jharvey/Cinch_enclosure_template/pictures/modeice_case_iso.jpg

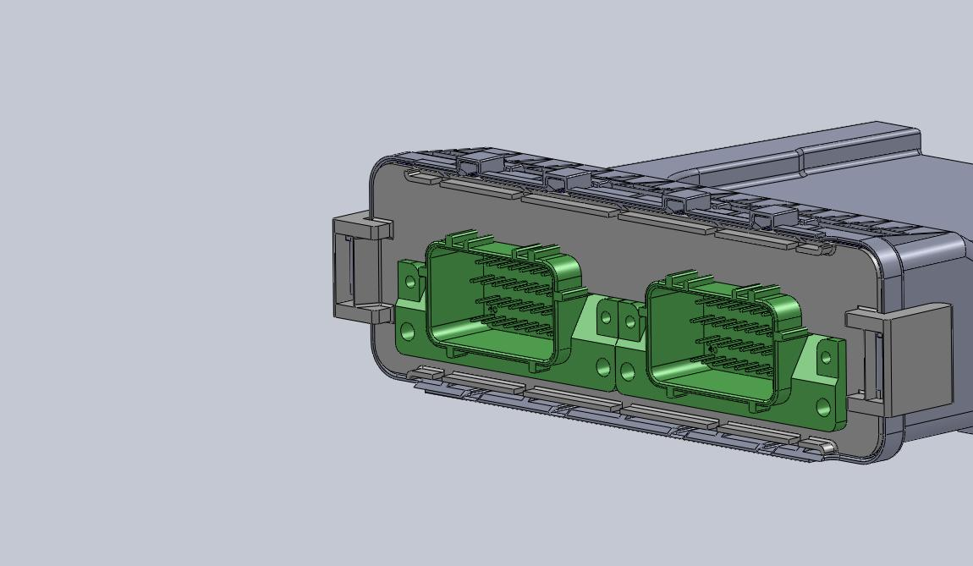
pictures/modeice_case_iso.jpg
