jharvey/Cinch_enclosure_template/pictures/modeice_case_pcb_edge_opening_rubber.jpg

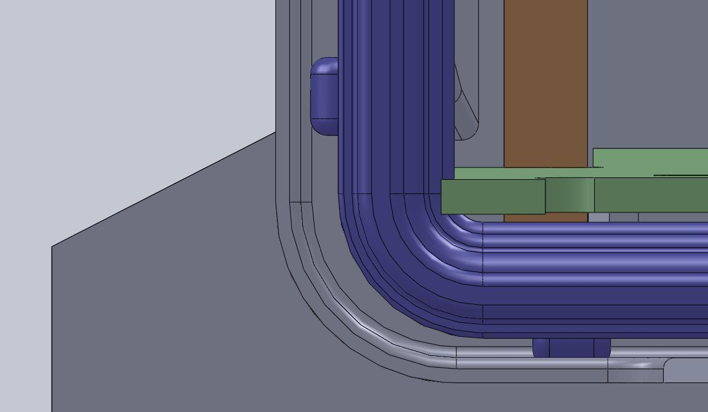
pictures/modeice_case_pcb_edge_opening_rubber.jpg
