jharvey/Cinch_enclosure_template/KICAD_Project/PCB-modules/MPX4100A/puma_topview.png

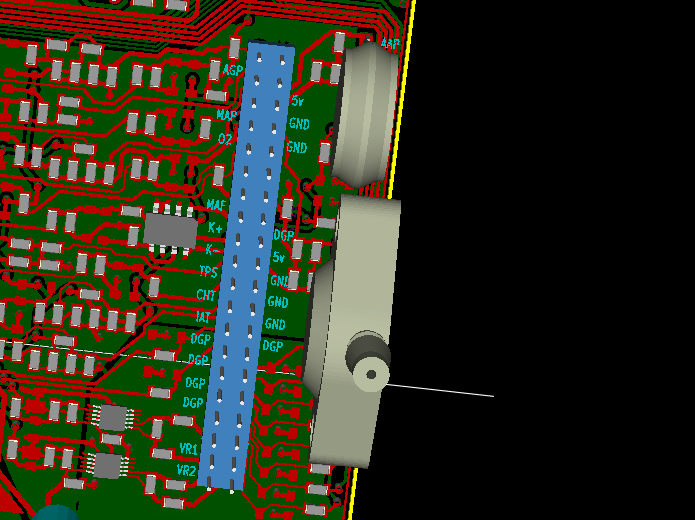
KICAD_Project/PCB-modules/MPX4100A/puma_topview.png
