jharvey/Cinch_enclosure_template/KICAD_Project/PCB-modules/MPX4100A/UNIBODY_CELL.PNG

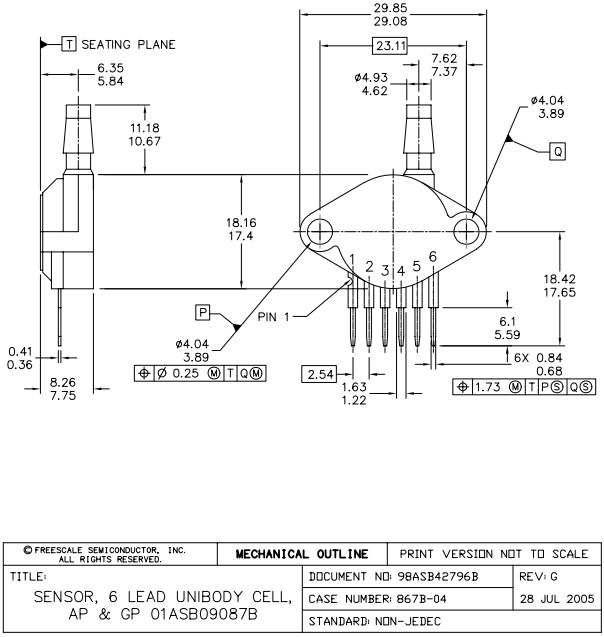
KICAD_Project/PCB-modules/MPX4100A/UNIBODY_CELL.PNG
