jharvey/Cinch_enclosure_template/KICAD_Project/PCB-modules/MPX4100A/UNIBODY_STOVE-PIPE.PNG

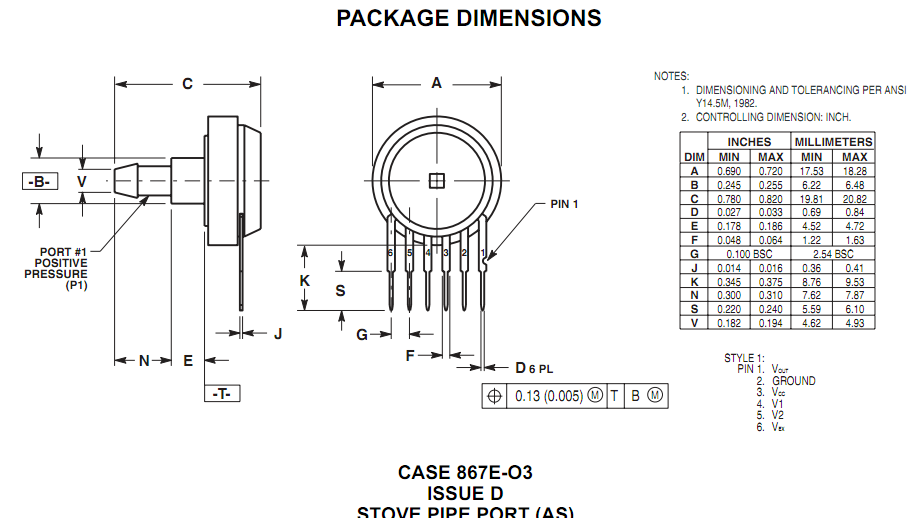
KICAD_Project/PCB-modules/MPX4100A/UNIBODY_STOVE-PIPE.PNG
