jharvey/Cinch_enclosure_template/KICAD_Project/PCB-modules/pololu/0J1418.600.jpg

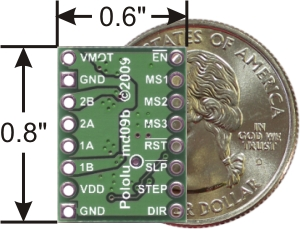
KICAD_Project/PCB-modules/pololu/0J1418.600.jpg
