jharvey/Cinch_enclosure_template/pictures/angled_layout_view.png

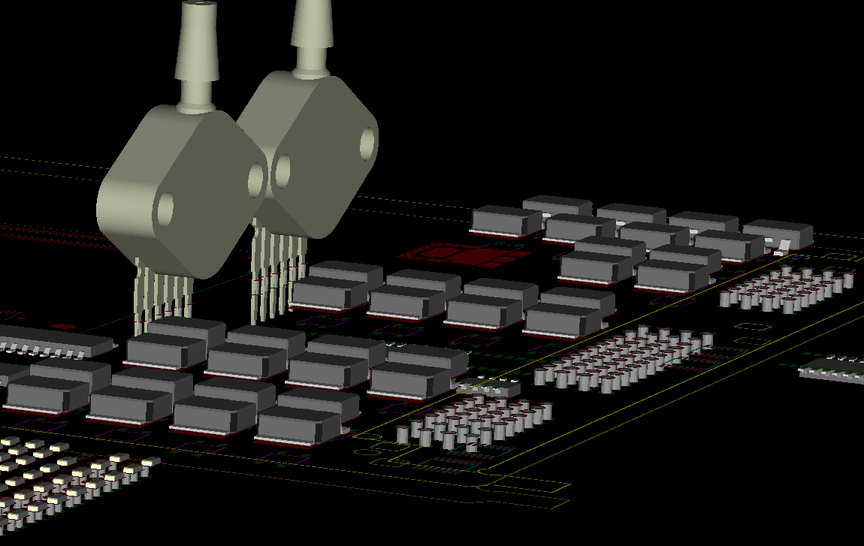
pictures/angled_layout_view.png
