jharvey/Cinch_enclosure_template/pictures/cinch_spring_clips2.png

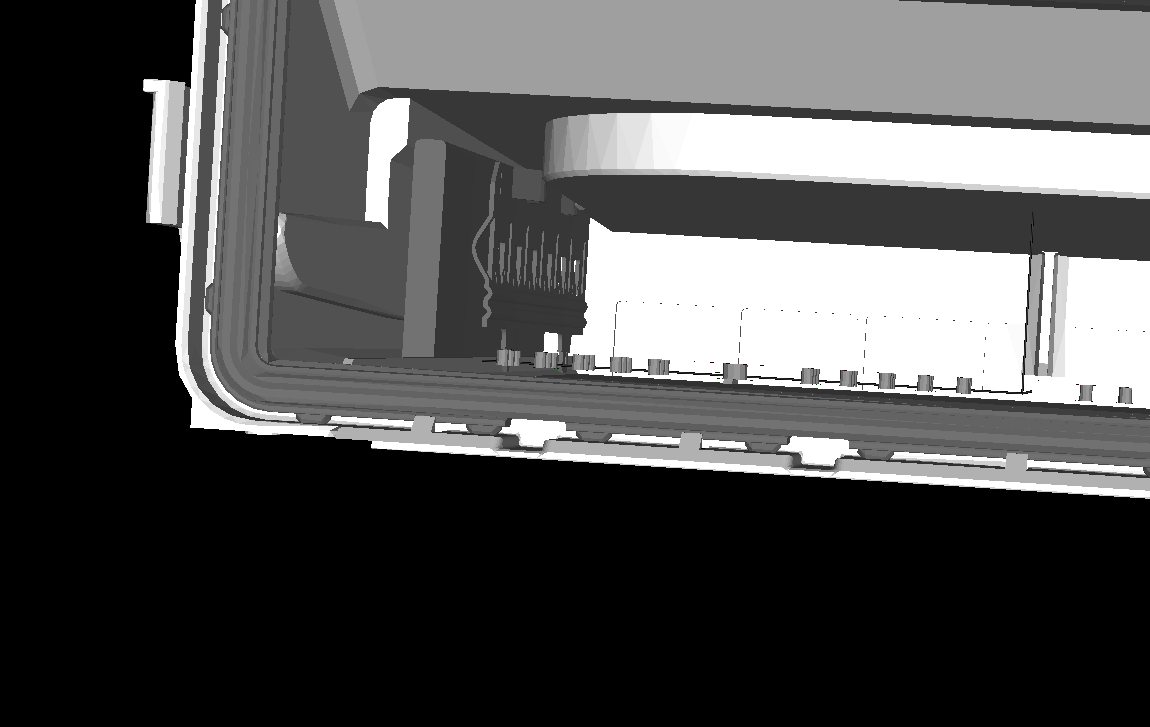
pictures/cinch_spring_clips2.png
