jharvey/Cinch_enclosure_template/pictures/cinch_start.png

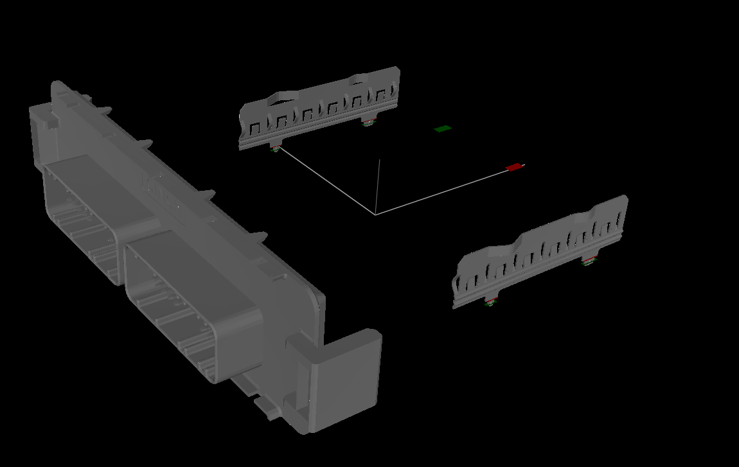
pictures/cinch_start.png
