jharvey/Cinch_enclosure_template/pictures/cinch_start_w-case.png

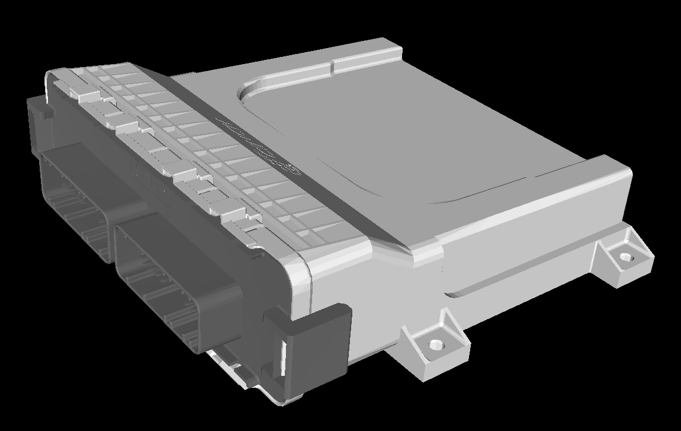
pictures/cinch_start_w-case.png
