jharvey/Cinch_enclosure_template/pictures/GND_PLANE_PCB_DRAFT.PNG

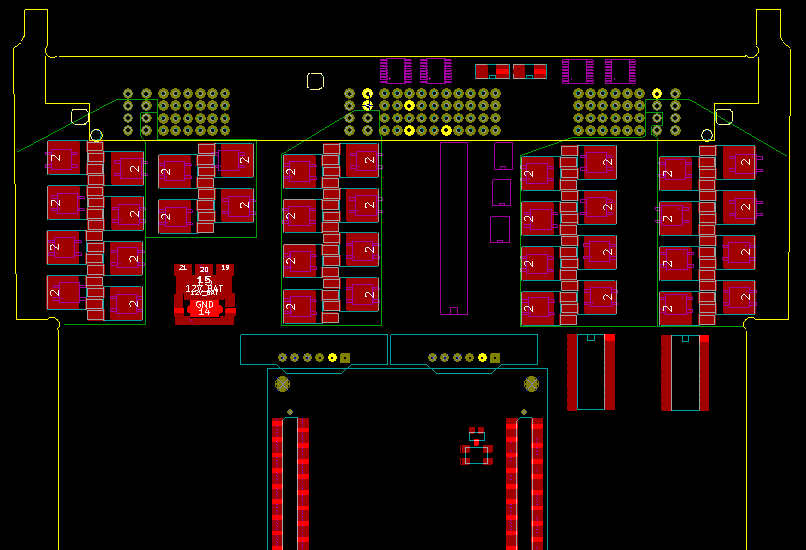
pictures/GND_PLANE_PCB_DRAFT.PNG
