jharvey/Cinch_enclosure_template/pictures/INJ-IGN_opto-drive.PNG

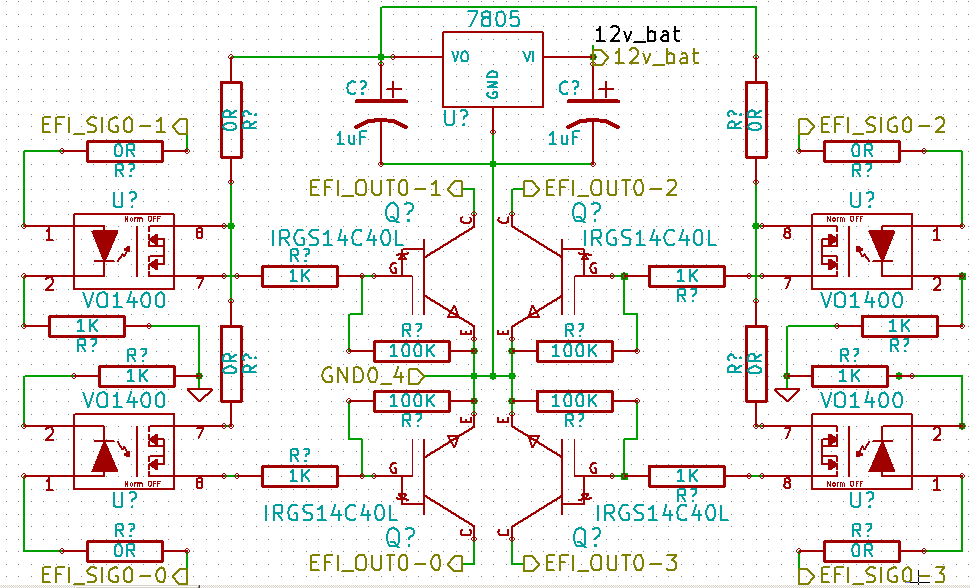
pictures/INJ-IGN_opto-drive.PNG
