jharvey/Cinch_enclosure_template/pictures/layout_top_view.PNG

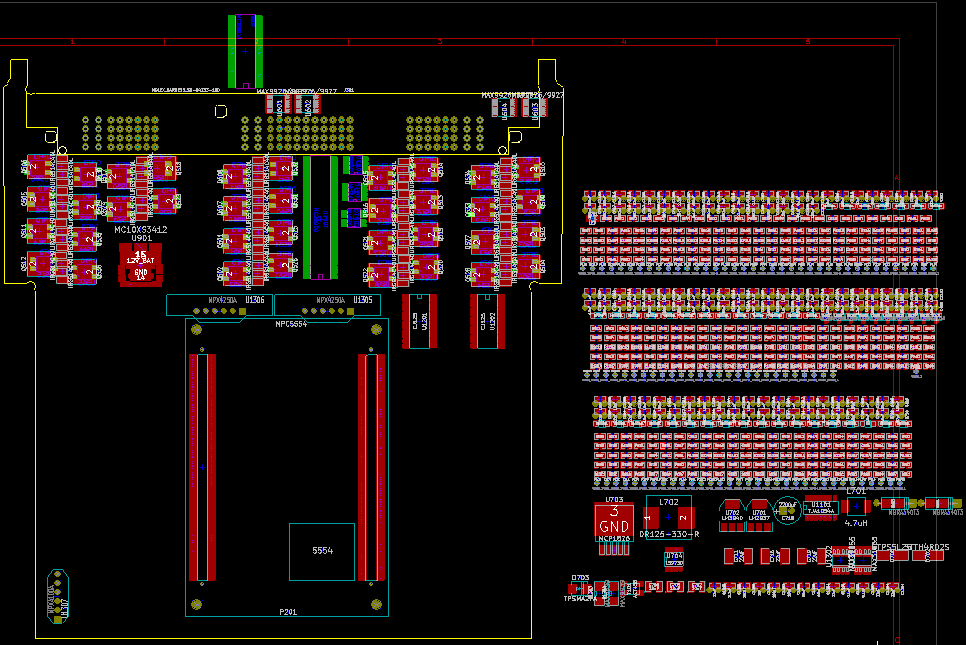
pictures/layout_top_view.PNG
