jharvey/Cinch_enclosure_template/pictures/layout_top_view_2.PNG

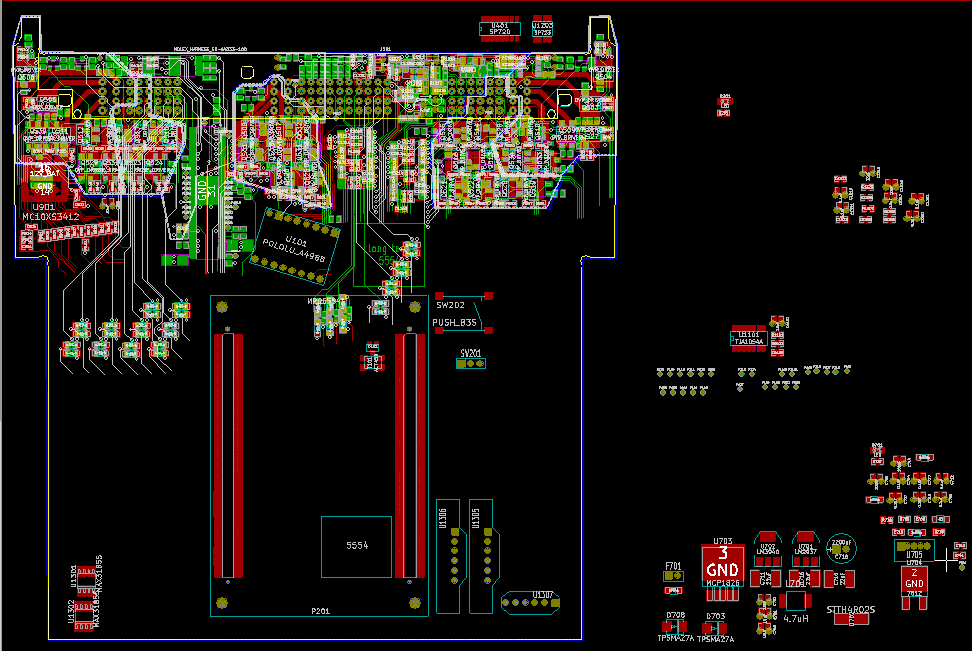
pictures/layout_top_view_2.PNG
