jharvey/Cinch_enclosure_template/pictures/modeice_case_face_plate_cut.jpg

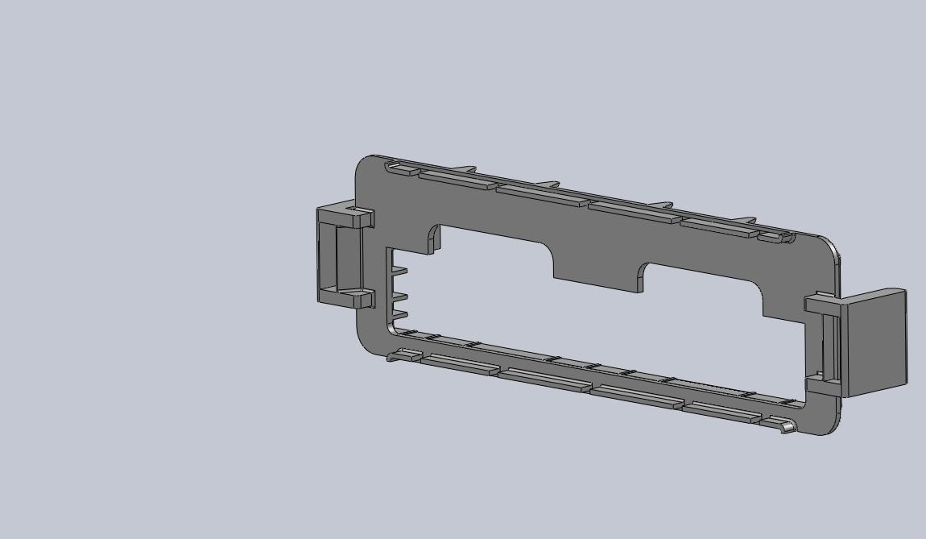
pictures/modeice_case_face_plate_cut.jpg
