jharvey/Cinch_enclosure_template/pictures/modeice_case_iso1.jpg

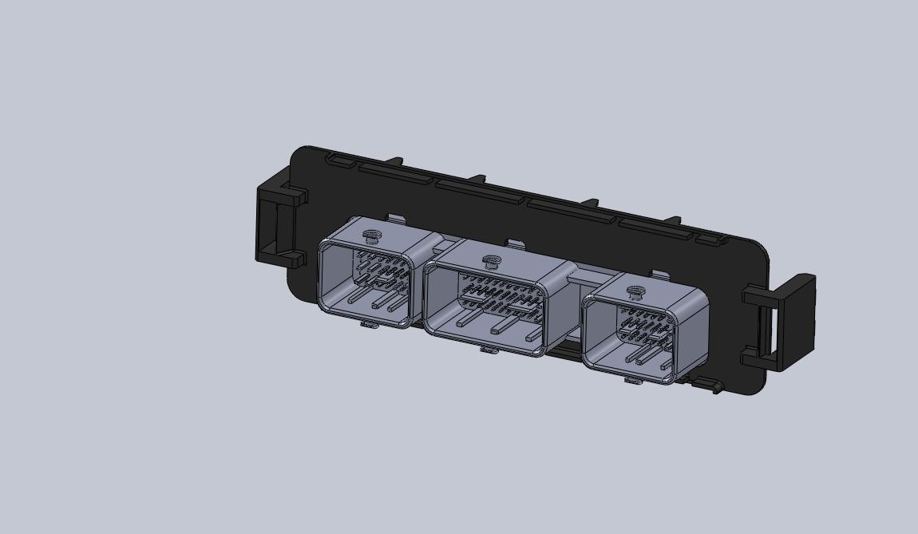
pictures/modeice_case_iso1.jpg
