jharvey/Cinch_enclosure_template/pictures/modeice_case_iso2.jpg

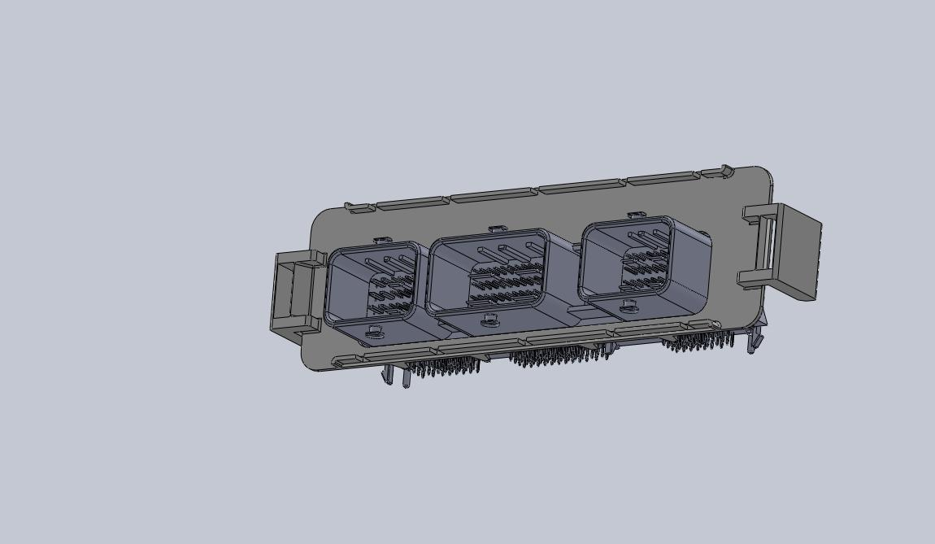
pictures/modeice_case_iso2.jpg
