jharvey/Cinch_enclosure_template/pictures/modeice_case_iso_cut.jpg

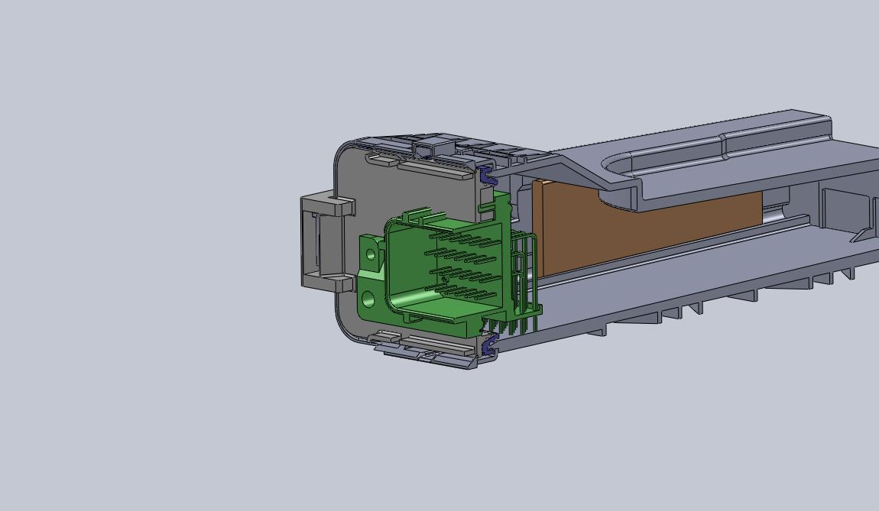
pictures/modeice_case_iso_cut.jpg
