jharvey/Cinch_enclosure_template/pictures/modeice_case_pcb_edge_opening.jpg

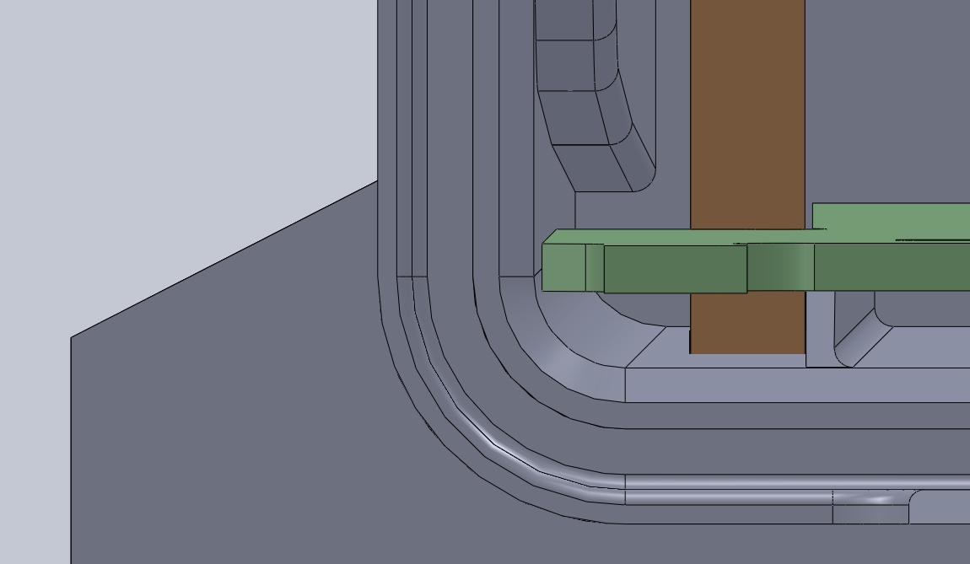
pictures/modeice_case_pcb_edge_opening.jpg
