jharvey/Cinch_enclosure_template/pictures/modeice_case_wpcb.jpg

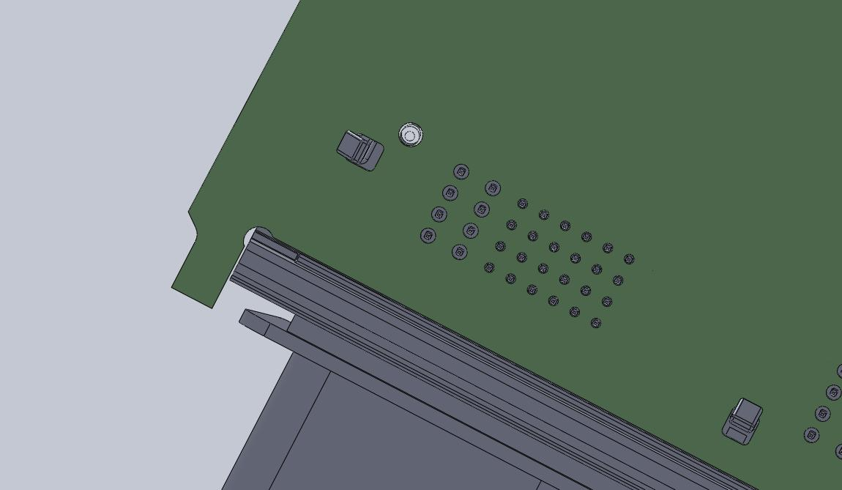
pictures/modeice_case_wpcb.jpg
