jharvey/Cinch_enclosure_template/pictures/molex_connectors_iso.PNG

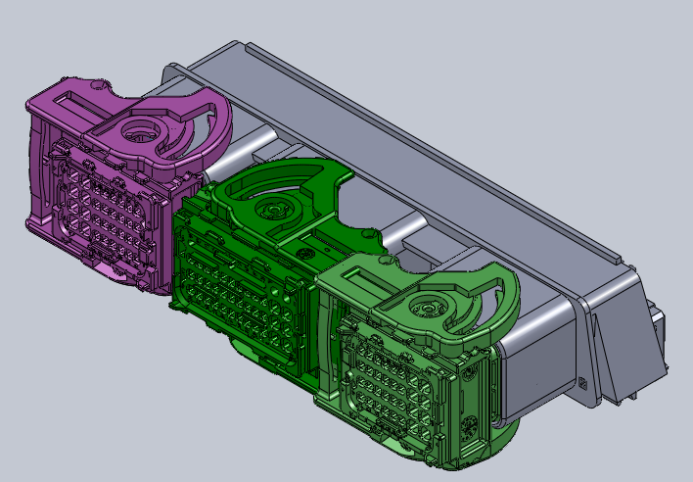
pictures/molex_connectors_iso.PNG
