jharvey/Cinch_enclosure_template/pictures/pcb_layout_1.PNG

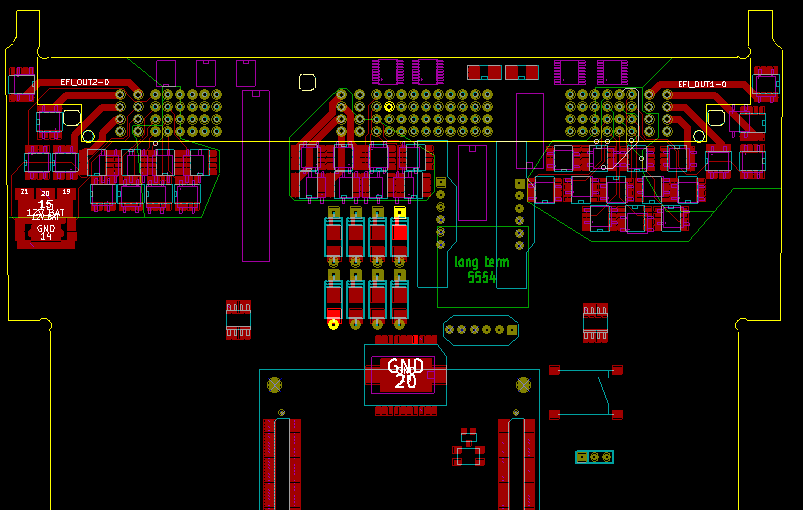
pictures/pcb_layout_1.PNG
