jharvey/Cinch_enclosure_template/pictures/PCB_outline_112-harness_200-SOM.PNG

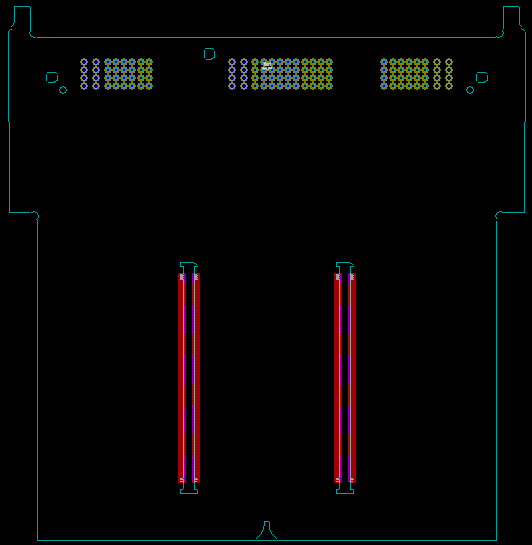
pictures/PCB_outline_112-harness_200-SOM.PNG
