jharvey/Cinch_enclosure_template/pictures/som_top_view.jpg

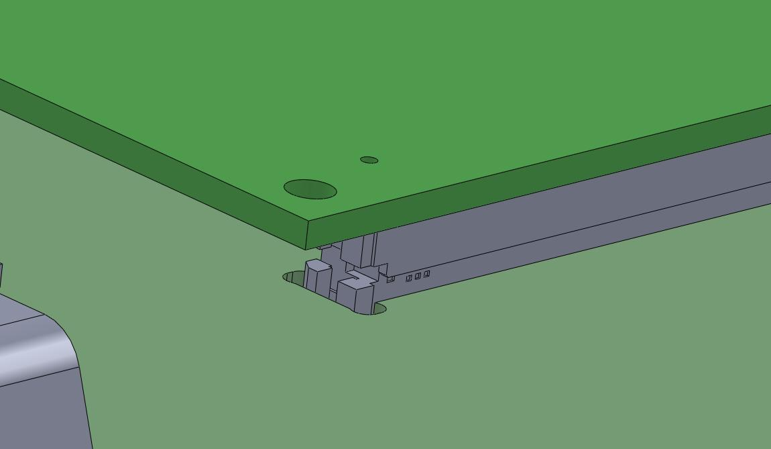
pictures/som_top_view.jpg
