jharvey/Cinch_enclosure_template/pictures/som_top_view_2.jpg

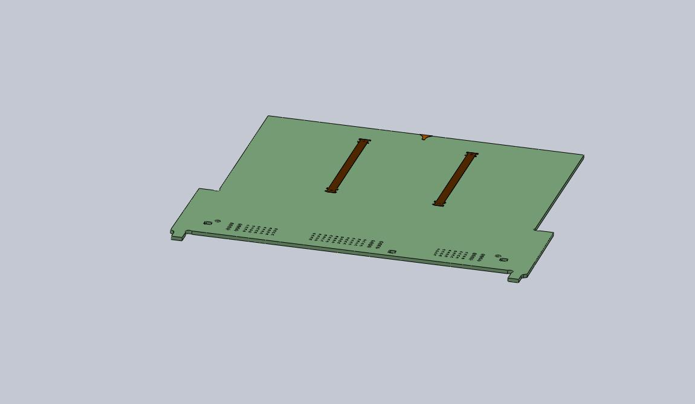
pictures/som_top_view_2.jpg
