jharvey/Cinch_enclosure_template/pictures/som_top_view_3.jpg

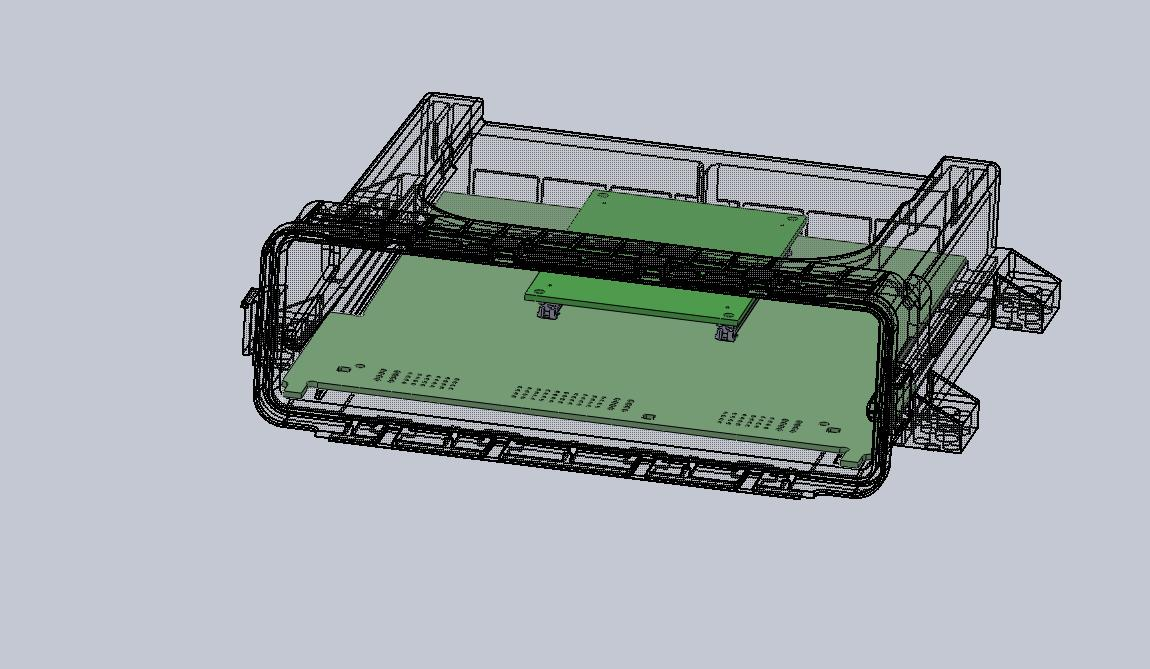
pictures/som_top_view_3.jpg
