jharvey/Cinch_enclosure_template/simulation/picture_docs/12V_short.png

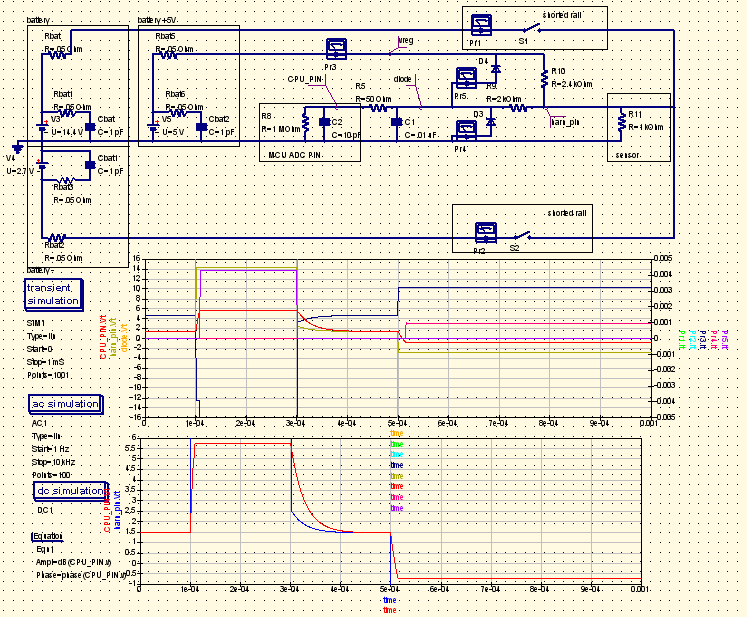
simulation/picture_docs/12V_short.png
