jharvey/Cinch_enclosure_template/simulation/picture_docs/40V-OVP_HighZ_injector_simulation_4-watts.PNG

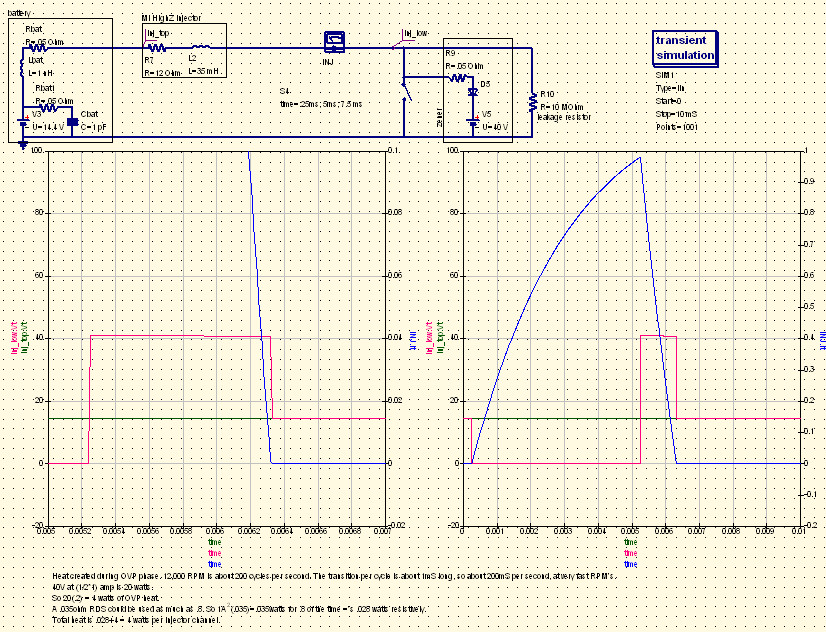
simulation/picture_docs/40V-OVP_HighZ_injector_simulation_4-watts.PNG
