jharvey/Cinch_enclosure_template/simulation/picture_docs/70V-OVP_HighZ_injector_simulation_4.2-watts.PNG

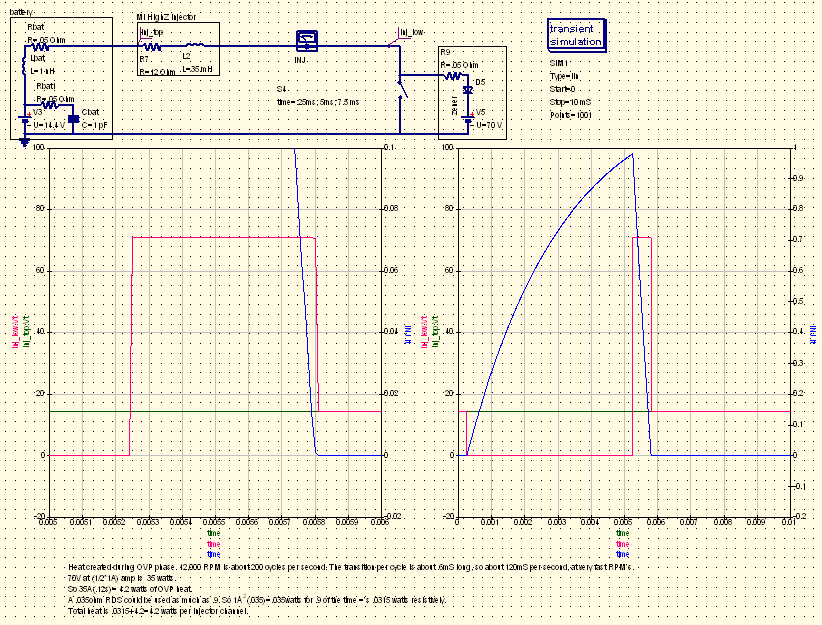
simulation/picture_docs/70V-OVP_HighZ_injector_simulation_4.2-watts.PNG
