jharvey/Cinch_enclosure_template/simulation/picture_docs/AN_protect_AC-sim.png

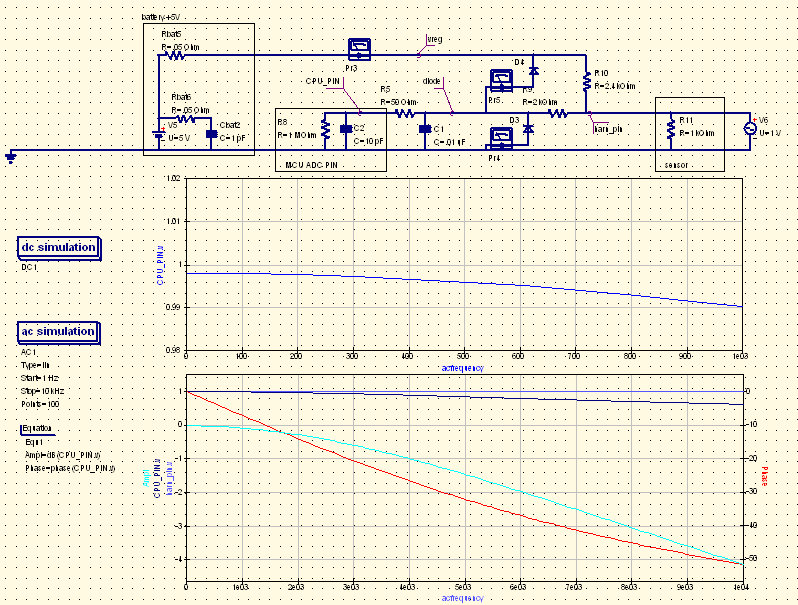
simulation/picture_docs/AN_protect_AC-sim.png
