jharvey/Cinch_enclosure_template/simulation/picture_docs/DI_2.PNG

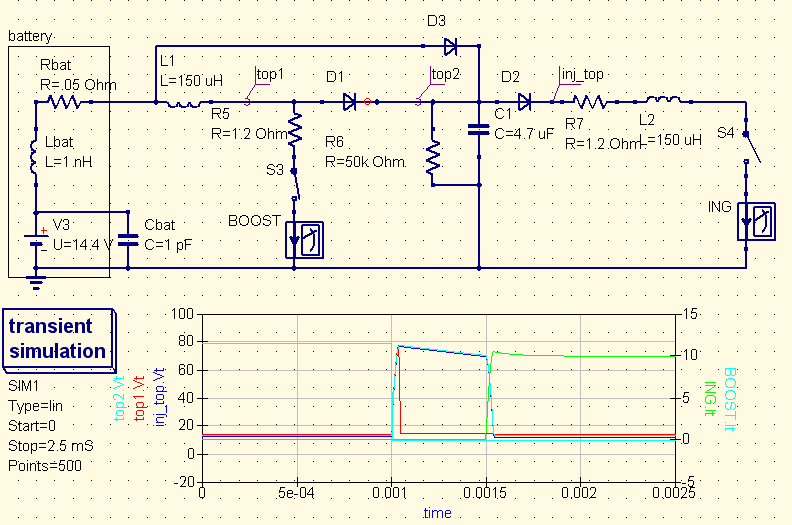
simulation/picture_docs/DI_2.PNG
