jharvey/Cinch_enclosure_template/simulation/picture_docs/DI_3.PNG

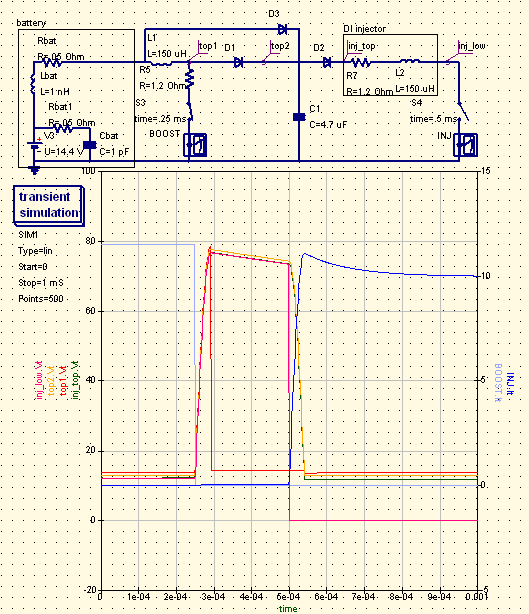
simulation/picture_docs/DI_3.PNG
