jharvey/Cinch_enclosure_template/simulation/picture_docs/pin_protect_1.PNG

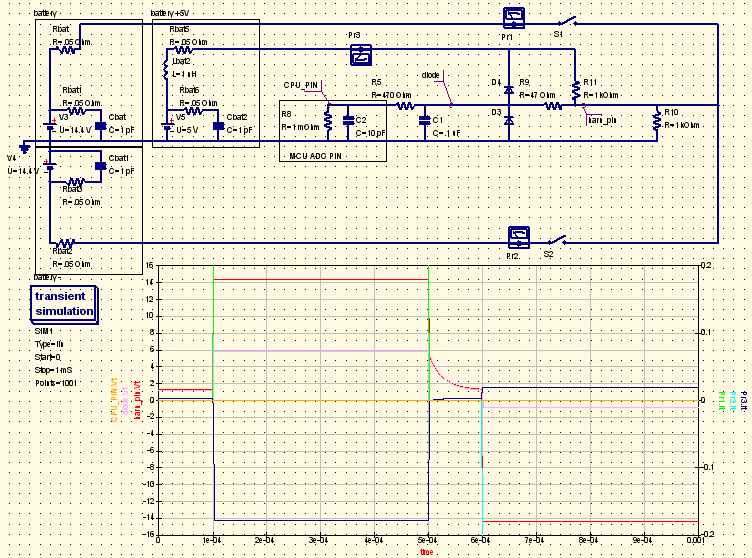
simulation/picture_docs/pin_protect_1.PNG
