jharvey/Cinch_enclosure_template/simulation/picture_docs/pin_protect_2.PNG

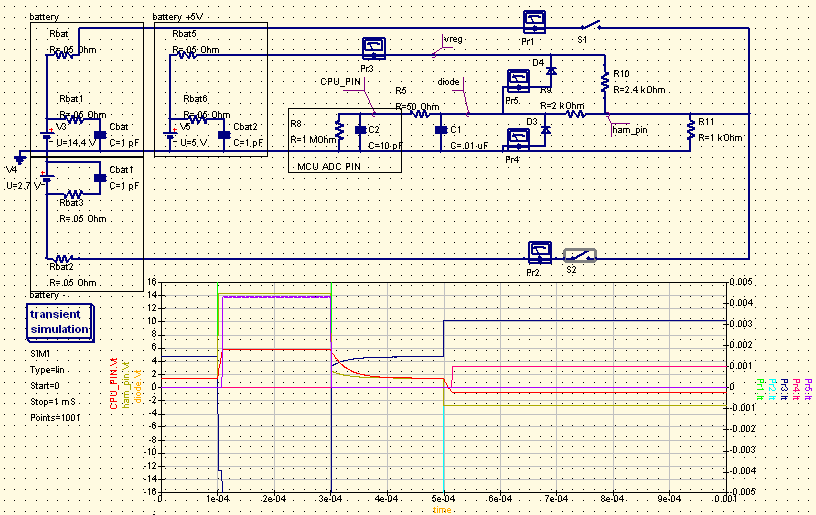
simulation/picture_docs/pin_protect_2.PNG
