jharvey/Cinch_enclosure_template/simulation/picture_docs/Snubbed_HighZ_injector_simulation.PNG

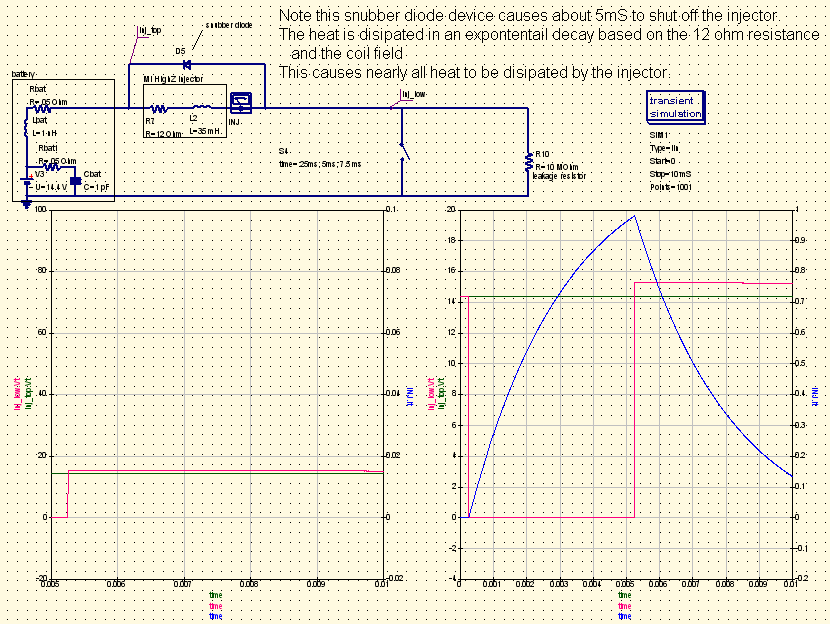
simulation/picture_docs/Snubbed_HighZ_injector_simulation.PNG
