jharvey/Cinch_enclosure_template/pictures/8-pin_64333-100_footprint_builder.PNG

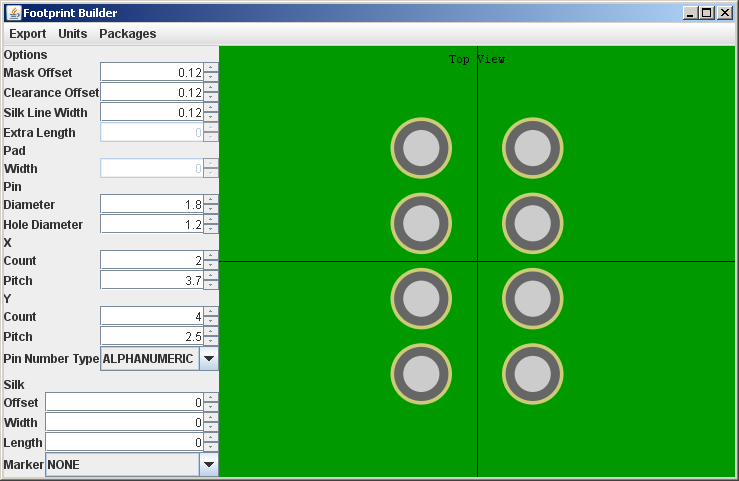
pictures/8-pin_64333-100_footprint_builder.PNG
