jharvey/Cinch_enclosure_template/pictures/40-pin_64333-100_footprint_builder.PNG

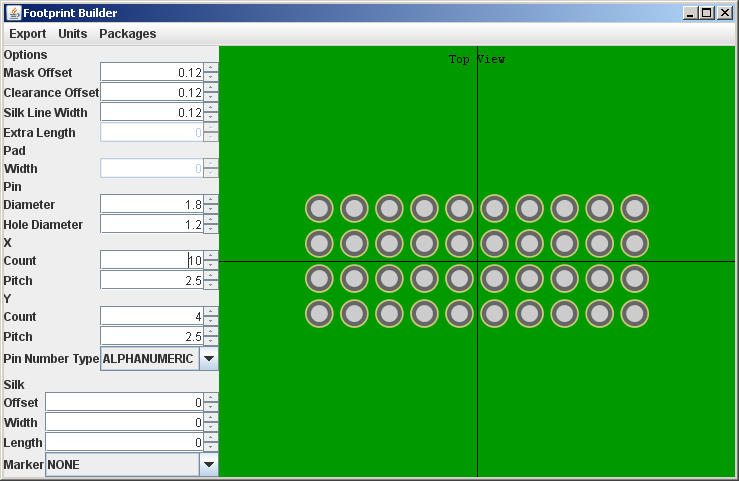
pictures/40-pin_64333-100_footprint_builder.PNG
