jharvey/Cinch_enclosure_template/pictures/200_pins_53467_footprint_builder.PNG

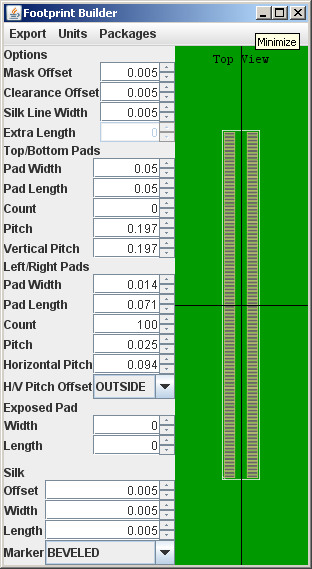
pictures/200_pins_53467_footprint_builder.PNG
