jharvey/Cinch_enclosure_template/pictures/molex_connectors_problem.PNG

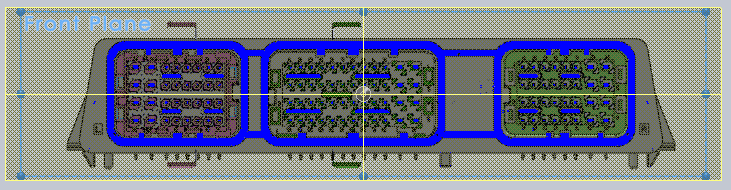
pictures/molex_connectors_problem.PNG
