jharvey/Cinch_enclosure_template/KICAD_Project/cinch_start.sch

## KiCad design KICAD_Project/cinch_start.sch (2011-10-27)

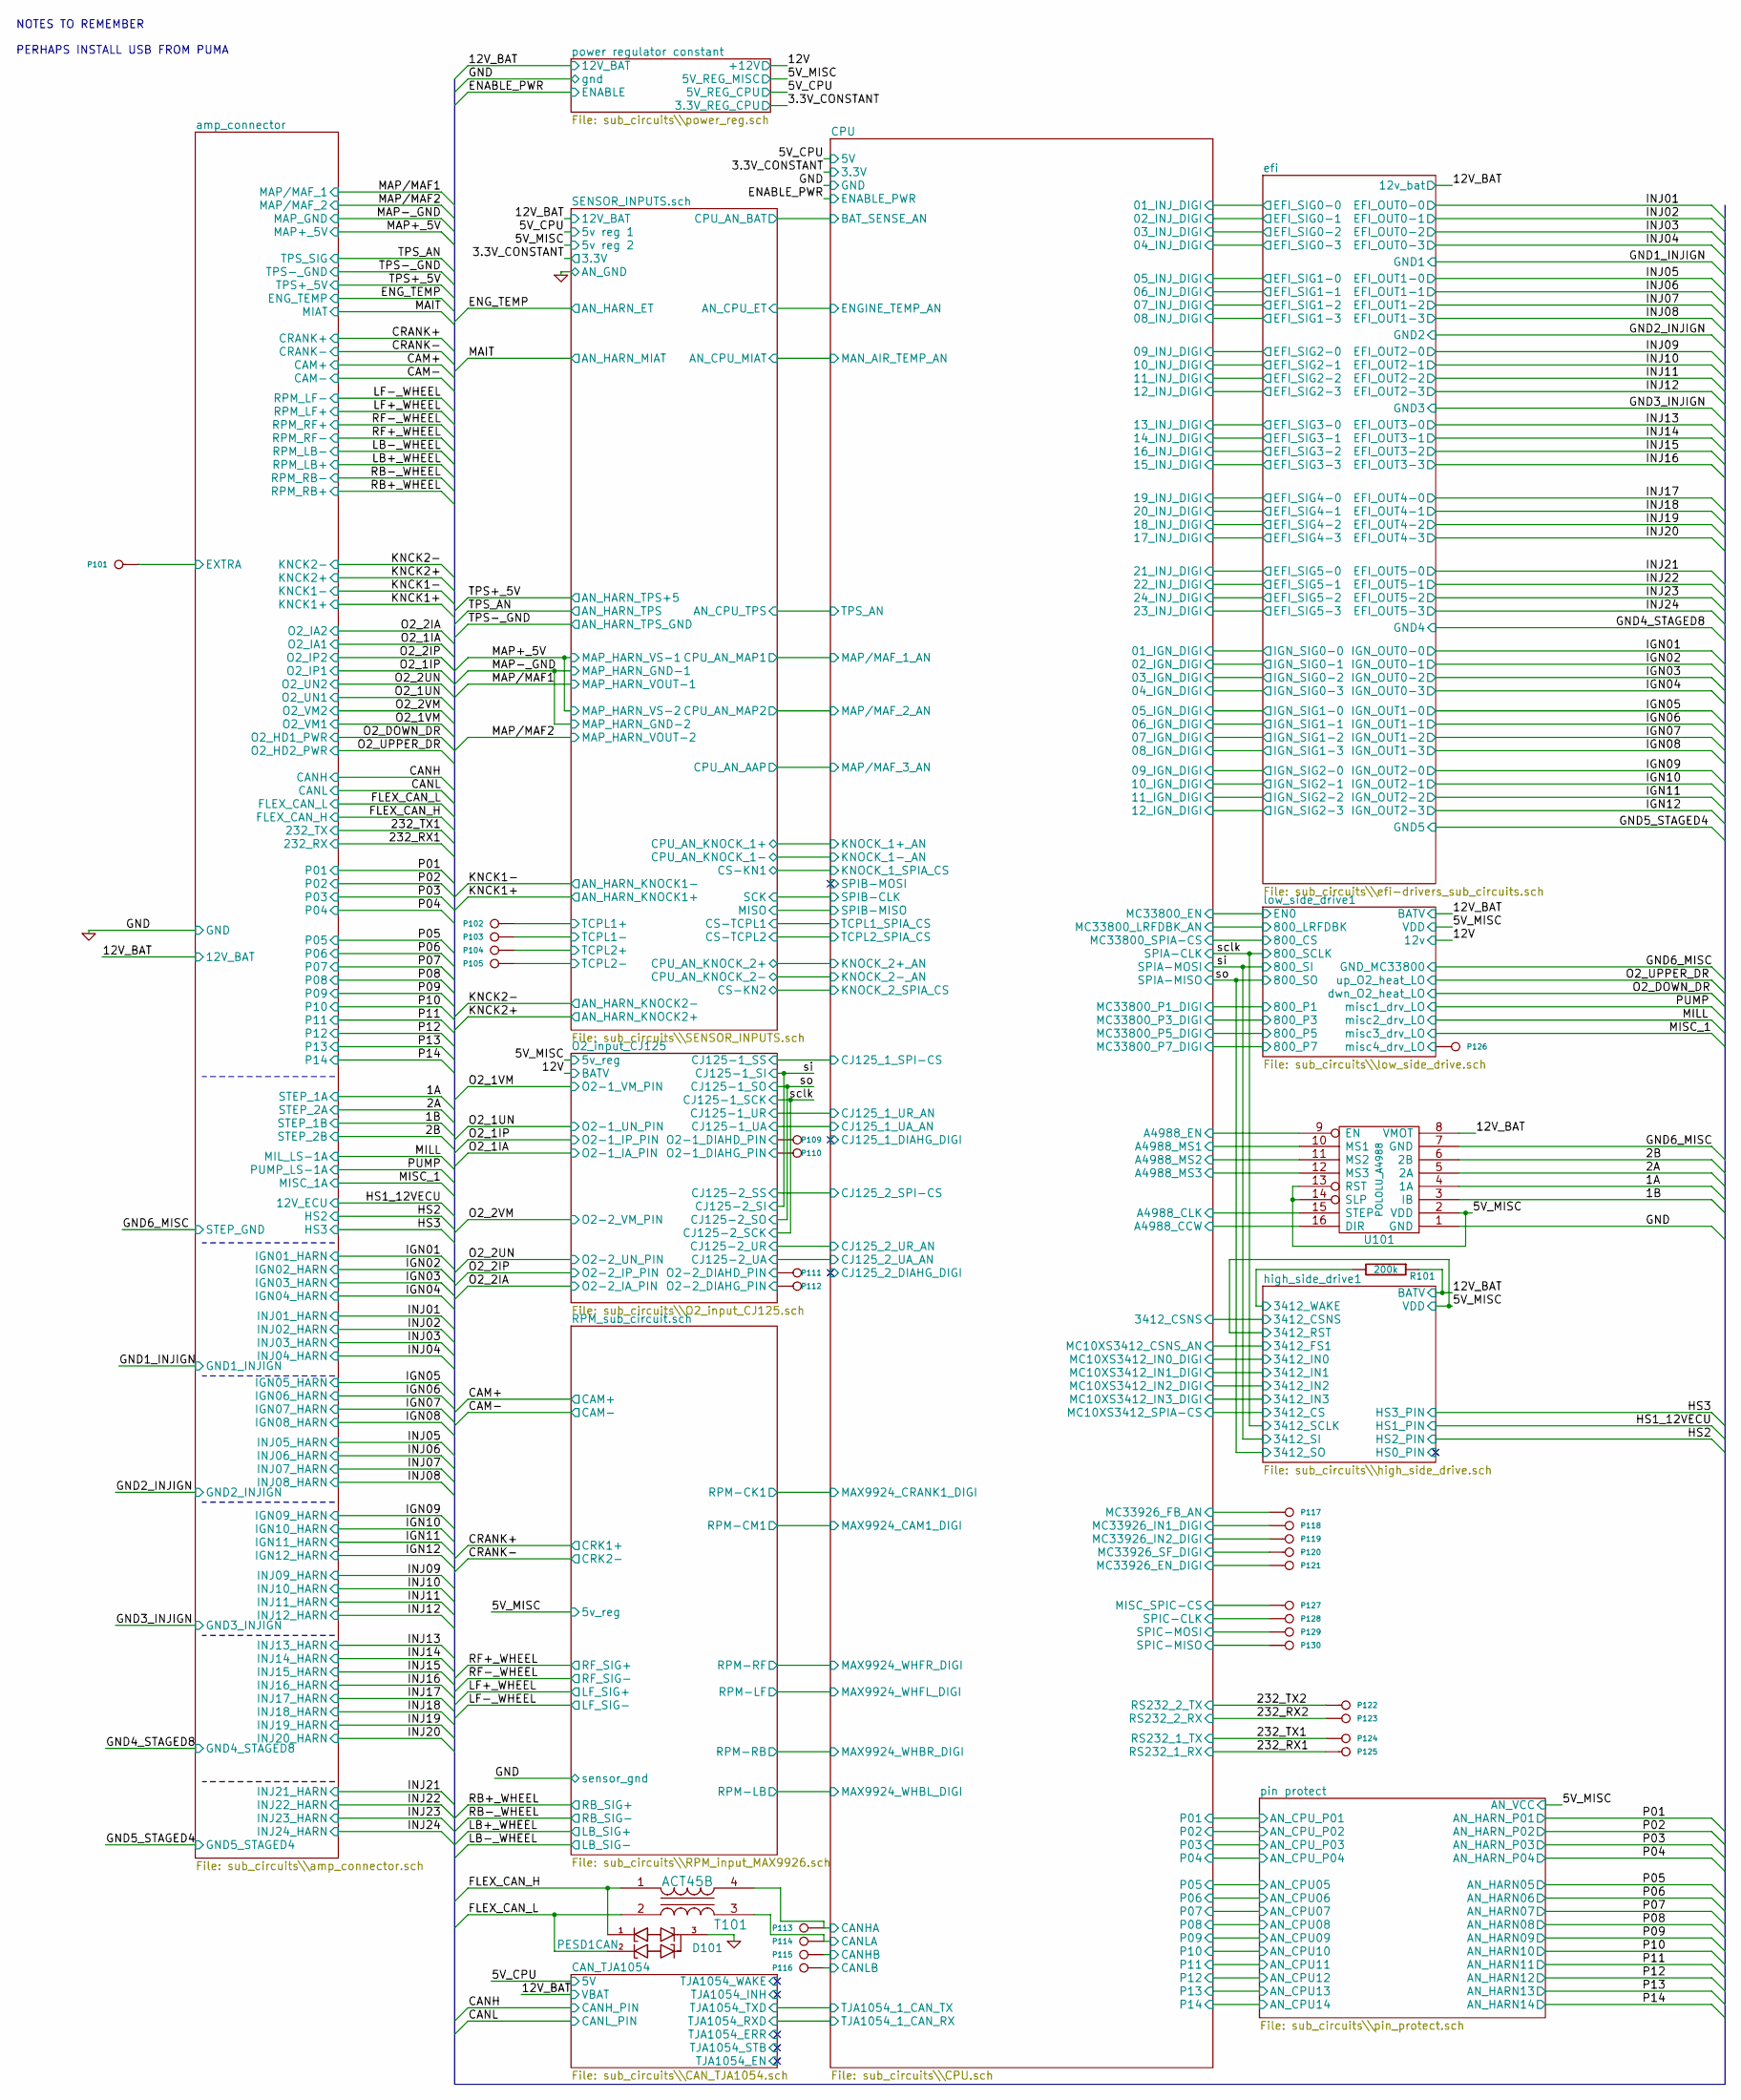
[picture p79: schematic cinch_start.sch]

Parts:
D101: PESD1CAN; SOT23-3
P101, P102, P103, P104, P105, P109, P110, P111, P112, P113, P114, P115, P116, P117, P118, P119, P120, P121, P122, P123, P124, P125, P126, P127, P128, P129, P130: CONN_1; PINTST
R101: 200k; SM0805
T101: ACT45B
U101: POLOLU_A4988; SWDIP8_.6W

Connections:
1A: U101.4 (1A)
1B: U101.3 (IB)
2A: U101.5 (2A)
2B: U101.6 (2B)
5V_MISC: U101.2 (VDD), U101.13 (RST), U101.14 (SLP)
12V_BAT: R101.1, U101.8 (VMOT)
232_RX1: P125.1
232_RX2: P123.1
232_TX1: P124.1
232_TX2: P122.1
3412_WAKE: R101.2
A4988_CCW: U101.16 (DIR)
A4988_CLK: U101.15 (STEP)
A4988_EN: U101.9 (EN)
A4988_MS1: U101.10 (MS1)
A4988_MS2: U101.11 (MS2)
A4988_MS3: U101.12 (MS3)
CANHA: P113.1, T101.4
CANHB: P115.1
CANLA: P114.1, T101.3
CANLB: P116.1
EXTRA: P101.1
FLEX_CAN_H: D101.1, T101.1
FLEX_CAN_L: D101.2, T101.2
GND: D101.3, U101.1 (GND)
GND6_MISC: U101.7 (GND)
MC33926_EN_DIGI: P121.1
MC33926_FB_AN: P117.1
MC33926_IN1_DIGI: P118.1
MC33926_IN2_DIGI: P119.1
MC33926_SF_DIGI: P120.1
MISC_SPIC-CS: P127.1
O2-1_DIAHD_PIN: P109.1
O2-1_DIAHG_PIN: P110.1
O2-2_DIAHD_PIN: P111.1
O2-2_DIAHG_PIN: P112.1
SPIC-CLK: P128.1
SPIC-MISO: P130.1
SPIC-MOSI: P129.1
TCPL1+: P102.1
TCPL1-: P103.1
TCPL2+: P104.1
TCPL2-: P105.1
misc4_drv_LO: P126.1

Notes on the sheet:
NOTES TO REMEMBER PERHAPS INSTALL USB FROM PUMA
