jharvey/Cinch_enclosure_template/KICAD_Project/sub_circuits/CAN_TJA1054.sch

## KiCad design KICAD_Project/sub_circuits/CAN_TJA1054.sch (2011-10-27)

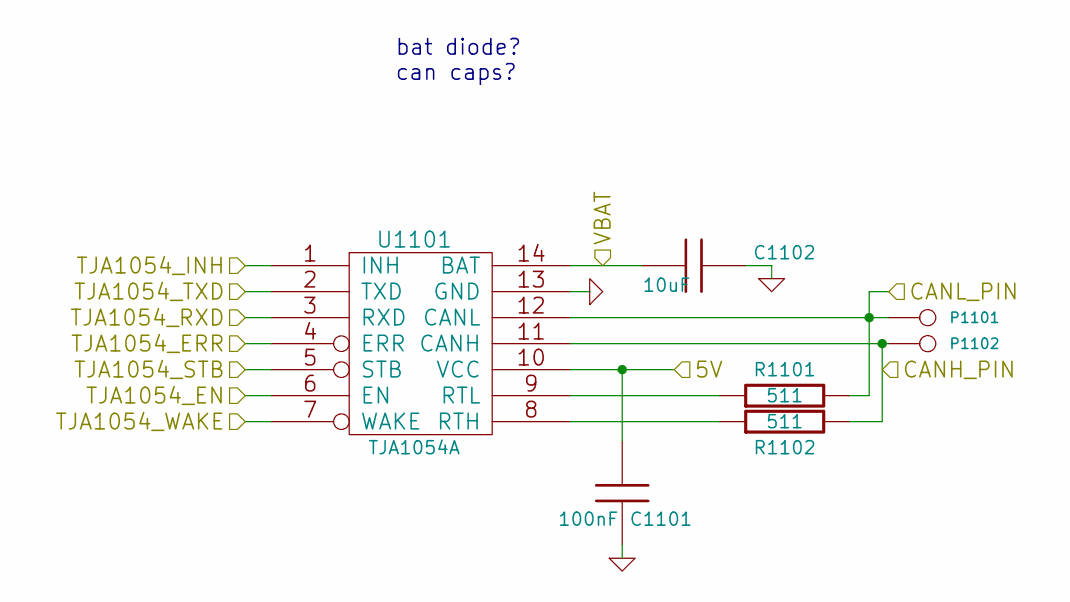
[picture p80: schematic CAN_TJA1054.sch]

Parts:
C1101: 100nF; SM0805
C1102: 10uF; SM0805; tolerance 10%
P1101, P1102: CONN_1; PINTST
R1101, R1102: 511; SM0805
U1101: TJA1054A; SO14E

Connections:
5V: C1101.2, U1101.10 (VCC)
CANH_PIN: P1102.1, R1102.2, U1101.11 (CANH)
CANL_PIN: P1101.1, R1101.2, U1101.12 (CANL)
GND: C1101.1, C1102.1, U1101.13 (GND)
unnamed: R1101.1, U1101.9 (RTL)
unnamed: R1102.1, U1101.8 (RTH)
TJA1054_EN: U1101.6 (EN)
TJA1054_ERR: U1101.4 (ERR)
TJA1054_INH: U1101.1 (INH)
TJA1054_RXD: U1101.3 (RXD)
TJA1054_STB: U1101.5 (STB)
TJA1054_TXD: U1101.2 (TXD)
TJA1054_WAKE: U1101.7 (WAKE)
VBAT: C1102.2, U1101.14 (BAT)

Notes on the sheet:
bat diode? can caps?
