jharvey/Cinch_enclosure_template/KICAD_Project/sub_circuits/CPU.sch

## KiCad design KICAD_Project/sub_circuits/CPU.sch (2011-10-27)

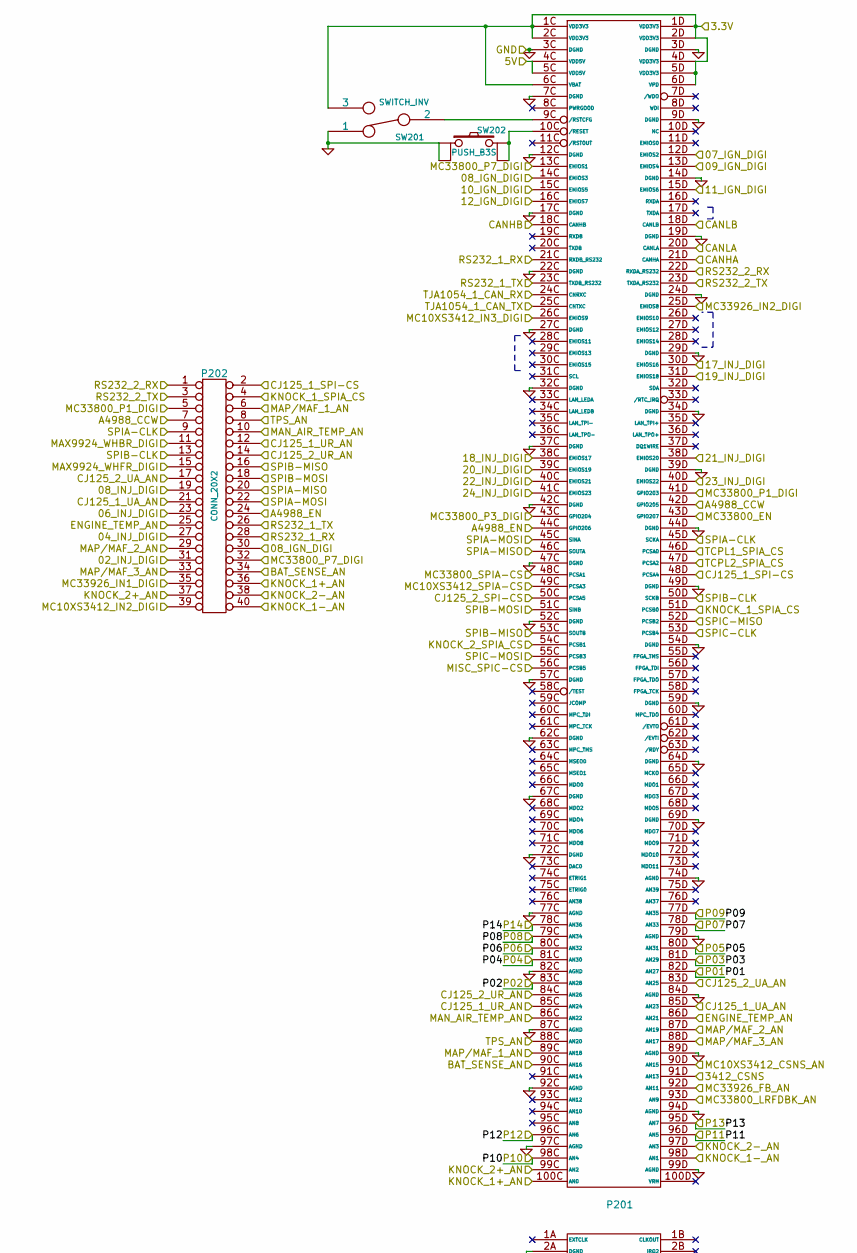
[picture p81: schematic CPU.sch, part in row 1, column 1]

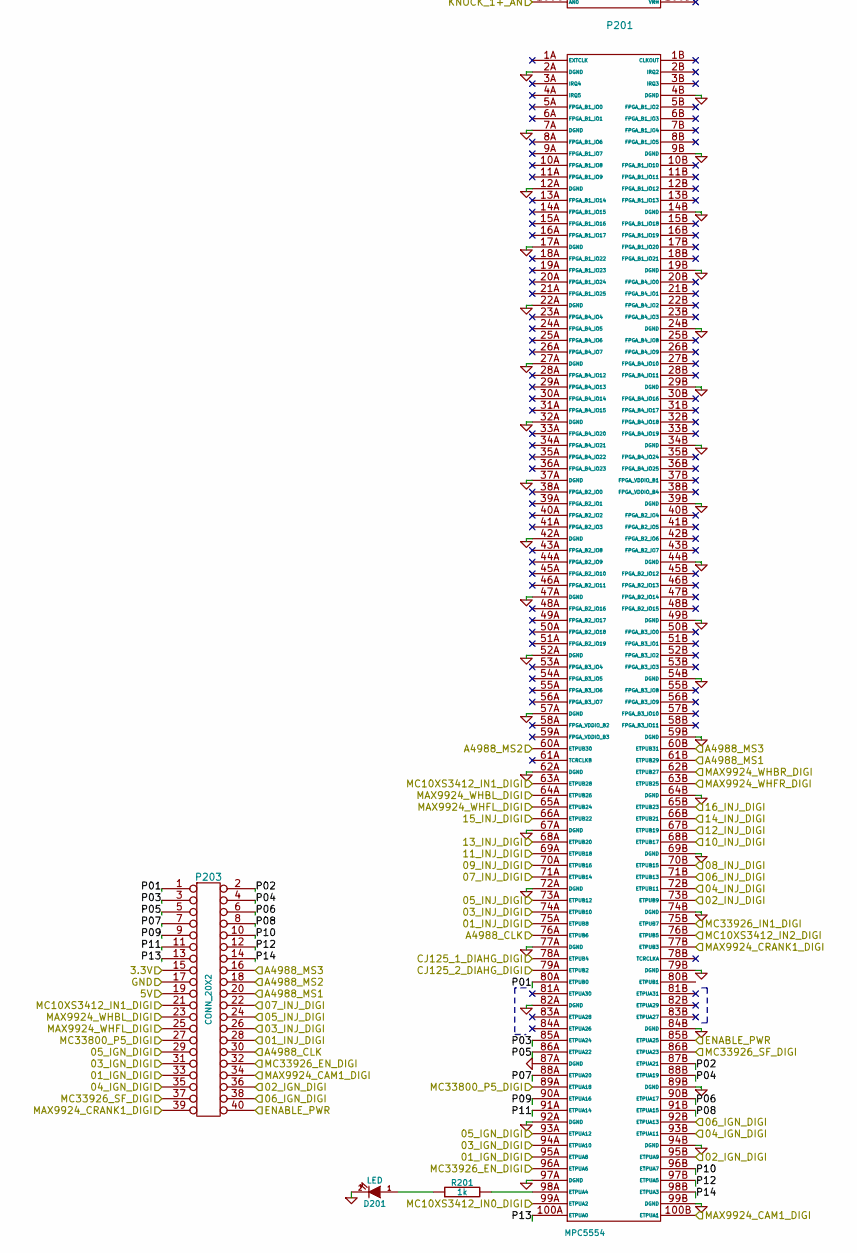
[picture p82: schematic CPU.sch, part in row 2, column 1]

Parts:
D201: LED; LED-0805
P201: MPC5554; phyCORE-MPC5554
P202, P203: CONN_20X2; PIN_ARRAY_20X2
R201: 1k; SM0805
SW201: SWITCH_INV; SIL-3
SW202: PUSH_B3S; B3S

Connections:
01_IGN_DIGI: P201.95A (ETPUA8), P203.33
01_INJ_DIGI: P201.75A (ETPUB8), P203.28
02_IGN_DIGI: P201.95B (ETPUA9), P203.36
02_INJ_DIGI: P201.73B (ETPUB9), P202.31
3.3V: P201.1C (VDD3V3), P201.1D (VDD3V3), P201.2C (VDD3V3), P201.2D (VDD3V3), P201.4D (VDD3V3), P201.5D (VDD3V3), P201.6C (VBAT), P201.6D (VPD), P203.15, SW201.3
03_IGN_DIGI: P201.94A (ETPUA10), P203.31
03_INJ_DIGI: P201.74A (ETPUB10), P203.26
04_IGN_DIGI: P201.93B (ETPUA11), P203.35
04_INJ_DIGI: P201.72B (ETPUB11), P202.27
5V: P201.4C (VDD5V), P201.5C (VDD5V), P203.19
05_IGN_DIGI: P201.93A (ETPUA12), P203.29
05_INJ_DIGI: P201.73A (ETPUB12), P203.24
06_IGN_DIGI: P201.92B (ETPUA13), P203.38
06_INJ_DIGI: P201.71B (ETPUB13), P202.23
07_IGN_DIGI: P201.12D (EMIOS2)
07_INJ_DIGI: P201.71A (ETPUB14), P203.22
08_IGN_DIGI: P201.14C (EMIOS3), P202.30
08_INJ_DIGI: P201.70B (ETPUB15), P202.19
09_IGN_DIGI: P201.13D (EMIOS4)
09_INJ_DIGI: P201.70A (ETPUB16)
10_IGN_DIGI: P201.15C (EMIOS5)
10_INJ_DIGI: P201.68B (ETPUB17)
11_IGN_DIGI: P201.15D (EMIOS6)
11_INJ_DIGI: P201.69A (ETPUB18)
12_IGN_DIGI: P201.16C (EMIOS7)
12_INJ_DIGI: P201.67B (ETPUB19)
13_INJ_DIGI: P201.68A (ETPUB20)
14_INJ_DIGI: P201.66B (ETPUB21)
15_INJ_DIGI: P201.66A (ETPUB22)
16_INJ_DIGI: P201.65B (ETPUB23)
17_INJ_DIGI: P201.30D (EMIOS16)
18_INJ_DIGI: P201.38C (EMIOS17)
19_INJ_DIGI: P201.31D (EMIOS18)
20_INJ_DIGI: P201.39C (EMIOS19)
21_INJ_DIGI: P201.38D (EMIOS20)
22_INJ_DIGI: P201.40C (EMIOS21)
23_INJ_DIGI: P201.40D (EMIOS22)
24_INJ_DIGI: P201.41C (EMIOS23)
3412_CSNS: P201.91D (AN13)
A4988_CCW: P201.42D (GPIO205), P202.7
A4988_CLK: P201.76A (ETPUB6), P203.30
A4988_EN: P201.44C (GPIO206), P202.24
A4988_MS1: P201.61B (ETPUB29), P203.20
A4988_MS2: P201.60A (ETPUB30), P203.18
A4988_MS3: P201.60B (ETPUB31), P203.16
BAT_SENSE_AN: P201.90C (AN16), P202.34
CANHA: P201.21D (CANHA)
CANHB: P201.18C (CANHB)
CANLA: P201.20D (CANLA)
CANLB: P201.18D (CANLB)
CJ125_1_DIAHG_DIGI: P201.78A (ETPUB4)
CJ125_1_SPI-CS: P201.48D (PCSA4), P202.2
CJ125_1_UA_AN: P201.85D (AN23), P202.21
CJ125_1_UR_AN: P201.85C (AN24), P202.12
CJ125_2_DIAHG_DIGI: P201.79A (ETPUB2)
CJ125_2_SPI-CS: P201.50C (PCSA5)
CJ125_2_UA_AN: P201.83D (AN25), P202.17
CJ125_2_UR_AN: P201.84C (AN26), P202.14
ENABLE_PWR: P201.85B (ETPUA25), P203.40
ENGINE_TEMP_AN: P201.86D (AN21), P202.25
GND: D201.2 (K), P201.2A (DGND), P201.3C (DGND), P201.3D (DGND), P201.4B (DGND), P201.7A (DGND), P201.7C (DGND), P201.9B (DGND), P201.9D (DGND), P201.12A (DGND), P201.12C (DGND), P201.14B (DGND), P201.14D (DGND), P201.17A (DGND), P201.17C (DGND), P201.19B (DGND), P201.19D (DGND), P201.22A (DGND), P201.22C (DGND), P201.24B (DGND), P201.24D (DGND), P201.27A (DGND), P201.27C (DGND), P201.29B (DGND), P201.29D (DGND), P201.32A (DGND), P201.32C (DGND), P201.34B (DGND), P201.34D (DGND), P201.37A (DGND), P201.37C (DGND), P201.39B (DGND), P201.39D (DGND), P201.42A (DGND), P201.42C (DGND), P201.44B (DGND), P201.44D (DGND), P201.47A (DGND), P201.47C (DGND), P201.49B (DGND), P201.49D (DGND), P201.52A (DGND), P201.52C (DGND), P201.54B (DGND), P201.54D (DGND), P201.57A (DGND), P201.57C (DGND), P201.59B (DGND), P201.59D (DGND), P201.62A (DGND), P201.62C (DGND), P201.64B (DGND), P201.64D (DGND), P201.67A (DGND), P201.67C (DGND), P201.69B (DGND), P201.69D (DGND), P201.72A (DGND), P201.72C (DGND), P201.74B (DGND), P201.74D (AGND), P201.77A (DGND), P201.77C (AGND), P201.79B (DGND), P201.79D (AGND), P201.82A (DGND), P201.82C (AGND), P201.84B (DGND), P201.84D (AGND), P201.87A (DGND), P201.87C (AGND), P201.89B (DGND), P201.89D (AGND), P201.92A (DGND), P201.92C (AGND), P201.94B (DGND), P201.94D (AGND), P201.97A (DGND), P201.97C (AGND), P201.99B (DGND), P201.99D (AGND), P203.17, SW201.1, SW202.1, SW202.2
KNOCK_1+_AN: P201.100C (AN0), P202.36
KNOCK_1-_AN: P201.98D (AN1), P202.40
KNOCK_1_SPIA_CS: P201.51D (PCSB0), P202.4
KNOCK_2+_AN: P201.99C (AN2), P202.37
KNOCK_2-_AN: P201.97D (AN3), P202.38
KNOCK_2_SPIA_CS: P201.54C (PCSB1)
MAN_AIR_TEMP_AN: P201.86C (AN22), P202.10
MAP/MAF_1_AN: P201.89C (AN18), P202.6
MAP/MAF_2_AN: P201.87D (AN19), P202.29
MAP/MAF_3_AN: P201.88D (AN17), P202.33
MAX9924_CAM1_DIGI: P201.100B (ETPUA1), P203.34
MAX9924_CRANK1_DIGI: P201.77B (ETPUB3), P203.39
MAX9924_WHBL_DIGI: P201.64A (ETPUB26), P203.23
MAX9924_WHBR_DIGI: P201.62B (ETPUB27), P202.11
MAX9924_WHFL_DIGI: P201.65A (ETPUB24), P203.25
MAX9924_WHFR_DIGI: P201.63B (ETPUB25), P202.15
MC10XS3412_CSNS_AN: P201.90D (AN15)
MC10XS3412_IN0_DIGI: P201.99A (ETPUA2)
MC10XS3412_IN1_DIGI: P201.63A (ETPUB28), P203.21
MC10XS3412_IN2_DIGI: P201.76B (ETPUB5), P202.39
MC10XS3412_IN3_DIGI: P201.26C (EMIOS9)
MC10XS3412_SPIA-CS: P201.49C (PCSA3)
MC33800_EN: P201.43D (GPIO207)
MC33800_LRFDBK_AN: P201.93D (AN9)
MC33800_P1_DIGI: P201.41D (GPIO203), P202.5
MC33800_P3_DIGI: P201.43C (GPIO204)
MC33800_P5_DIGI: P201.89A (ETPUA18), P203.27
MC33800_P7_DIGI: P201.13C (EMIOS1), P202.32
MC33800_SPIA-CS: P201.48C (PCSA1)
MC33926_EN_DIGI: P201.96A (ETPUA6)
MC33926_FB_AN: P201.92D (AN11)
MC33926_IN1_DIGI: P201.75B (ETPUB7), P202.35
MC33926_IN2_DIGI: P201.25D (EMIOS8)
MC33926_SF_DIGI: P201.86B (ETPUA23), P203.37
MISC_SPIC-CS: P201.56C (PCSB5)
unnamed: D201.1 (A), R201.1
unnamed: P201.9C (/RSTCFG), SW201.2
unnamed: P201.10C (/RESET), SW202.3, SW202.4
unnamed: P201.98A (ETPUA4), R201.2
P01: P201.80A (ETPUB0), P201.82D (AN27), P203.1
P02: P201.83C (AN28), P201.87B (ETPUA21), P203.2
P03: P201.81D (AN29), P201.85A (ETPUA24), P203.3
P04: P201.81C (AN30), P201.88B (ETPUA19), P203.4
P05: P201.80D (AN31), P201.86A (ETPUA22), P203.5
P06: P201.80C (AN32), P201.90B (ETPUA17), P203.6
P07: P201.78D (AN33), P201.88A (ETPUA20), P203.7
P08: P201.79C (AN34), P201.91B (ETPUA15), P203.8
P09: P201.77D (AN35), P201.90A (ETPUA16), P203.9
P10: P201.96B (ETPUA7), P201.98C (AN4), P203.10
P11: P201.91A (ETPUA14), P201.96D (AN5), P203.11
P12: P201.96C (AN6), P201.97B (ETPUA5), P203.12
P13: P201.95D (AN7), P201.100A (ETPUA0), P203.13
P14: P201.78C (AN36), P201.98B (ETPUA3), P203.14
RS232_1_RX: P201.21C (RXDB_RS232), P202.28
RS232_1_TX: P201.23C (TXDB_RS232), P202.26
RS232_2_RX: P201.22D (RXDA_RS232), P202.1
RS232_2_TX: P201.23D (TXDA_RS232), P202.3
SPIA-CLK: P201.45D (SCKA), P202.9
SPIA-MISO: P201.46C (SOUTA), P202.20
SPIA-MOSI: P201.45C (SINA), P202.22
SPIB-CLK: P201.50D (SCKB), P202.13
SPIB-MISO: P201.53C (SOUTB), P202.16
SPIB-MOSI: P201.51C (SINB), P202.18
SPIC-CLK: P201.53D (PCSB4)
SPIC-MISO: P201.52D (PCSB2)
SPIC-MOSI: P201.55C (PCSB3)
TCPL1_SPIA_CS: P201.46D (PCSA0)
TCPL2_SPIA_CS: P201.47D (PCSA2)
TJA1054_1_CAN_RX: P201.24C (CNRXC)
TJA1054_1_CAN_TX: P201.25C (CNTXC)
TPS_AN: P201.88C (AN20), P202.8
