jharvey/Cinch_enclosure_template/KICAD_Project/sub_circuits/O2_input_CJ125.sch

## KiCad design KICAD_Project/sub_circuits/O2_input_CJ125.sch (2011-10-27)

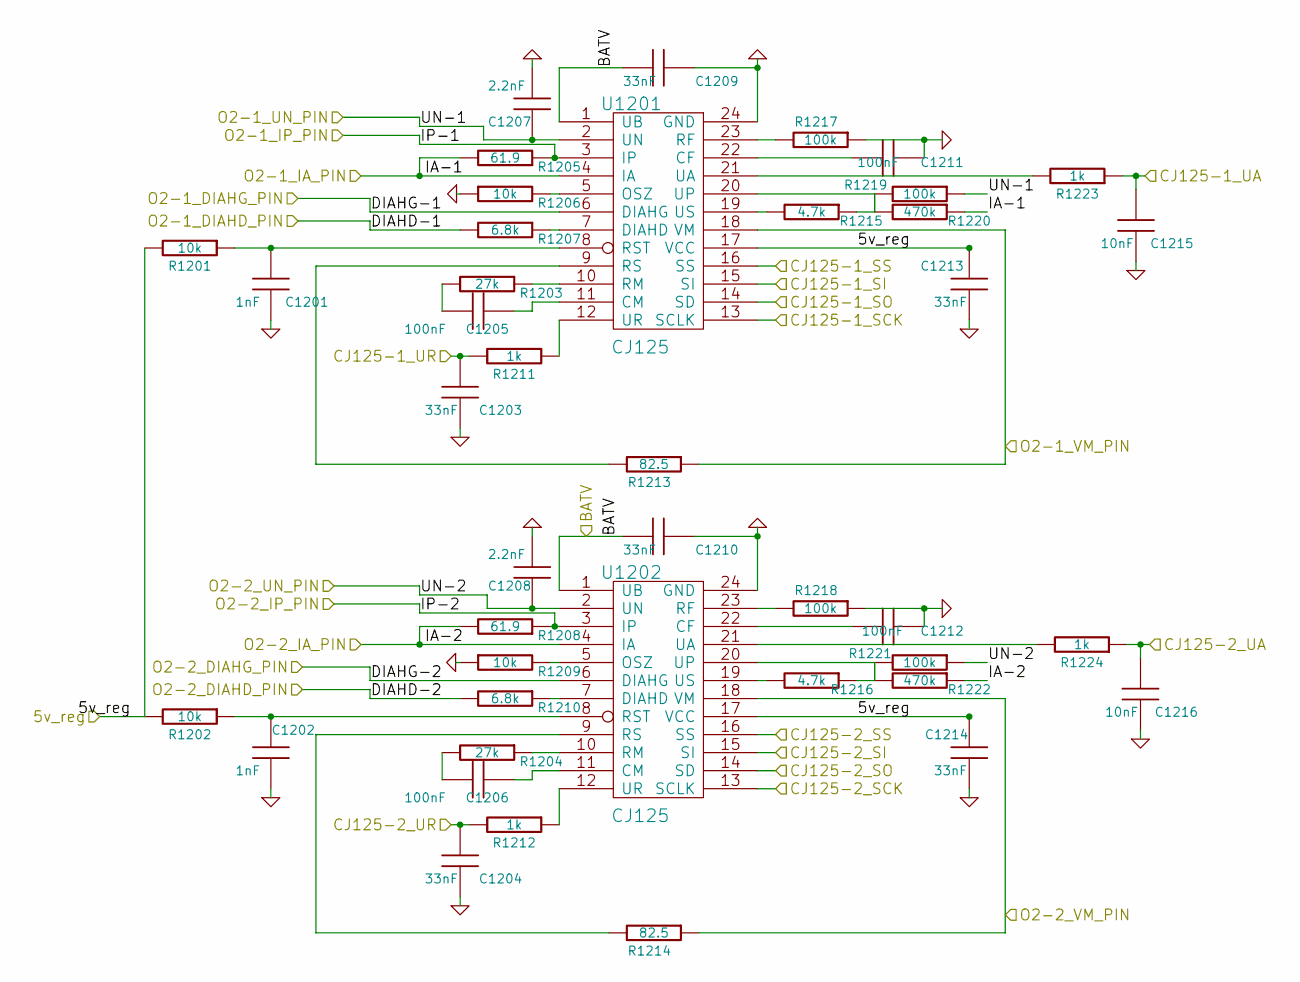
[picture p83: schematic O2_input_CJ125.sch]

Parts:
C1201, C1202: 1nF; SM0805
C1203, C1204, C1209, C1210, C1213, C1214: 33nF; SM0805; tolerance 10%
C1205, C1206, C1211, C1212: 100nF; SM0805
C1207, C1208: 2.2nF; SM0805
C1215, C1216: 10nF; SM0805
R1201, R1202, R1206, R1209: 10k; SM0805; tolerance 1%
R1203, R1204: 27k; SM0805
R1205, R1208: 61.9; SM0805
R1207, R1210: 6.8k; SM0805
R1211, R1212, R1223, R1224: 1k; SM0805
R1213, R1214: 82.5; SM0805
R1215, R1216: 4.7k; SM0805
R1217, R1218, R1219, R1221: 100k; SM0805; tolerance 1%
R1220, R1222: 470k; SM0805
U1201, U1202: CJ125; SOIC24

Connections:
5v_reg: C1213.2, C1214.2, R1201.2, R1202.2, U1201.17 (VCC), U1202.17 (VCC)
BATV: C1209.2, C1210.2, U1201.1 (UB), U1202.1 (UB)
CJ125-1_SCK: U1201.13 (SCLK)
CJ125-1_SI: U1201.15 (SI)
CJ125-1_SO: U1201.14 (SD)
CJ125-1_SS: U1201.16 (SS)
CJ125-1_UA: C1215.2, R1223.1
CJ125-1_UR: C1203.1, R1211.2
CJ125-2_SCK: U1202.13 (SCLK)
CJ125-2_SI: U1202.15 (SI)
CJ125-2_SO: U1202.14 (SD)
CJ125-2_SS: U1202.16 (SS)
CJ125-2_UA: C1216.2, R1224.1
CJ125-2_UR: C1204.1, R1212.2
DIAHD-1: R1207.2
DIAHD-2: R1210.2
DIAHG-1: U1201.6 (DIAHG)
DIAHG-2: U1202.6 (DIAHG)
GND: C1201.2, C1202.2, C1203.2, C1204.2, C1207.2, C1208.2, C1209.1, C1210.1, C1211.1, C1212.1, C1213.1, C1214.1, C1215.1, C1216.1, R1206.1, R1209.1, R1217.1, R1218.1, U1201.24 (GND), U1202.24 (GND)
IA-1: R1205.2, R1220.1, U1201.4 (IA)
IA-2: R1208.2, R1222.1, U1202.4 (IA)
IP-1: R1205.1, U1201.3 (IP)
IP-2: R1208.1, U1202.3 (IP)
unnamed: C1201.1, R1201.1, U1201.8 (RST)
unnamed: C1202.1, R1202.1, U1202.8 (RST)
unnamed: C1205.1, R1203.2
unnamed: C1205.2, U1201.11 (CM)
unnamed: C1206.1, R1204.2
unnamed: C1206.2, U1202.11 (CM)
unnamed: C1211.2, U1201.22 (CF)
unnamed: C1212.2, U1202.22 (CF)
unnamed: R1203.1, U1201.10 (RM)
unnamed: R1204.1, U1202.10 (RM)
unnamed: R1206.2, U1201.5 (OSZ)
unnamed: R1207.1, U1201.7 (DIAHD)
unnamed: R1209.2, U1202.5 (OSZ)
unnamed: R1210.1, U1202.7 (DIAHD)
unnamed: R1211.1, U1201.12 (UR)
unnamed: R1212.1, U1202.12 (UR)
unnamed: R1213.2, U1201.9 (RS)
unnamed: R1214.2, U1202.9 (RS)
unnamed: R1215.1, R1219.2, R1220.2, U1201.20 (UP)
unnamed: R1215.2, U1201.19 (US)
unnamed: R1216.1, R1221.2, R1222.2, U1202.20 (UP)
unnamed: R1216.2, U1202.19 (US)
unnamed: R1217.2, U1201.23 (RF)
unnamed: R1218.2, U1202.23 (RF)
unnamed: R1223.2, U1201.21 (UA)
unnamed: R1224.2, U1202.21 (UA)
O2-1_UN_PIN: C1207.1, R1219.1, U1201.2 (UN)
O2-1_VM_PIN: R1213.1, U1201.18 (VM)
O2-2_UN_PIN: C1208.1, R1221.1, U1202.2 (UN)
O2-2_VM_PIN: R1214.1, U1202.18 (VM)
