jharvey/Cinch_enclosure_template/KICAD_Project/sub_circuits/RPM_input_MAX9926.sch

## KiCad design KICAD_Project/sub_circuits/RPM_input_MAX9926.sch (2011-10-27)

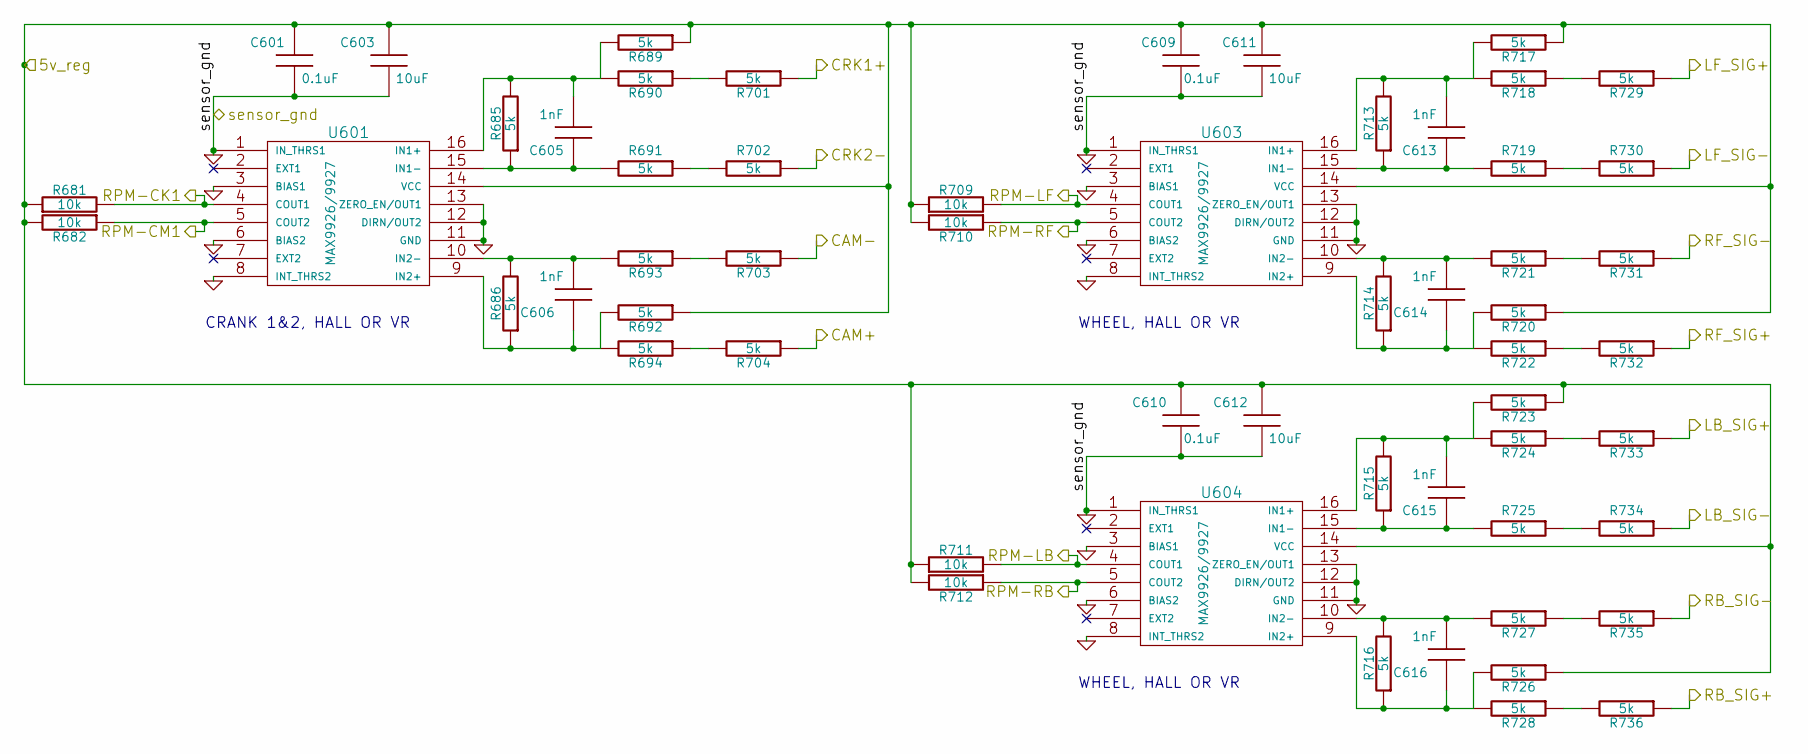
[picture p84: schematic RPM_input_MAX9926.sch]

Parts:
C601, C609, C610: 0.1uF; SM0805-C1; tolerance 10%
C603, C611, C612: 10uF; SM0805-C1; tolerance 10%
C605, C606, C613, C614, C615, C616: 1nF; SM0805
R681, R682, R709, R710, R711, R712: 10k; SM0805; tolerance 1%
R685, R686, R689, R690, R691, R692, R693, R694, R701, R702, R703, R704, R713, R714, R715, R716, R717, R718, R719, R720, R721, R722, R723, R724, R725, R726, R727, R728, R729, R730, R731, R732, R733, R734, R735, R736: 5k; SM0805
U601, U603, U604: MAX9926/9927; MAXIM-10-QSOP16

Connections:
5v_reg: C601.2, C603.2, C609.2, C610.2, C611.2, C612.2, R681.1, R682.2, R689.1, R692.1, R709.1, R710.2, R711.1, R712.2, R717.1, R720.1, R723.1, R726.1, U601.14 (VCC), U603.14 (VCC), U604.14 (VCC)
CAM+: R704.1
CAM-: R703.1
CRK1+: R701.1
CRK2-: R702.1
GND: C601.1, C603.1, C609.1, C610.1, C611.1, C612.1, U601.1 (IN_THRS1), U601.3 (BIAS1), U601.6 (BIAS2), U601.8 (INT_THRS2), U601.11 (GND), U601.12 (DIRN/OUT2), U601.13 (ZERO_EN/OUT1), U603.1 (IN_THRS1), U603.3 (BIAS1), U603.6 (BIAS2), U603.8 (INT_THRS2), U603.11 (GND), U603.12 (DIRN/OUT2), U603.13 (ZERO_EN/OUT1), U604.1 (IN_THRS1), U604.3 (BIAS1), U604.6 (BIAS2), U604.8 (INT_THRS2), U604.11 (GND), U604.12 (DIRN/OUT2), U604.13 (ZERO_EN/OUT1)
LB_SIG+: R733.1
LB_SIG-: R734.1
LF_SIG+: R729.1
LF_SIG-: R730.1
unnamed: C605.1, R685.1, R691.2, U601.15 (IN1-)
unnamed: C605.2, R685.2, R689.2, R690.2, U601.16 (IN1+)
unnamed: C606.1, R686.1, R692.2, R694.2, U601.9 (IN2+)
unnamed: C606.2, R686.2, R693.2, U601.10 (IN2-)
unnamed: C613.1, R713.1, R719.2, U603.15 (IN1-)
unnamed: C613.2, R713.2, R717.2, R718.2, U603.16 (IN1+)
unnamed: C614.1, R714.1, R720.2, R722.2, U603.9 (IN2+)
unnamed: C614.2, R714.2, R721.2, U603.10 (IN2-)
unnamed: C615.1, R715.1, R725.2, U604.15 (IN1-)
unnamed: C615.2, R715.2, R723.2, R724.2, U604.16 (IN1+)
unnamed: C616.1, R716.1, R726.2, R728.2, U604.9 (IN2+)
unnamed: C616.2, R716.2, R727.2, U604.10 (IN2-)
unnamed: R690.1, R701.2
unnamed: R691.1, R702.2
unnamed: R693.1, R703.2
unnamed: R694.1, R704.2
unnamed: R718.1, R729.2
unnamed: R719.1, R730.2
unnamed: R721.1, R731.2
unnamed: R722.1, R732.2
unnamed: R724.1, R733.2
unnamed: R725.1, R734.2
unnamed: R727.1, R735.2
unnamed: R728.1, R736.2
RB_SIG+: R736.1
RB_SIG-: R735.1
RF_SIG+: R732.1
RF_SIG-: R731.1
RPM-CK1: R681.2, U601.4 (COUT1)
RPM-CM1: R682.1, U601.5 (COUT2)
RPM-LB: R711.2, U604.4 (COUT1)
RPM-LF: R709.2, U603.4 (COUT1)
RPM-RB: R712.1, U604.5 (COUT2)
RPM-RF: R710.1, U603.5 (COUT2)

Notes on the sheet:
WHEEL, HALL OR VR
CRANK 1&2, HALL OR VR
