jharvey/Cinch_enclosure_template/KICAD_Project/sub_circuits/SENSOR_INPUTS.sch

## KiCad design KICAD_Project/sub_circuits/SENSOR_INPUTS.sch (2011-10-27)

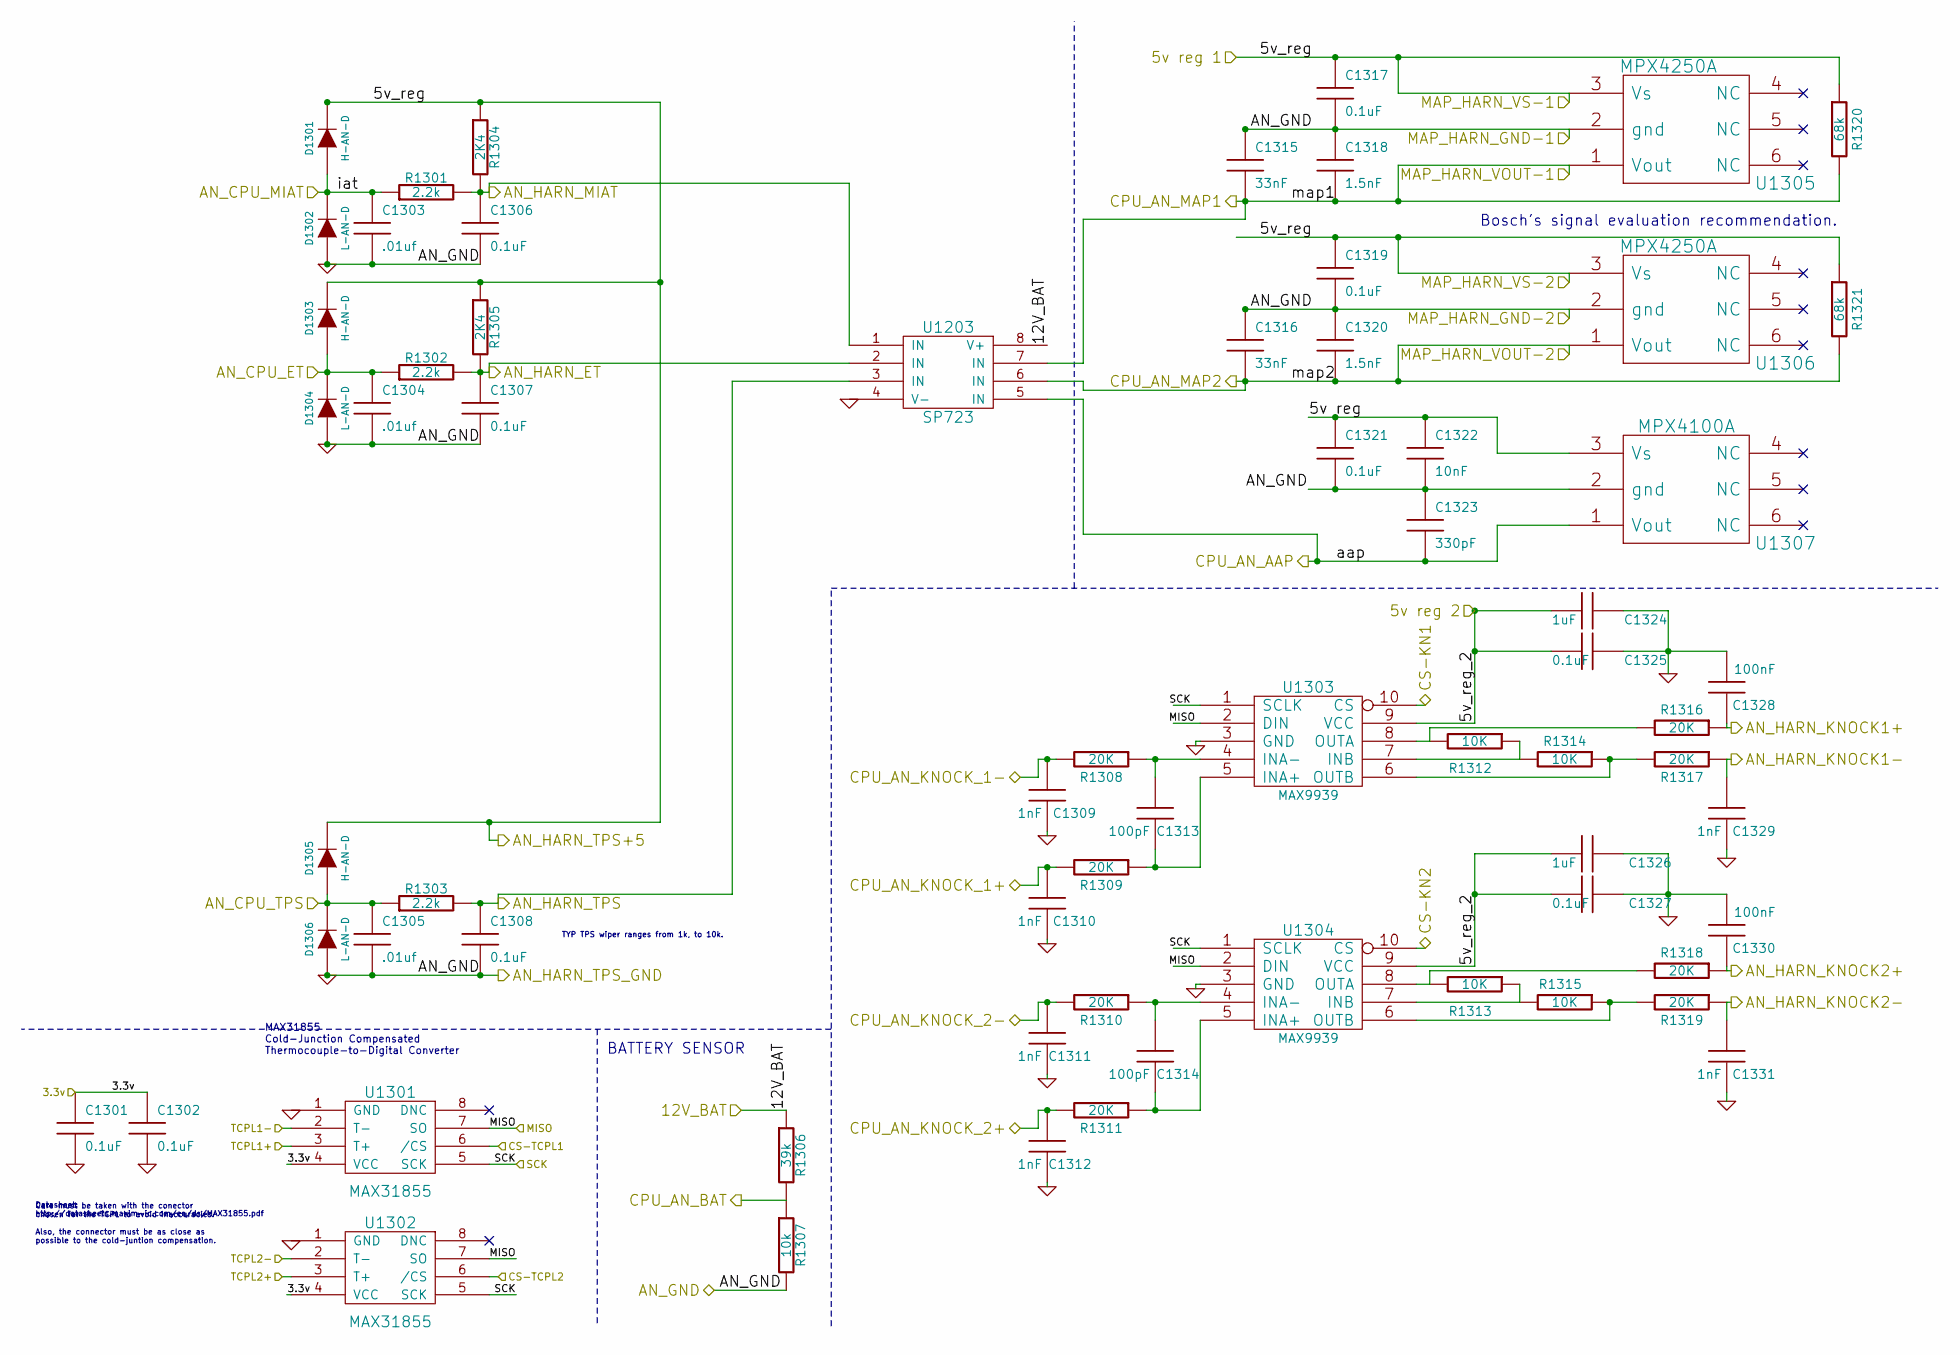
[picture p85: schematic SENSOR_INPUTS.sch]

Parts:
C1301, C1302, C1306, C1307, C1308, C1317, C1319, C1321, C1325, C1327: 0.1uF; SM0805; tolerance 10%
C1303, C1304, C1305: .01uf; SM0805
C1309, C1310, C1311, C1312, C1329, C1331: 1nF; SM0805
C1313, C1314: 100pF; SM0805
C1315, C1316: 33nF; SM0805; tolerance 10%
C1318, C1320: 1.5nF; SM0805; Voltage 50v; tolerance 10%; mfg# CC0805KRX7R9BB152
C1322: 10nF; SM0805
C1323: 330pF; SM0805; voltage 50; mfg# 08055C333KAZ2A
C1324, C1326: 1uF; SM0805
C1328, C1330: 100nF; SM0805
D1301, D1303, D1305: H-AN-D; SOD-123
D1302, D1304, D1306: L-AN-D; SOD-123
R1301, R1302, R1303: 2.2k; SM0805
R1304, R1305: 2K4; SM0805; tolerance .1%
R1306: 39k; SM0805; mfg# RMCF0805JT39K0CT
R1307: 10k; SM0805; tolerance 1%
R1308, R1309, R1310, R1311, R1316, R1317, R1318, R1319: 20K; SM0805
R1312, R1313, R1314, R1315: 10K; SM0805; tolerance 1%
R1320, R1321: 68k; SM0805; tolerance 5%; mfg# ERJ-6GEYJ684V
U1203: SP723; SO8E
U1301, U1302: MAX31855; -SOIC8; MFG# MAX31855NASA+
U1303, U1304: MAX9939; uMAX-uSOP_10
U1305, U1306: MPX4250A; MPX-4_MAP; mfg# MPX4250AP
U1307: MPX4100A; MPX4---A; mfg# MPX4100A

Connections:
3.3v: C1301.1, C1302.1, U1301.4 (VCC), U1302.4 (VCC)
5v reg: C1321.1, C1322.1, U1307.3 (Vs)
5v reg 1: C1317.1, C1319.1, D1301.2 (K), D1303.2 (K), D1305.2 (K), R1304.1, R1305.1, R1320.1, R1321.1, U1305.3 (Vs), U1306.3 (Vs)
5v reg 2: C1324.2, C1325.2, C1326.2, C1327.2, U1303.9 (VCC), U1304.9 (VCC)
12V_BAT: R1306.1, U1203.8 (V+)
AN_CPU_ET: C1304.1, D1303.1 (A), D1304.2 (K), R1302.1
AN_CPU_MIAT: C1303.1, D1301.1 (A), D1302.2 (K), R1301.1
AN_CPU_TPS: C1305.1, D1305.1 (A), D1306.2 (K), R1303.1
AN_HARN_ET: C1307.1, R1302.2, R1305.2, U1203.2 (IN)
AN_HARN_KNOCK1+: C1328.1, R1316.1
AN_HARN_KNOCK1-: C1329.2, R1317.1
AN_HARN_KNOCK2+: C1330.1, R1318.1
AN_HARN_KNOCK2-: C1331.2, R1319.1
AN_HARN_MIAT: C1306.1, R1301.2, R1304.2, U1203.1 (IN)
AN_HARN_TPS: C1308.1, R1303.2, U1203.3 (IN)
CPU_AN_BAT: R1306.2, R1307.1
CPU_AN_KNOCK_1+: C1310.2, R1309.2
CPU_AN_KNOCK_1-: C1309.2, R1308.2
CPU_AN_KNOCK_2+: C1312.2, R1311.2
CPU_AN_KNOCK_2-: C1311.2, R1310.2
CPU_AN_MAP1: C1315.2, C1318.2, R1320.2, U1203.7 (IN), U1305.1 (Vout)
CPU_AN_MAP2: C1316.2, C1320.2, R1321.2, U1203.6 (IN), U1306.1 (Vout)
CS-KN1: U1303.10 (CS)
CS-KN2: U1304.10 (CS)
CS-TCPL1: U1301.6 (/CS)
CS-TCPL2: U1302.6 (/CS)
GND: C1301.2, C1302.2, C1303.2, C1304.2, C1305.2, C1306.2, C1307.2, C1308.2, C1309.1, C1310.1, C1311.1, C1312.1, C1315.1, C1316.1, C1317.2, C1318.1, C1319.2, C1320.1, C1321.2, C1322.2, C1323.1, C1324.1, C1325.1, C1326.1, C1327.1, C1328.2, C1329.1, C1330.2, C1331.1, D1302.1 (A), D1304.1 (A), D1306.1 (A), R1307.2, U1203.4 (V-), U1301.1 (GND), U1302.1 (GND), U1303.3 (GND), U1304.3 (GND), U1305.2 (gnd), U1306.2 (gnd), U1307.2 (gnd)
MISO: U1301.7 (SO), U1302.7 (SO), U1303.2 (DIN), U1304.2 (DIN)
unnamed: C1313.1, R1309.1, U1303.5 (INA+)
unnamed: C1313.2, R1308.1, U1303.4 (INA-)
unnamed: C1314.1, R1311.1, U1304.5 (INA+)
unnamed: C1314.2, R1310.1, U1304.4 (INA-)
unnamed: R1312.1, R1314.2, U1303.7 (INB)
unnamed: R1312.2, R1316.2, U1303.8 (OUTA)
unnamed: R1313.1, R1315.2, U1304.7 (INB)
unnamed: R1313.2, R1318.2, U1304.8 (OUTA)
unnamed: R1314.1, R1317.2, U1303.6 (OUTB)
unnamed: R1315.1, R1319.2, U1304.6 (OUTB)
SCK: U1301.5 (SCK), U1302.5 (SCK), U1303.1 (SCLK), U1304.1 (SCLK)
TCPL1+: U1301.3 (T+)
TCPL1-: U1301.2 (T-)
TCPL2+: U1302.3 (T+)
TCPL2-: U1302.2 (T-)
aap: C1323.2, U1203.5 (IN), U1307.1 (Vout)

Notes on the sheet:
TYP TPS wiper ranges from 1k, to 10k.
BATTERY SENSOR
Care must be taken with the conector chosen for the TCPL to avoid inaccuracies. Also, the connector must be as close as possible to the cold-juntion compensation.
MAX31855 Cold-Junction Compensated Thermocouple-to-Digital Converter
Datasheet: http://datasheets.maxim-ic.com/en/ds/MAX31855.pdf
Bosch's signal evaluation recommendation.
