jharvey/Cinch_enclosure_template/KICAD_Project/sub_circuits/an_protect2.sch

## KiCad design KICAD_Project/sub_circuits/an_protect2.sch (2011-09-27)

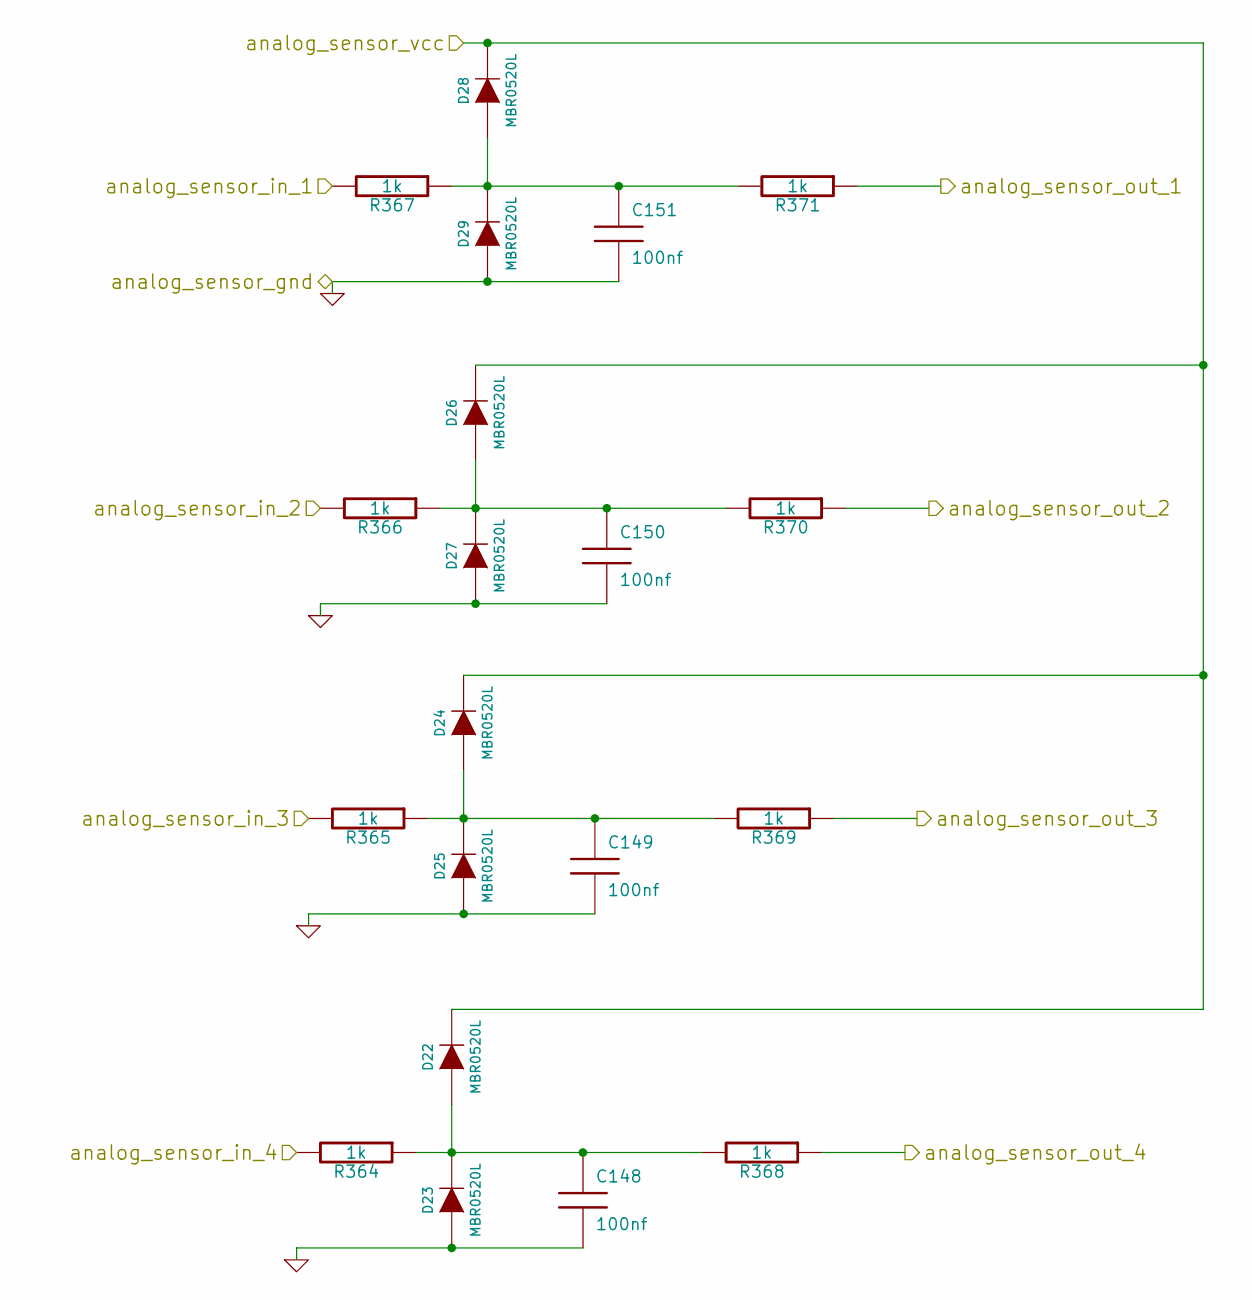
[picture p86: schematic an_protect2.sch]

Parts:
C148, C149, C150, C151: 100nf; SM0805-C1; tolerance 10%
D22, D23, D24, D25, D26, D27, D28, D29: MBR0520L; SOD123
R364, R365, R366, R367, R368, R369, R370, R371: 1k; SM0805

Connections:
GND: C148.2, C149.2, C150.2, C151.2, D23.1 (A), D25.1 (A), D27.1 (A), D29.1 (A)
unnamed: C148.1, D22.1 (A), D23.2 (K), R364.1, R368.2
unnamed: C149.1, D24.1 (A), D25.2 (K), R365.1, R369.2
unnamed: C150.1, D26.1 (A), D27.2 (K), R366.1, R370.2
unnamed: C151.1, D28.1 (A), D29.2 (K), R367.1, R371.2
analog_sensor_in_1: R367.2
analog_sensor_in_2: R366.2
analog_sensor_in_3: R365.2
analog_sensor_in_4: R364.2
analog_sensor_out_1: R371.1
analog_sensor_out_2: R370.1
analog_sensor_out_3: R369.1
analog_sensor_out_4: R368.1
analog_sensor_vcc: D22.2 (K), D24.2 (K), D26.2 (K), D28.2 (K)
