jharvey/Cinch_enclosure_template/KICAD_Project/sub_circuits/efi-drivers.sch

## KiCad design KICAD_Project/sub_circuits/efi-drivers.sch (2011-08-15)

Schematic: efi-drivers.sch

Parts:
Q501, Q502, Q503, Q504, Q505, Q506, Q507, Q508: IRGB14C40LPBF
R511, R512, R513, R514, R515, R516, R517, R518: 1K; SM0805; tolerance 1%
R1440, R1441, R1442, R1443, R1444, R1445, R1446, R1447: 4K7; R3_SM0805; tolerance 5%
R1448: 10K; SM0805; tolerance 1%
U723: 74HCT244_THRU

Notes on the sheet:
10-20 KHz
