jharvey/Cinch_enclosure_template/KICAD_Project/sub_circuits/efi-drivers_sub_circuits.sch

## KiCad design KICAD_Project/sub_circuits/efi-drivers_sub_circuits.sch (2011-10-27)

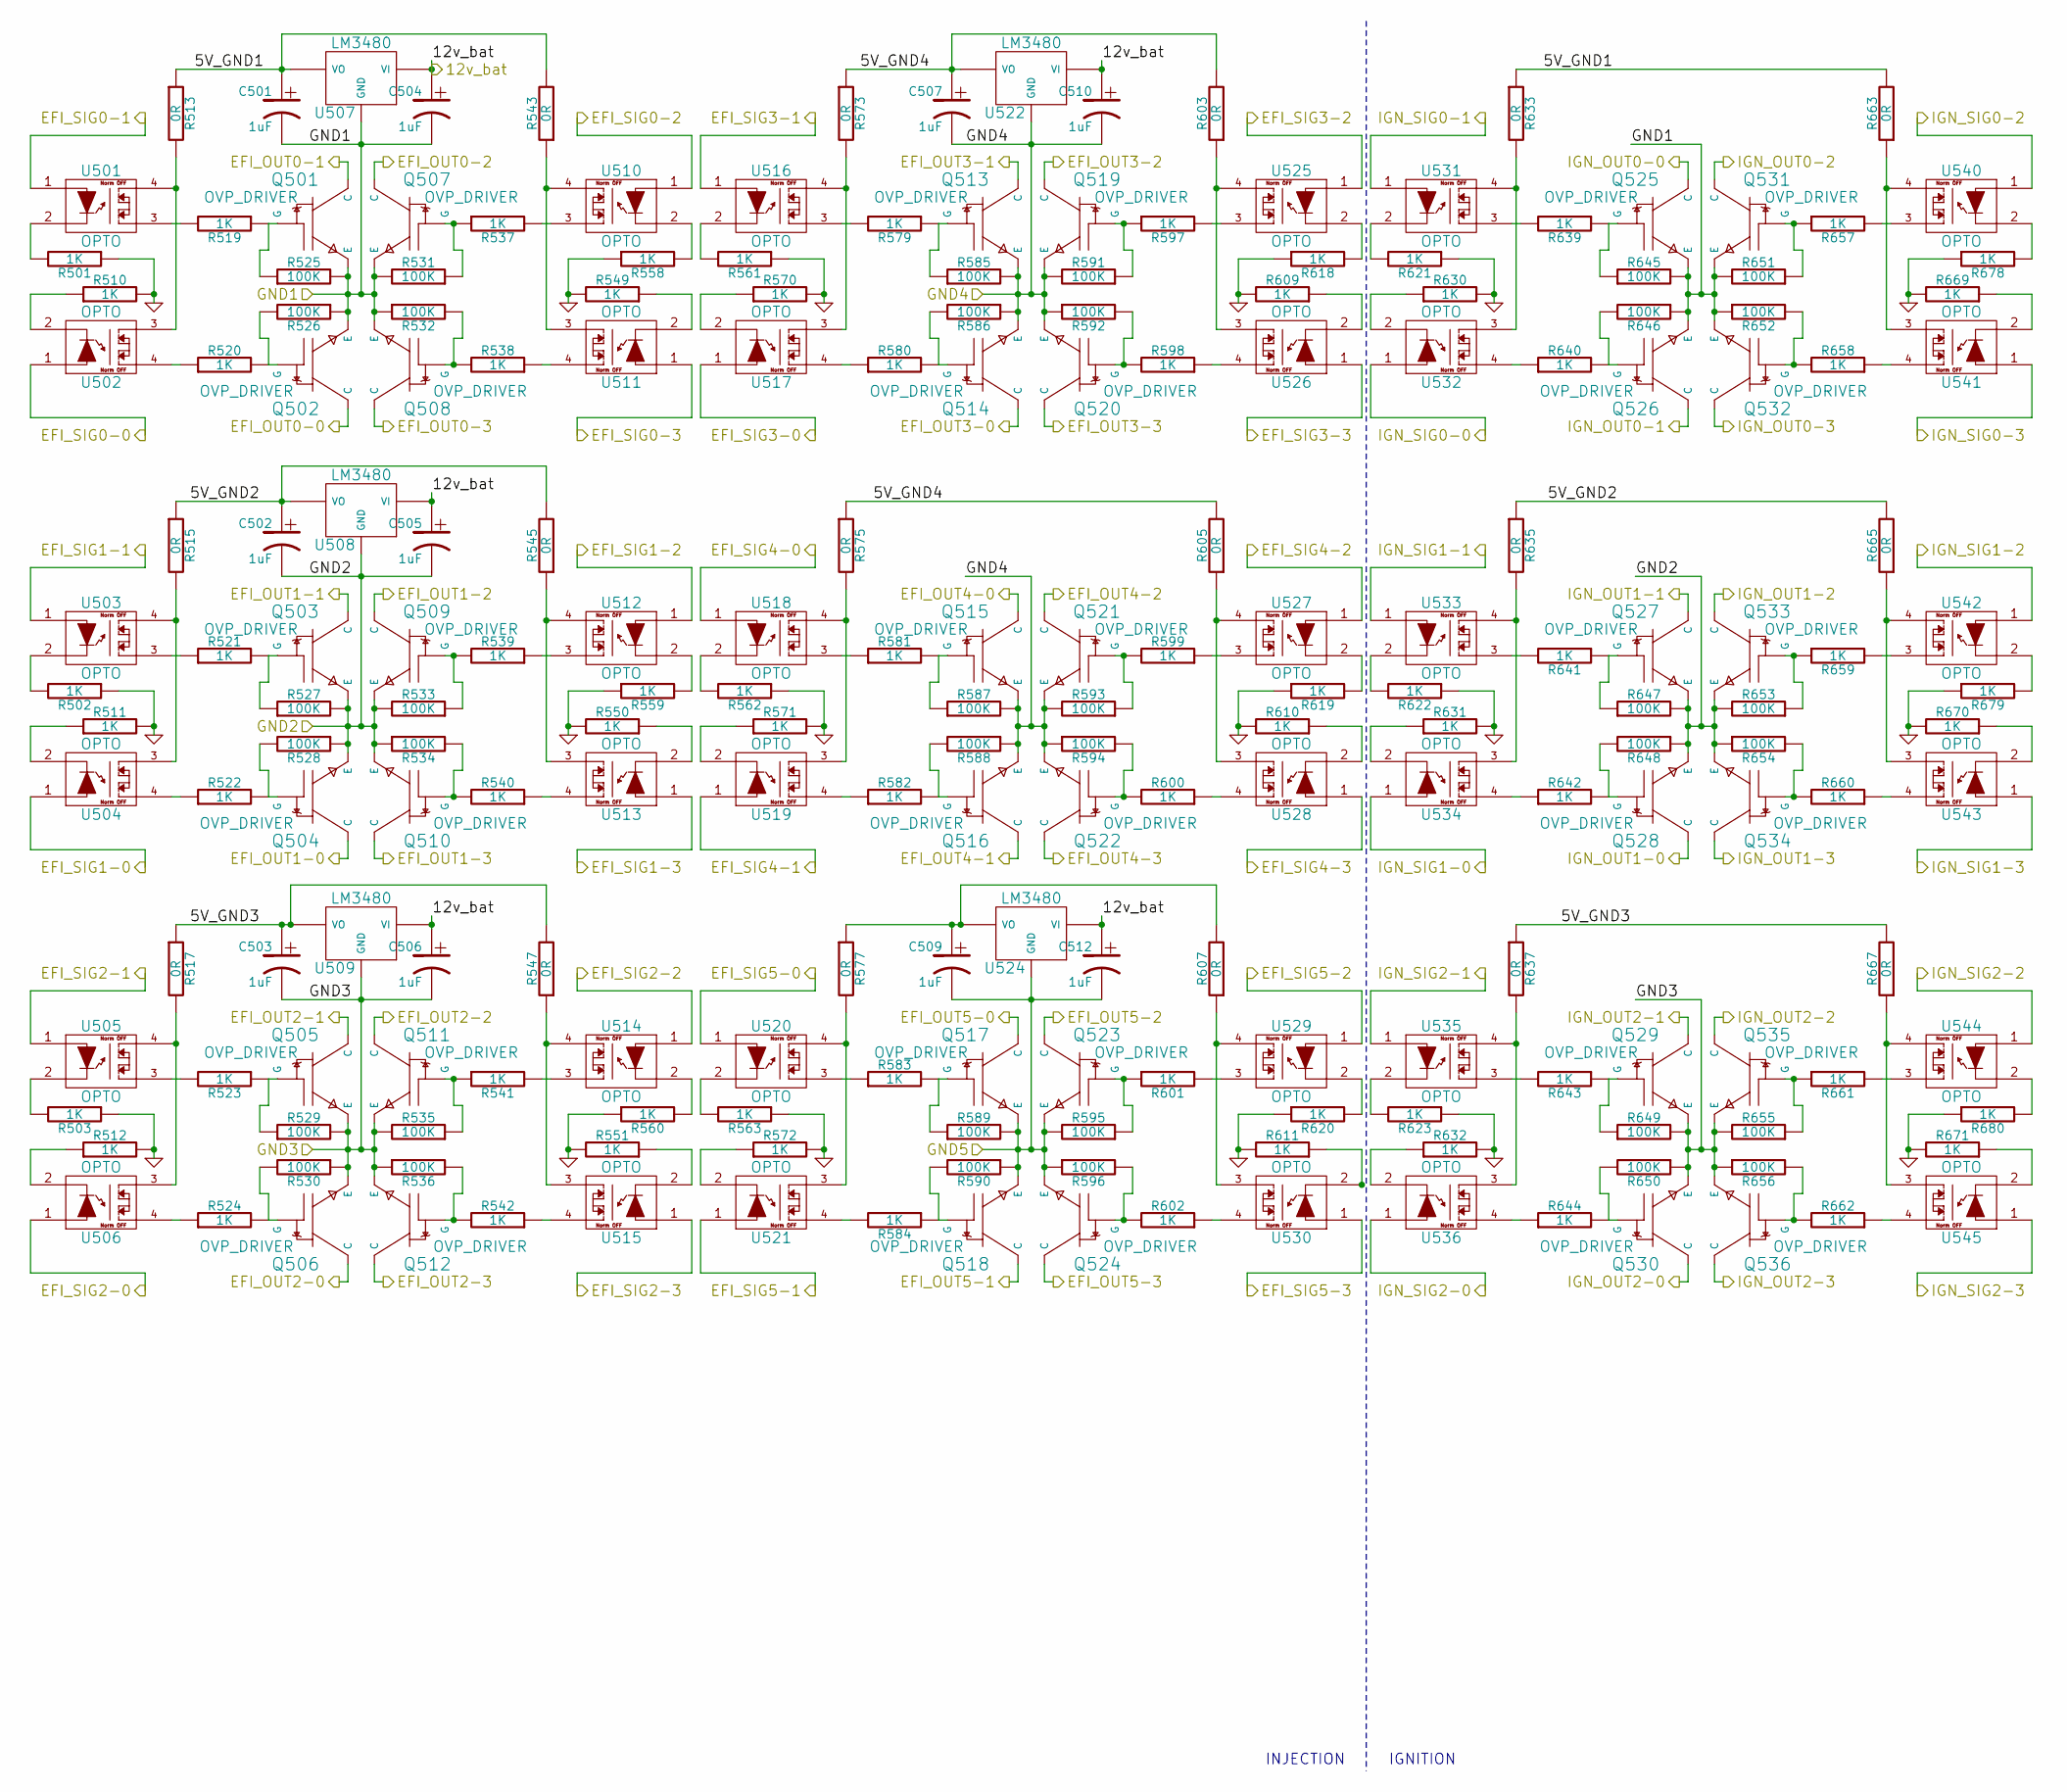
[picture p87: schematic efi-drivers_sub_circuits.sch]

Parts:
C501, C502, C503, C504, C505, C506, C507, C509, C510, C512: 1uF; SM0805; mfg# 08051C103JAT2A
Q501, Q502, Q503, Q504, Q505, Q506, Q507, Q508, Q509, Q510, Q511, Q512, Q513, Q514, Q515, Q516, Q517, Q518, Q519, Q520, Q521, Q522, Q523, Q524, Q525, Q526, Q527, Q528, Q529, Q530, Q531, Q532, Q533, Q534, Q535, Q536: OVP_DRIVER; SO8E_ST
R501, R502, R503, R510, R511, R512, R519, R520, R521, R522, R523, R524, R537, R538, R539, R540, R541, R542, R549, R550, R551, R558, R559, R560, R561, R562, R563, R570, R571, R572, R579, R580, R581, R582, R583, R584, R597, R598, R599, R600, R601, R602, R609, R610, R611, R618, R619, R620, R621, R622, R623, R630, R631, R632, R639, R640, R641, R642, R643, R644, R657, R658, R659, R660, R661, R662, R669, R670, R671, R678, R679, R680: 1K; SM0805; tolerance 1%
R513, R515, R517, R543, R545, R547, R573, R575, R577, R603, R605, R607, R633, R635, R637, R663, R665, R667: 0R; SM0805; tolerance %
R525, R526, R527, R528, R529, R530, R531, R532, R533, R534, R535, R536, R585, R586, R587, R588, R589, R590, R591, R592, R593, R594, R595, R596, R645, R646, R647, R648, R649, R650, R651, R652, R653, R654, R655, R656: 100K; SM0805; tolerance 1%
U501, U502, U503, U504, U505, U506, U510, U511, U512, U513, U514, U515, U516, U517, U518, U519, U520, U521, U525, U526, U527, U528, U529, U530, U531, U532, U533, U534, U535, U536, U540, U541, U542, U543, U544, U545: OPTO; relay-SOP04; mfg # SFH690ABT
U507, U508, U509, U522, U524: LM3480; SOT23-3; tolerance .05%

Connections:
5V_GND1: C501.1, R513.1, R543.2, R633.1, R663.2, U507.2 (VO)
5V_GND2: C502.1, R515.1, R545.2, R635.1, R665.2, U508.2 (VO)
5V_GND3: C503.1, R517.1, R547.2, R637.1, R667.2, U509.2 (VO)
5V_GND4: C507.1, R573.1, R575.1, R603.2, R605.2, U522.2 (VO)
12v_bat: C504.1, C505.1, C506.1, C510.1, C512.1, U507.1 (VI), U508.1 (VI), U509.1 (VI), U522.1 (VI), U524.1 (VI)
EFI_OUT0-0: Q502.2 (C)
EFI_OUT0-1: Q501.2 (C)
EFI_OUT0-2: Q507.2 (C)
EFI_OUT0-3: Q508.2 (C)
EFI_OUT1-0: Q504.2 (C)
EFI_OUT1-1: Q503.2 (C)
EFI_OUT1-2: Q509.2 (C)
EFI_OUT1-3: Q510.2 (C)
EFI_OUT2-0: Q506.2 (C)
EFI_OUT2-1: Q505.2 (C)
EFI_OUT2-2: Q511.2 (C)
EFI_OUT2-3: Q512.2 (C)
EFI_OUT3-0: Q514.2 (C)
EFI_OUT3-1: Q513.2 (C)
EFI_OUT3-2: Q519.2 (C)
EFI_OUT3-3: Q520.2 (C)
EFI_OUT4-0: Q515.2 (C)
EFI_OUT4-1: Q516.2 (C)
EFI_OUT4-2: Q521.2 (C)
EFI_OUT4-3: Q522.2 (C)
EFI_OUT5-0: Q517.2 (C)
EFI_OUT5-1: Q518.2 (C)
EFI_OUT5-2: Q523.2 (C)
EFI_OUT5-3: Q524.2 (C)
EFI_SIG0-0: U502.1 (ANOD)
EFI_SIG0-1: U501.1 (ANOD)
EFI_SIG0-2: U510.1 (ANOD)
EFI_SIG0-3: U511.1 (ANOD)
EFI_SIG1-0: U504.1 (ANOD)
EFI_SIG1-1: U503.1 (ANOD)
EFI_SIG1-2: U512.1 (ANOD)
EFI_SIG1-3: U513.1 (ANOD)
EFI_SIG2-0: U506.1 (ANOD)
EFI_SIG2-1: U505.1 (ANOD)
EFI_SIG2-2: U514.1 (ANOD)
EFI_SIG2-3: U515.1 (ANOD)
EFI_SIG3-0: U517.1 (ANOD)
EFI_SIG3-1: U516.1 (ANOD)
EFI_SIG3-2: U525.1 (ANOD)
EFI_SIG3-3: U526.1 (ANOD)
EFI_SIG4-0: U518.1 (ANOD)
EFI_SIG4-1: U519.1 (ANOD)
EFI_SIG4-2: U527.1 (ANOD)
EFI_SIG4-3: U528.1 (ANOD)
EFI_SIG5-0: U520.1 (ANOD)
EFI_SIG5-1: U521.1 (ANOD)
EFI_SIG5-2: U529.1 (ANOD)
EFI_SIG5-3: U530.1 (ANOD)
GND: R501.1, R502.1, R503.1, R510.2, R511.2, R512.2, R549.2, R550.2, R551.2, R558.1, R559.1, R560.1, R561.1, R562.1, R563.1, R570.2, R571.2, R572.2, R609.2, R610.2, R611.2, R618.1, R619.1, R620.1, R621.1, R622.1, R623.1, R630.2, R631.2, R632.2, R669.2, R670.2, R671.2, R678.1, R679.1, R680.1
GND1: C501.2, C504.2, Q501.3 (E), Q502.3 (E), Q507.3 (E), Q508.3 (E), Q525.3 (E), Q526.3 (E), Q531.3 (E), Q532.3 (E), R525.2, R526.1, R531.2, R532.1, R645.2, R646.1, R651.2, R652.1, U507.3 (GND)
GND2: C502.2, C505.2, Q503.3 (E), Q504.3 (E), Q509.3 (E), Q510.3 (E), Q527.3 (E), Q528.3 (E), Q533.3 (E), Q534.3 (E), R527.2, R528.1, R533.2, R534.1, R647.2, R648.1, R653.2, R654.1, U508.3 (GND)
GND3: C503.2, C506.2, Q505.3 (E), Q506.3 (E), Q511.3 (E), Q512.3 (E), Q529.3 (E), Q530.3 (E), Q535.3 (E), Q536.3 (E), R529.2, R530.1, R535.2, R536.1, R649.2, R650.1, R655.2, R656.1, U509.3 (GND)
GND4: C507.2, C510.2, Q513.3 (E), Q514.3 (E), Q515.3 (E), Q516.3 (E), Q519.3 (E), Q520.3 (E), Q521.3 (E), Q522.3 (E), R585.2, R586.1, R587.2, R588.1, R591.2, R592.1, R593.2, R594.1, U522.3 (GND)
GND5: C509.2, C512.2, Q517.3 (E), Q518.3 (E), Q523.3 (E), Q524.3 (E), R589.2, R590.1, R595.2, R596.1, U524.3 (GND)
IGN_OUT0-0: Q525.2 (C)
IGN_OUT0-1: Q526.2 (C)
IGN_OUT0-2: Q531.2 (C)
IGN_OUT0-3: Q532.2 (C)
IGN_OUT1-0: Q528.2 (C)
IGN_OUT1-1: Q527.2 (C)
IGN_OUT1-2: Q533.2 (C)
IGN_OUT1-3: Q534.2 (C)
IGN_OUT2-0: Q530.2 (C)
IGN_OUT2-1: Q529.2 (C)
IGN_OUT2-2: Q535.2 (C)
IGN_OUT2-3: Q536.2 (C)
IGN_SIG0-0: U532.1 (ANOD)
IGN_SIG0-1: U531.1 (ANOD)
IGN_SIG0-2: U540.1 (ANOD)
IGN_SIG0-3: U541.1 (ANOD)
IGN_SIG1-0: U534.1 (ANOD)
IGN_SIG1-1: U533.1 (ANOD)
IGN_SIG1-2: U542.1 (ANOD)
IGN_SIG1-3: U543.1 (ANOD)
IGN_SIG2-0: U536.1 (ANOD)
IGN_SIG2-1: U535.1 (ANOD)
IGN_SIG2-2: U544.1 (ANOD)
IGN_SIG2-3: U545.1 (ANOD)
unnamed: C509.1, R577.1, R607.2, U524.2 (VO)
unnamed: Q501.1 (G), R519.1, R525.1
unnamed: Q502.1 (G), R520.2, R526.2
unnamed: Q503.1 (G), R521.2, R527.1
unnamed: Q504.1 (G), R522.2, R528.2
unnamed: Q505.1 (G), R523.1, R529.1
unnamed: Q506.1 (G), R524.2, R530.2
unnamed: Q507.1 (G), R531.1, R537.1
unnamed: Q508.1 (G), R532.2, R538.2
unnamed: Q509.1 (G), R533.1, R539.2
unnamed: Q510.1 (G), R534.2, R540.2
unnamed: Q511.1 (G), R535.1, R541.1
unnamed: Q512.1 (G), R536.2, R542.2
unnamed: Q513.1 (G), R579.1, R585.1
unnamed: Q514.1 (G), R580.2, R586.2
unnamed: Q515.1 (G), R581.2, R587.1
unnamed: Q516.1 (G), R582.2, R588.2
unnamed: Q517.1 (G), R583.2, R589.1
unnamed: Q518.1 (G), R584.1, R590.2
unnamed: Q519.1 (G), R591.1, R597.1
unnamed: Q520.1 (G), R592.2, R598.2
unnamed: Q521.1 (G), R593.1, R599.2
unnamed: Q522.1 (G), R594.2, R600.2
unnamed: Q523.1 (G), R595.1, R601.1
unnamed: Q524.1 (G), R596.2, R602.2
unnamed: Q525.1 (G), R639.1, R645.1
unnamed: Q526.1 (G), R640.2, R646.2
unnamed: Q527.1 (G), R641.1, R647.1
unnamed: Q528.1 (G), R642.2, R648.2
unnamed: Q529.1 (G), R643.1, R649.1
unnamed: Q530.1 (G), R644.2, R650.2
unnamed: Q531.1 (G), R651.1, R657.1
unnamed: Q532.1 (G), R652.2, R658.2
unnamed: Q533.1 (G), R653.1, R659.1
unnamed: Q534.1 (G), R654.2, R660.2
unnamed: Q535.1 (G), R655.1, R661.1
unnamed: Q536.1 (G), R656.2, R662.2
unnamed: R501.2, U501.2 (CATH)
unnamed: R502.2, U503.2 (CATH)
unnamed: R503.2, U505.2 (CATH)
unnamed: R510.1, U502.2 (CATH)
unnamed: R511.1, U504.2 (CATH)
unnamed: R512.1, U506.2 (CATH)
unnamed: R513.2, U501.4 (INOUTA1), U502.3 (INOUTB1)
unnamed: R515.2, U503.4 (INOUTA1), U504.3 (INOUTB1)
unnamed: R517.2, U505.4 (INOUTA1), U506.3 (INOUTB1)
unnamed: R519.2, U501.3 (INOUTB1)
unnamed: R520.1, U502.4 (INOUTA1)
unnamed: R521.1, U503.3 (INOUTB1)
unnamed: R522.1, U504.4 (INOUTA1)
unnamed: R523.2, U505.3 (INOUTB1)
unnamed: R524.1, U506.4 (INOUTA1)
unnamed: R537.2, U510.3 (INOUTB1)
unnamed: R538.1, U511.4 (INOUTA1)
unnamed: R539.1, U512.3 (INOUTB1)
unnamed: R540.1, U513.4 (INOUTA1)
unnamed: R541.2, U514.3 (INOUTB1)
unnamed: R542.1, U515.4 (INOUTA1)
unnamed: R543.1, U510.4 (INOUTA1), U511.3 (INOUTB1)
unnamed: R545.1, U512.4 (INOUTA1), U513.3 (INOUTB1)
unnamed: R547.1, U514.4 (INOUTA1), U515.3 (INOUTB1)
unnamed: R549.1, U511.2 (CATH)
unnamed: R550.1, U513.2 (CATH)
unnamed: R551.1, U515.2 (CATH)
unnamed: R558.2, U510.2 (CATH)
unnamed: R559.2, U512.2 (CATH)
unnamed: R560.2, U514.2 (CATH)
unnamed: R561.2, U516.2 (CATH)
unnamed: R562.2, U518.2 (CATH)
unnamed: R563.2, U520.2 (CATH)
unnamed: R570.1, U517.2 (CATH)
unnamed: R571.1, U519.2 (CATH)
unnamed: R572.1, U521.2 (CATH)
unnamed: R573.2, U516.4 (INOUTA1), U517.3 (INOUTB1)
unnamed: R575.2, U518.4 (INOUTA1), U519.3 (INOUTB1)
unnamed: R577.2, U520.4 (INOUTA1), U521.3 (INOUTB1)
unnamed: R579.2, U516.3 (INOUTB1)
unnamed: R580.1, U517.4 (INOUTA1)
unnamed: R581.1, U518.3 (INOUTB1)
unnamed: R582.1, U519.4 (INOUTA1)
unnamed: R583.1, U520.3 (INOUTB1)
unnamed: R584.2, U521.4 (INOUTA1)
unnamed: R597.2, U525.3 (INOUTB1)
unnamed: R598.1, U526.4 (INOUTA1)
unnamed: R599.1, U527.3 (INOUTB1)
unnamed: R600.1, U528.4 (INOUTA1)
unnamed: R601.2, U529.3 (INOUTB1)
unnamed: R602.1, U530.4 (INOUTA1)
unnamed: R603.1, U525.4 (INOUTA1), U526.3 (INOUTB1)
unnamed: R605.1, U527.4 (INOUTA1), U528.3 (INOUTB1)
unnamed: R607.1, U529.4 (INOUTA1), U530.3 (INOUTB1)
unnamed: R609.1, U526.2 (CATH)
unnamed: R610.1, U528.2 (CATH)
unnamed: R611.1, U530.2 (CATH)
unnamed: R618.2, U525.2 (CATH)
unnamed: R619.2, U527.2 (CATH)
unnamed: R620.2, U529.2 (CATH)
unnamed: R621.2, U531.2 (CATH)
unnamed: R622.2, U533.2 (CATH)
unnamed: R623.2, U535.2 (CATH)
unnamed: R630.1, U532.2 (CATH)
unnamed: R631.1, U534.2 (CATH)
unnamed: R632.1, U536.2 (CATH)
unnamed: R633.2, U531.4 (INOUTA1), U532.3 (INOUTB1)
unnamed: R635.2, U533.4 (INOUTA1), U534.3 (INOUTB1)
unnamed: R637.2, U535.4 (INOUTA1), U536.3 (INOUTB1)
unnamed: R639.2, U531.3 (INOUTB1)
unnamed: R640.1, U532.4 (INOUTA1)
unnamed: R641.2, U533.3 (INOUTB1)
unnamed: R642.1, U534.4 (INOUTA1)
unnamed: R643.2, U535.3 (INOUTB1)
unnamed: R644.1, U536.4 (INOUTA1)
unnamed: R657.2, U540.3 (INOUTB1)
unnamed: R658.1, U541.4 (INOUTA1)
unnamed: R659.2, U542.3 (INOUTB1)
unnamed: R660.1, U543.4 (INOUTA1)
unnamed: R661.2, U544.3 (INOUTB1)
unnamed: R662.1, U545.4 (INOUTA1)
unnamed: R663.1, U540.4 (INOUTA1), U541.3 (INOUTB1)
unnamed: R665.1, U542.4 (INOUTA1), U543.3 (INOUTB1)
unnamed: R667.1, U544.4 (INOUTA1), U545.3 (INOUTB1)
unnamed: R669.1, U541.2 (CATH)
unnamed: R670.1, U543.2 (CATH)
unnamed: R671.1, U545.2 (CATH)
unnamed: R678.2, U540.2 (CATH)
unnamed: R679.2, U542.2 (CATH)
unnamed: R680.2, U544.2 (CATH)

Notes on the sheet:
IGNITION
INJECTION
