jharvey/Cinch_enclosure_template/KICAD_Project/sub_circuits/high_side_drive.sch

## KiCad design KICAD_Project/sub_circuits/high_side_drive.sch (2011-10-27)

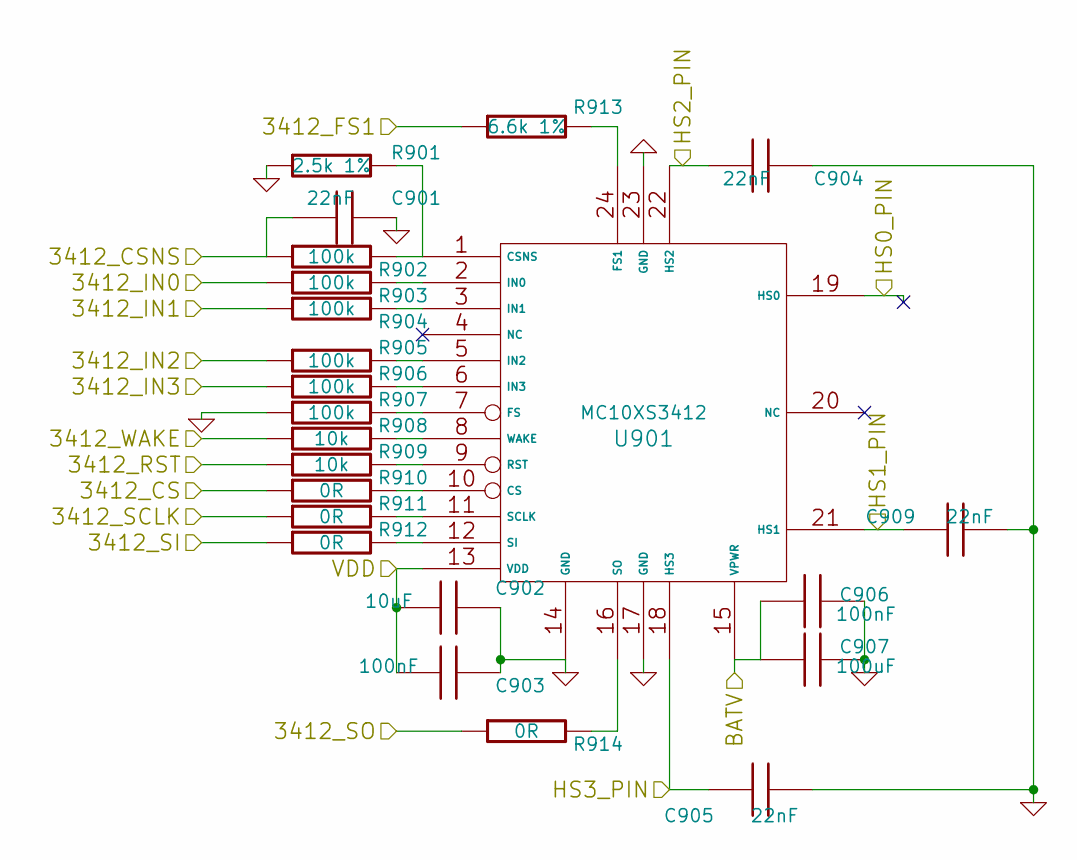
[picture p88: schematic high_side_drive.sch]

Parts:
C901, C904, C909: 22nF; SM0805
C902: 10uF; SM0805; tolerance 10%
C903, C906: 100nF; SM0805
C905: 22nF; SM0805-C1
C907: 100uF; SM0805; tolerance 10%
R901: 2.5k 1%; SM0805; tolerance .1%
R902, R903, R904, R905, R906, R907: 100k; SM0805; tolerance 1%
R908, R909: 10k; SM0805; tolerance 1%
R910, R911, R912, R914: 0R; SM0805; tolerance %
R913: 6.6k 1%; SM0805; tolerance 1%
U901: MC10XS3412; PQFN_24

Connections:
3412_CS: R910.1
3412_CSNS: C901.2, R902.1
3412_FS1: R913.1
3412_IN0: R903.1
3412_IN1: R904.1
3412_IN2: R905.1
3412_IN3: R906.1
3412_RST: R909.1
3412_SCLK: R911.1
3412_SI: R912.1
3412_SO: R914.1
3412_WAKE: R908.1
BATV: C906.1, C907.1, U901.15 (VPWR)
GND: C901.1, C902.1, C903.1, C904.1, C905.2, C906.2, C907.2, C909.2, R901.1, R907.1, U901.14 (GND), U901.17 (GND), U901.23 (GND)
HS0_PIN: U901.19 (HS0)
HS1_PIN: C909.1, U901.21 (HS1)
HS2_PIN: C904.2, U901.22 (HS2)
HS3_PIN: C905.1, U901.18 (HS3)
unnamed: R901.2, R902.2, U901.1 (CSNS)
unnamed: R903.2, U901.2 (IN0)
unnamed: R904.2, U901.3 (IN1)
unnamed: R905.2, U901.5 (IN2)
unnamed: R906.2, U901.6 (IN3)
unnamed: R907.2, U901.7 (FS)
unnamed: R908.2, U901.8 (WAKE)
unnamed: R909.2, U901.9 (RST)
unnamed: R910.2, U901.10 (CS)
unnamed: R911.2, U901.11 (SCLK)
unnamed: R912.2, U901.12 (SI)
unnamed: R913.2, U901.24 (FS1)
unnamed: R914.2, U901.16 (SO)
VDD: C902.2, C903.2, U901.13 (VDD)
