jharvey/Cinch_enclosure_template/KICAD_Project/sub_circuits/low_side_drive.sch

## KiCad design KICAD_Project/sub_circuits/low_side_drive.sch (2011-10-27)

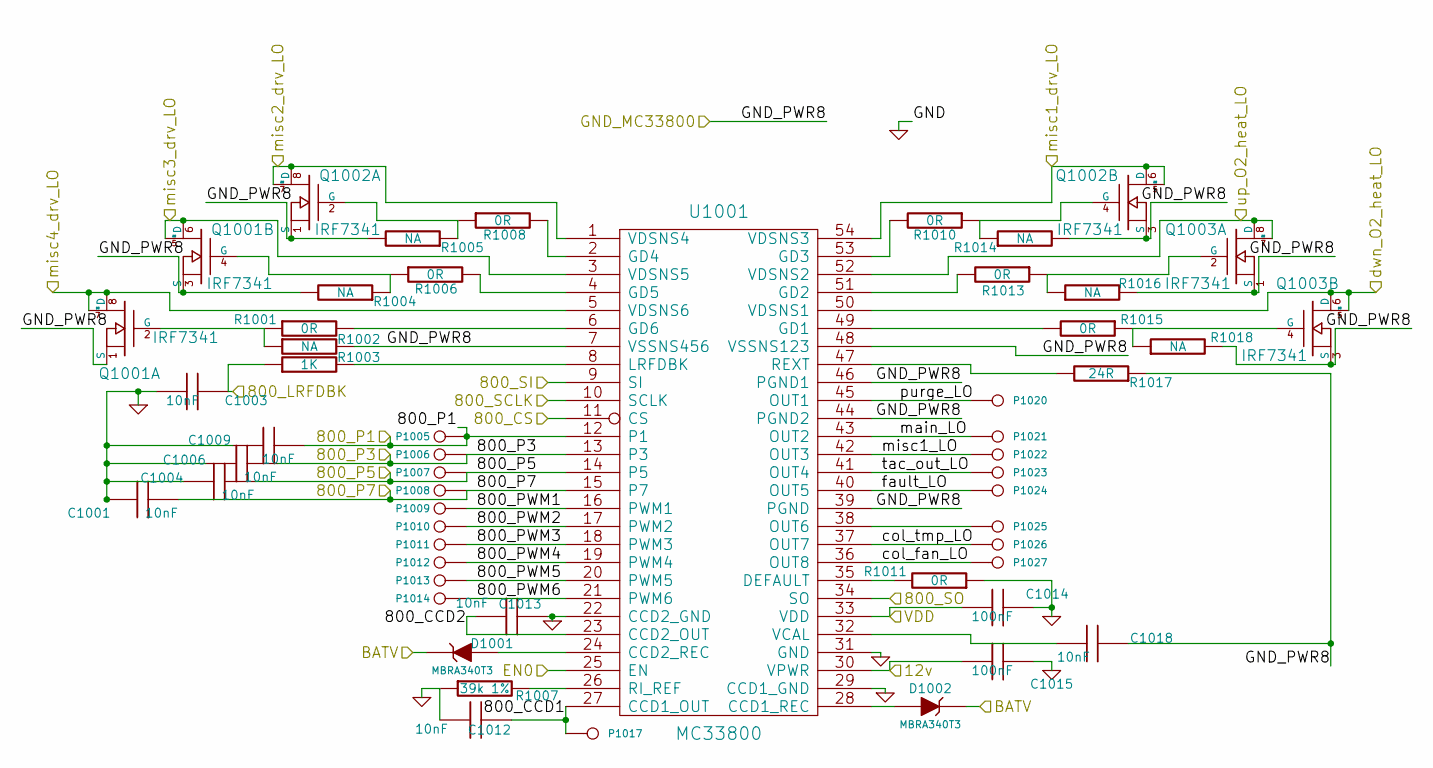
[picture p89: schematic low_side_drive.sch]

Parts:
C1001, C1003, C1004, C1006, C1009, C1012, C1013, C1018: 10nF; SM0805
C1014, C1015: 100nF; SM0805
D1001, D1002: MBRA340T3; SMA
P1005, P1006, P1007, P1008, P1009, P1010, P1011, P1012, P1013, P1014, P1017, P1020, P1021, P1022, P1023, P1024, P1025, P1026, P1027: CONN_1; PINTST
Q1001, Q1002, Q1003: IRF7341; SO8E
R1001, R1006, R1008, R1010, R1011, R1013, R1015: 0R; SM0805; tolerance %
R1002, R1004, R1005, R1014, R1016, R1018: NA; SM0805
R1003: 1K; SM0805; tolerance 1%
R1007: 39k 1%; SM0805
R1017: 24R; SM0805
U1001: MC33800; SOIC54

Connections:
12v: C1015.2, U1001.30 (VPWR)
800_CCD1: C1012.2, P1017.1, U1001.27 (CCD1_OUT)
800_CCD2: C1013.1, U1001.23 (CCD2_OUT)
800_CS: U1001.11 (CS)
800_LRFDBK: C1003.1, R1003.1
800_P1: C1009.2, P1005.1, U1001.12 (P1)
800_P3: C1006.2, P1006.1, U1001.13 (P3)
800_P5: C1004.2, P1007.1, U1001.14 (P5)
800_P7: C1001.2, P1008.1, U1001.15 (P7)
800_PWM1: P1009.1, U1001.16 (PWM1)
800_PWM2: P1010.1, U1001.17 (PWM2)
800_PWM3: P1011.1, U1001.18 (PWM3)
800_PWM4: P1012.1, U1001.19 (PWM4)
800_PWM5: P1013.1, U1001.20 (PWM5)
800_PWM6: P1014.1, U1001.21 (PWM6)
800_SCLK: U1001.10 (SCLK)
800_SI: U1001.9 (SI)
800_SO: U1001.34 (SO)
BATV: D1001.2 (K), D1002.2 (K)
EN0: U1001.25 (EN)
GND: C1001.1, C1003.2, C1004.1, C1006.1, C1009.1, C1012.1, C1013.2, C1014.1, C1015.1, R1007.1, R1011.1, U1001.22 (CCD2_GND), U1001.29 (CCD1_GND), U1001.31 (GND)
GND_MC33800: C1018.1, Q1001.1 (S), Q1001.3 (S), Q1002.1 (S), Q1002.3 (S), Q1003.1 (S), Q1003.3 (S), R1002.2, R1004.2, R1005.2, R1014.2, R1016.2, R1017.1, R1018.2, U1001.7 (VSSNS456), U1001.39 (PGND), U1001.44 (PGND2), U1001.46 (PGND1), U1001.48 (VSSNS123)
unnamed: C1018.2, U1001.32 (VCAL)
unnamed: D1001.1 (A), U1001.24 (CCD2_REC)
unnamed: D1002.1 (A), U1001.28 (CCD1_REC)
unnamed: P1025.1, U1001.38 (OUT6)
unnamed: Q1001.2 (G), R1001.1, R1002.1
unnamed: Q1001.4 (G), R1004.1, R1006.1
unnamed: Q1002.2 (G), R1005.1, R1008.1
unnamed: Q1002.4 (G), R1010.1, R1014.1
unnamed: Q1003.2 (G), R1013.1, R1016.1
unnamed: Q1003.4 (G), R1015.1, R1018.1
unnamed: R1001.2, U1001.6 (GD6)
unnamed: R1003.2, U1001.8 (LRFDBK)
unnamed: R1006.2, U1001.4 (GD5)
unnamed: R1007.2, U1001.26 (RI_REF)
unnamed: R1008.2, U1001.2 (GD4)
unnamed: R1010.2, U1001.53 (GD3)
unnamed: R1011.2, U1001.35 (DEFAULT)
unnamed: R1013.2, U1001.51 (GD2)
unnamed: R1015.2, U1001.49 (GD1)
unnamed: R1017.2, U1001.47 (REXT)
VDD: C1014.2, U1001.33 (VDD)
col_fan_LO: P1027.1, U1001.36 (OUT8)
col_tmp_LO: P1026.1, U1001.37 (OUT7)
dwn_O2_heat_LO: Q1003.5 (D2), Q1003.6 (D), U1001.50 (VDSNS1)
fault_LO: P1024.1, U1001.40 (OUT5)
main_LO: P1021.1, U1001.43 (OUT2)
misc1_LO: P1022.1, U1001.42 (OUT3)
misc1_drv_LO: Q1002.5 (D2), Q1002.6 (D), U1001.54 (VDSNS3)
misc2_drv_LO: Q1002.7 (D2), Q1002.8 (D), U1001.1 (VDSNS4)
misc3_drv_LO: Q1001.5 (D2), Q1001.6 (D), U1001.3 (VDSNS5)
misc4_drv_LO: Q1001.7 (D2), Q1001.8 (D), U1001.5 (VDSNS6)
purge_LO: P1020.1, U1001.45 (OUT1)
tac_out_LO: P1023.1, U1001.41 (OUT4)
up_O2_heat_LO: Q1003.7 (D2), Q1003.8 (D), U1001.52 (VDSNS2)
