jharvey/Cinch_enclosure_template/KICAD_Project/sub_circuits/pin_protect.sch

## KiCad design KICAD_Project/sub_circuits/pin_protect.sch (2011-10-27)

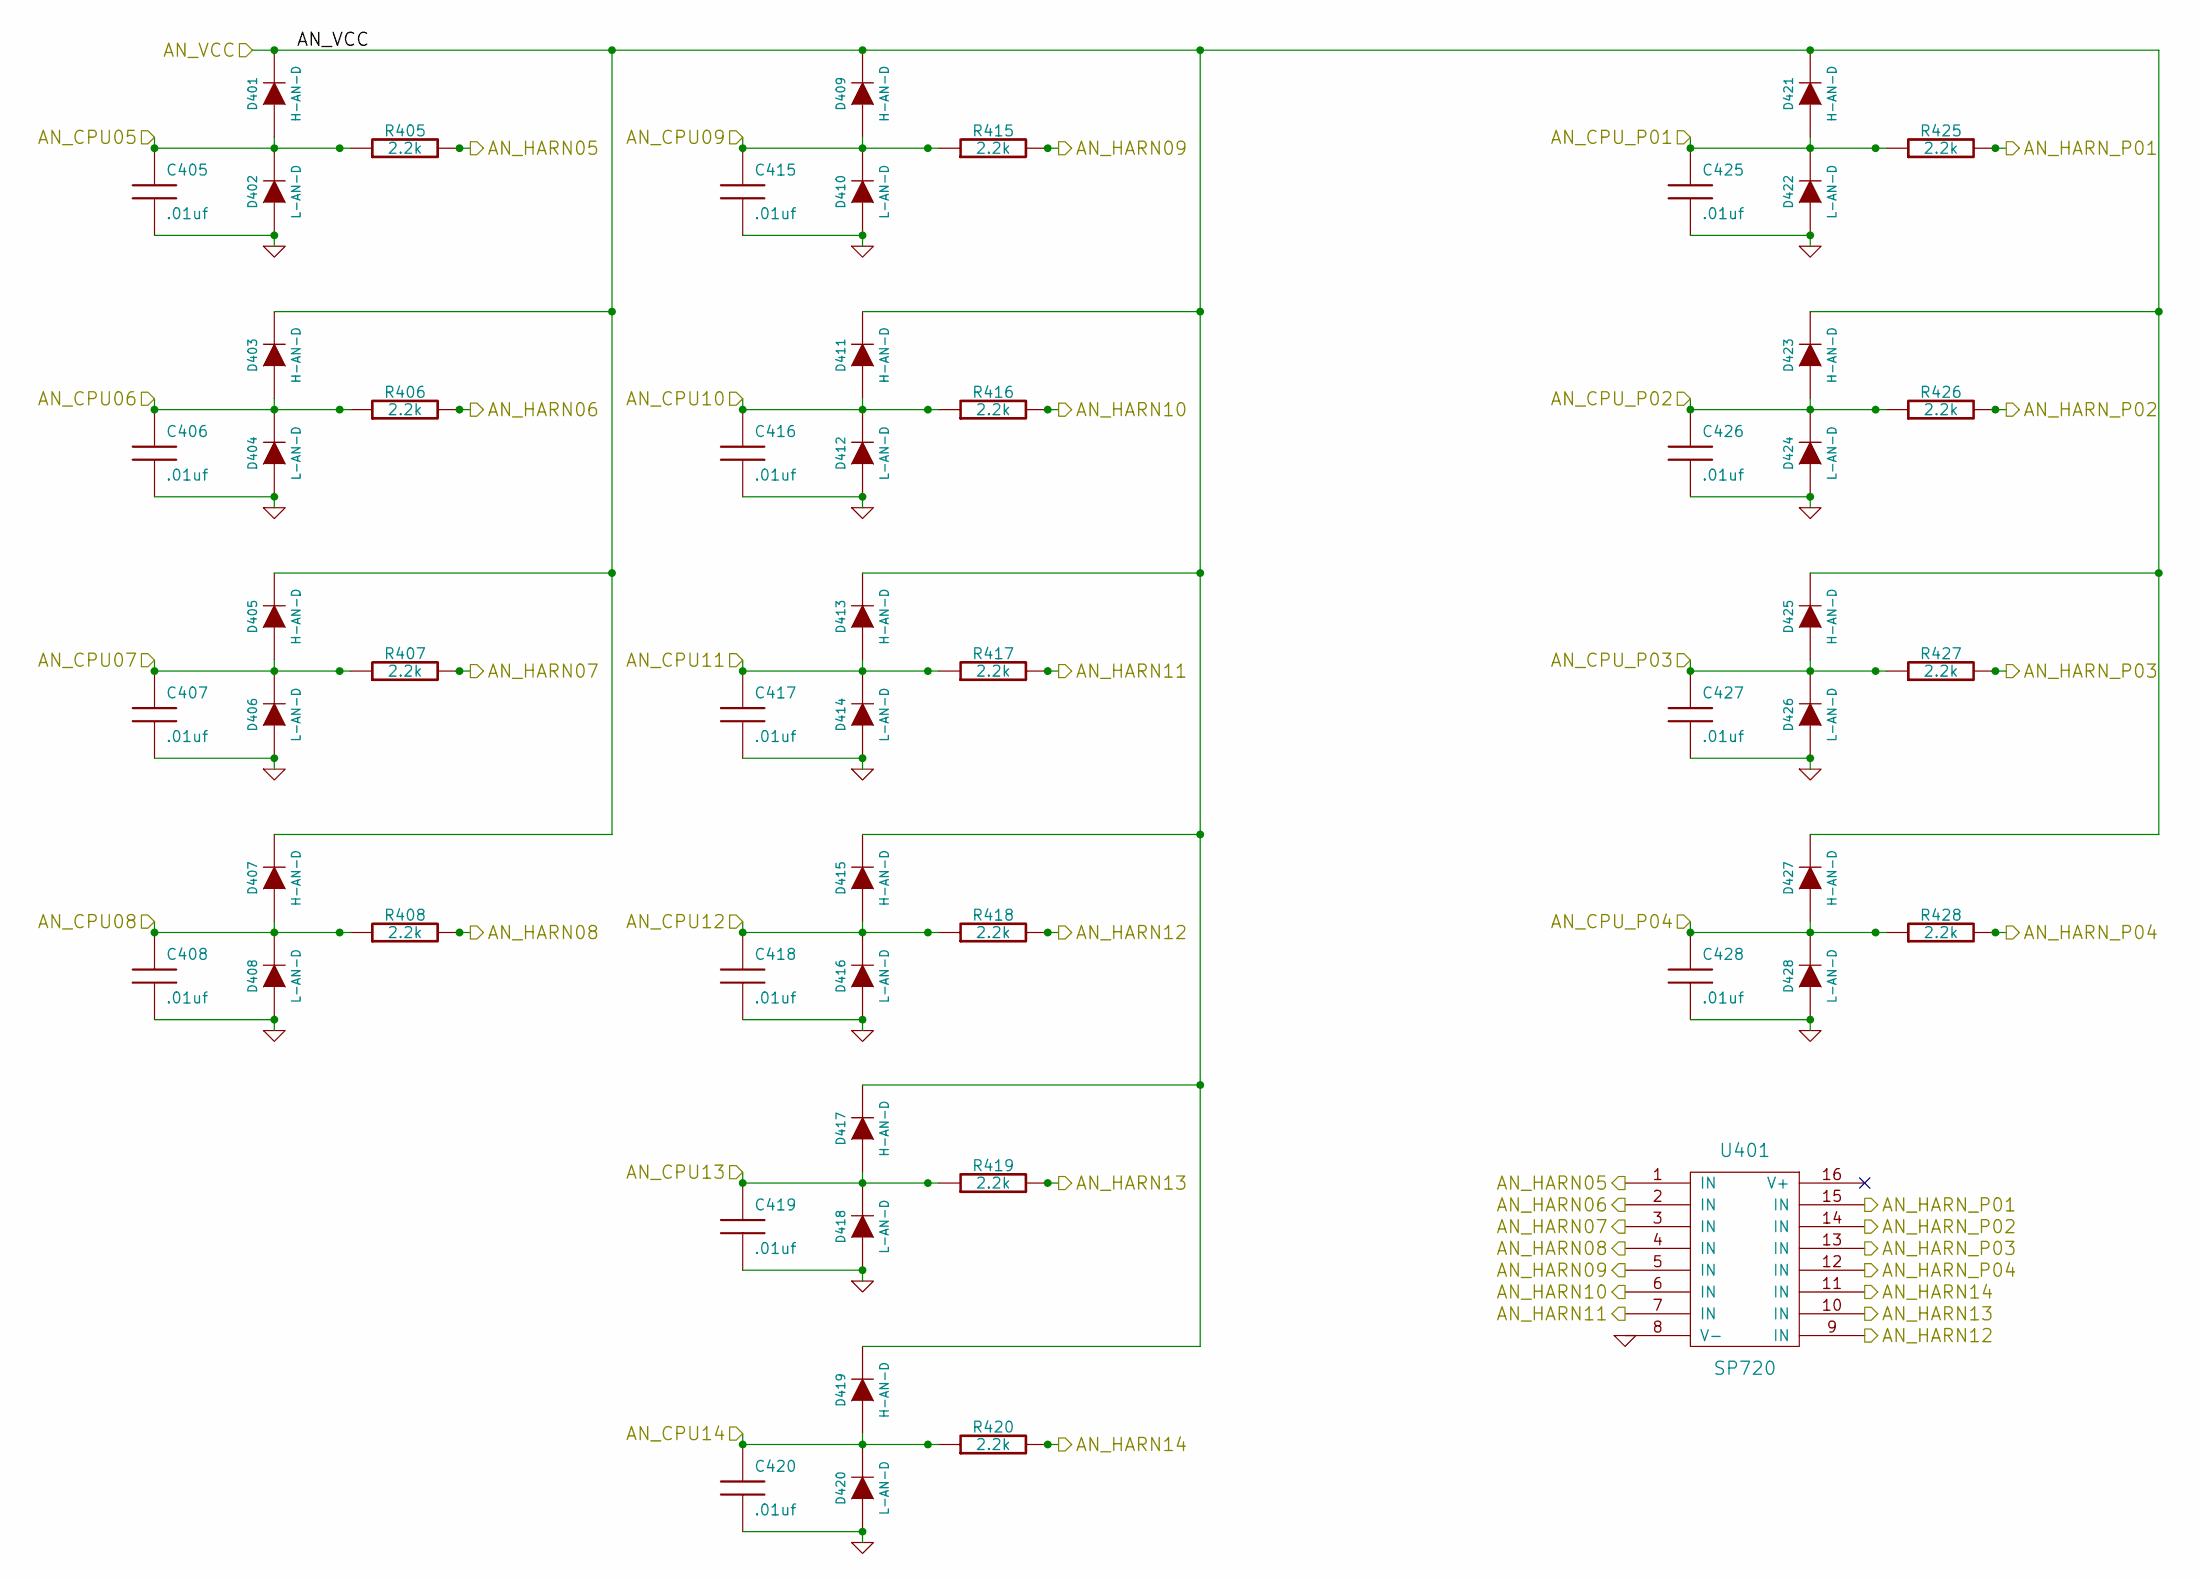
[picture p90: schematic pin_protect.sch]

Parts:
C405, C406, C407, C408, C415, C416, C417, C418, C419, C420, C425, C426, C427, C428: .01uf; SM0805
D401, D403, D405, D407, D409, D411, D413, D415, D417, D419, D421, D423, D425, D427: H-AN-D; SOD-123
D402, D404, D406, D408, D410, D412, D414, D416, D418, D420, D422, D424, D426, D428: L-AN-D; SOD-123
R405, R406, R407, R408, R415, R416, R417, R418, R419, R420, R425, R426, R427, R428: 2.2k; SM0805
U401: SP720; SO16E

Connections:
AN_CPU05: C405.1, D401.1 (A), D402.2 (K), R405.1
AN_CPU06: C406.1, D403.1 (A), D404.2 (K), R406.1
AN_CPU07: C407.1, D405.1 (A), D406.2 (K), R407.1
AN_CPU08: C408.1, D407.1 (A), D408.2 (K), R408.1
AN_CPU09: C415.1, D409.1 (A), D410.2 (K), R415.1
AN_CPU10: C416.1, D411.1 (A), D412.2 (K), R416.1
AN_CPU11: C417.1, D413.1 (A), D414.2 (K), R417.1
AN_CPU12: C418.1, D415.1 (A), D416.2 (K), R418.1
AN_CPU13: C419.1, D417.1 (A), D418.2 (K), R419.1
AN_CPU14: C420.1, D419.1 (A), D420.2 (K), R420.1
AN_CPU_P01: C425.1, D421.1 (A), D422.2 (K), R425.1
AN_CPU_P02: C426.1, D423.1 (A), D424.2 (K), R426.1
AN_CPU_P03: C427.1, D425.1 (A), D426.2 (K), R427.1
AN_CPU_P04: C428.1, D427.1 (A), D428.2 (K), R428.1
AN_HARN05: R405.2, U401.1 (IN)
AN_HARN06: R406.2, U401.2 (IN)
AN_HARN07: R407.2, U401.3 (IN)
AN_HARN08: R408.2, U401.4 (IN)
AN_HARN09: R415.2, U401.5 (IN)
AN_HARN10: R416.2, U401.6 (IN)
AN_HARN11: R417.2, U401.7 (IN)
AN_HARN12: R418.2, U401.9 (IN)
AN_HARN13: R419.2, U401.10 (IN)
AN_HARN14: R420.2, U401.11 (IN)
AN_HARN_P01: R425.2, U401.15 (IN)
AN_HARN_P02: R426.2, U401.14 (IN)
AN_HARN_P03: R427.2, U401.13 (IN)
AN_HARN_P04: R428.2, U401.12 (IN)
AN_VCC: D401.2 (K), D403.2 (K), D405.2 (K), D407.2 (K), D409.2 (K), D411.2 (K), D413.2 (K), D415.2 (K), D417.2 (K), D419.2 (K), D421.2 (K), D423.2 (K), D425.2 (K), D427.2 (K)
GND: C405.2, C406.2, C407.2, C408.2, C415.2, C416.2, C417.2, C418.2, C419.2, C420.2, C425.2, C426.2, C427.2, C428.2, D402.1 (A), D404.1 (A), D406.1 (A), D408.1 (A), D410.1 (A), D412.1 (A), D414.1 (A), D416.1 (A), D418.1 (A), D420.1 (A), D422.1 (A), D424.1 (A), D426.1 (A), D428.1 (A), U401.8 (V-)
