jharvey/Cinch_enclosure_template/KICAD_Project/sub_circuits/power_reg1.sch

## KiCad design KICAD_Project/sub_circuits/power_reg1.sch (2011-09-04)

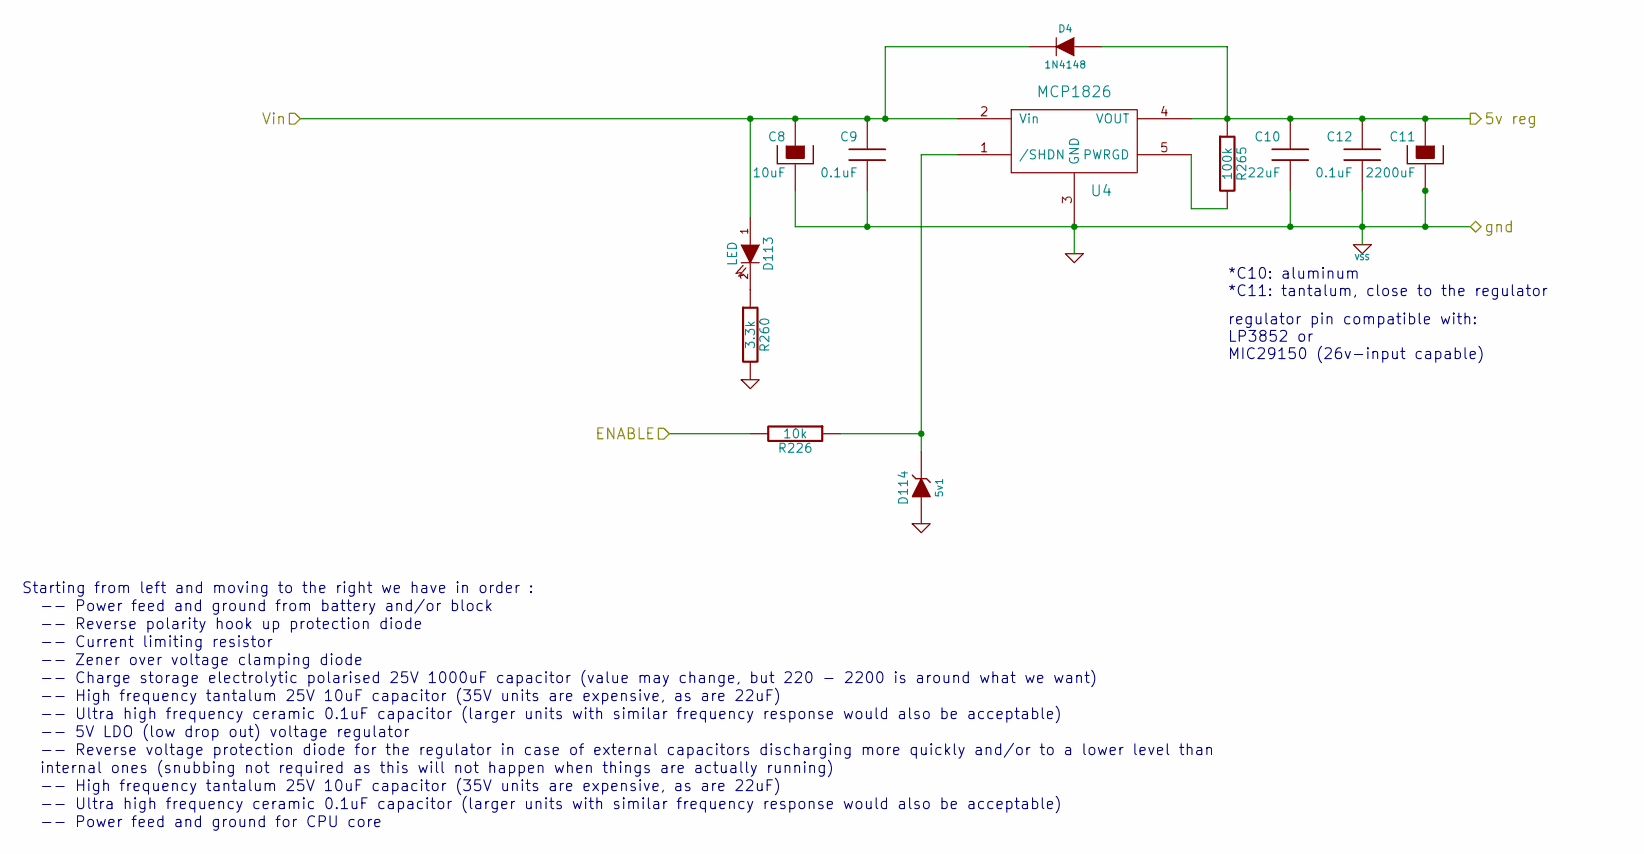
[picture p91: schematic power_reg1.sch]

Parts:
C8: 10uF; SM0805-C1; tolerance 10%
C9, C12: 0.1uF; SM0805-C1; tolerance 10%
C10: 22uF; SM2512; mfg# TAJC226M016RNJ
C11: 2200uF; C1V8; mfg# EKZE6R3ELL222MJ25S
D4: 1N4148; SOD-123; mfg# 1N4148W-TP
D113: LED; LED-0805
D114: 5v1; SOD-123
R226: 10k; SM0805; tolerance 1%
R260: 3.3k; SM0805; tolerance 5%; mfg# RMCF0805JT3K30CT
R265: 100k; SM0805; tolerance 1%
U4: MCP1826; DPAK5

Connections:
5v reg: C10.1, C11.1, C12.1, D4.1 (A), R265.1, U4.4 (VOUT)
ENABLE: R226.2
unnamed: D113.2 (K), R260.1
unnamed: D114.2 (K), R226.1, U4.1 (/SHDN)
unnamed: R265.2, U4.5 (PWRGD)
Vin: C8.1, C9.1, D4.2 (K), D113.1 (A), U4.2 (Vin)
gnd: C8.2, C9.2, C10.2, C11.2, C12.2, D114.1 (A), R260.2, U4.3 (GND)

Notes on the sheet:
regulator pin compatible with: LP3852 or MIC29150 (26v-input capable)
*C10: aluminum *C11: tantalum, close to the regulator
Starting from left and moving to the right we have in order :
-- Power feed and ground from battery and/or block
-- Reverse polarity hook up protection diode
-- Current limiting resistor
-- Zener over voltage clamping diode
-- Charge storage electrolytic polarised 25V 1000uF capacitor (value may change, but 220 - 2200 is around what we want)
-- High frequency tantalum 25V 10uF capacitor (35V units are expensive, as are 22uF)
-- Ultra high frequency ceramic 0.1uF capacitor (larger units with similar frequency response would also be acceptable)
-- 5V LDO (low drop out) voltage regulator
-- Reverse voltage protection diode for the regulator in case of external capacitors discharging more quickly and/or to a lower level than
internal ones (snubbing not required as this will not happen when things are actually running)
-- Power feed and ground for CPU core
