jharvey/Cinch_enclosure_template/KICAD_Project/sub_circuits/power_reg2.sch

## KiCad design KICAD_Project/sub_circuits/power_reg2.sch (2011-08-30)

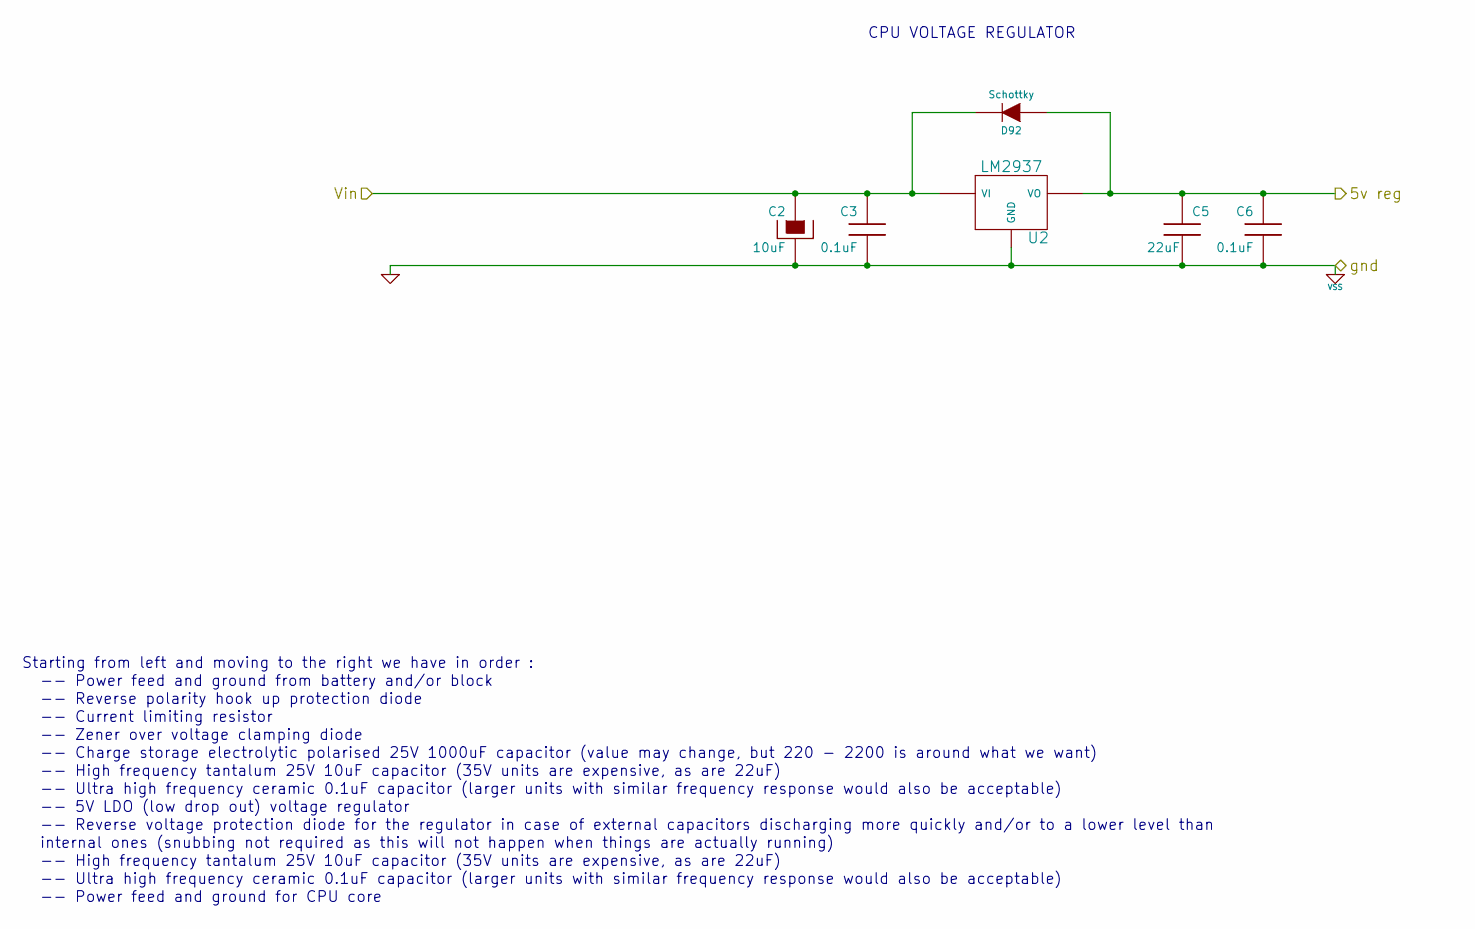
[picture p92: schematic power_reg2.sch]

Parts:
C2: 10uF; SM0805-C1; tolerance 10%
C3, C6: 0.1uF; SM0805-C1; tolerance 10%
C5: 22uF; SM2512; mfg# TAJC226M016RNJ
D92: Schottky; SOD-123; mfg# 1N4148W-TP
U2: LM2937; SOT223; tolerance .05%

Connections:
5v reg: C5.1, C6.1, D92.1 (A), U2.VO
Vin: C2.1, C3.1, D92.2 (K), U2.VI
gnd: C2.2, C3.2, C5.2, C6.2, U2.GND

Notes on the sheet:
CPU VOLTAGE REGULATOR
Starting from left and moving to the right we have in order :
-- Power feed and ground from battery and/or block
-- Reverse polarity hook up protection diode
-- Current limiting resistor
-- Zener over voltage clamping diode
-- Charge storage electrolytic polarised 25V 1000uF capacitor (value may change, but 220 - 2200 is around what we want)
-- High frequency tantalum 25V 10uF capacitor (35V units are expensive, as are 22uF)
-- Ultra high frequency ceramic 0.1uF capacitor (larger units with similar frequency response would also be acceptable)
-- 5V LDO (low drop out) voltage regulator
-- Reverse voltage protection diode for the regulator in case of external capacitors discharging more quickly and/or to a lower level than
internal ones (snubbing not required as this will not happen when things are actually running)
-- Power feed and ground for CPU core
