jharvey/Cinch_enclosure_template/KICAD_Project/sub_circuits/power_reg.sch

## KiCad design KICAD_Project/sub_circuits/power_reg.sch (2011-10-27)

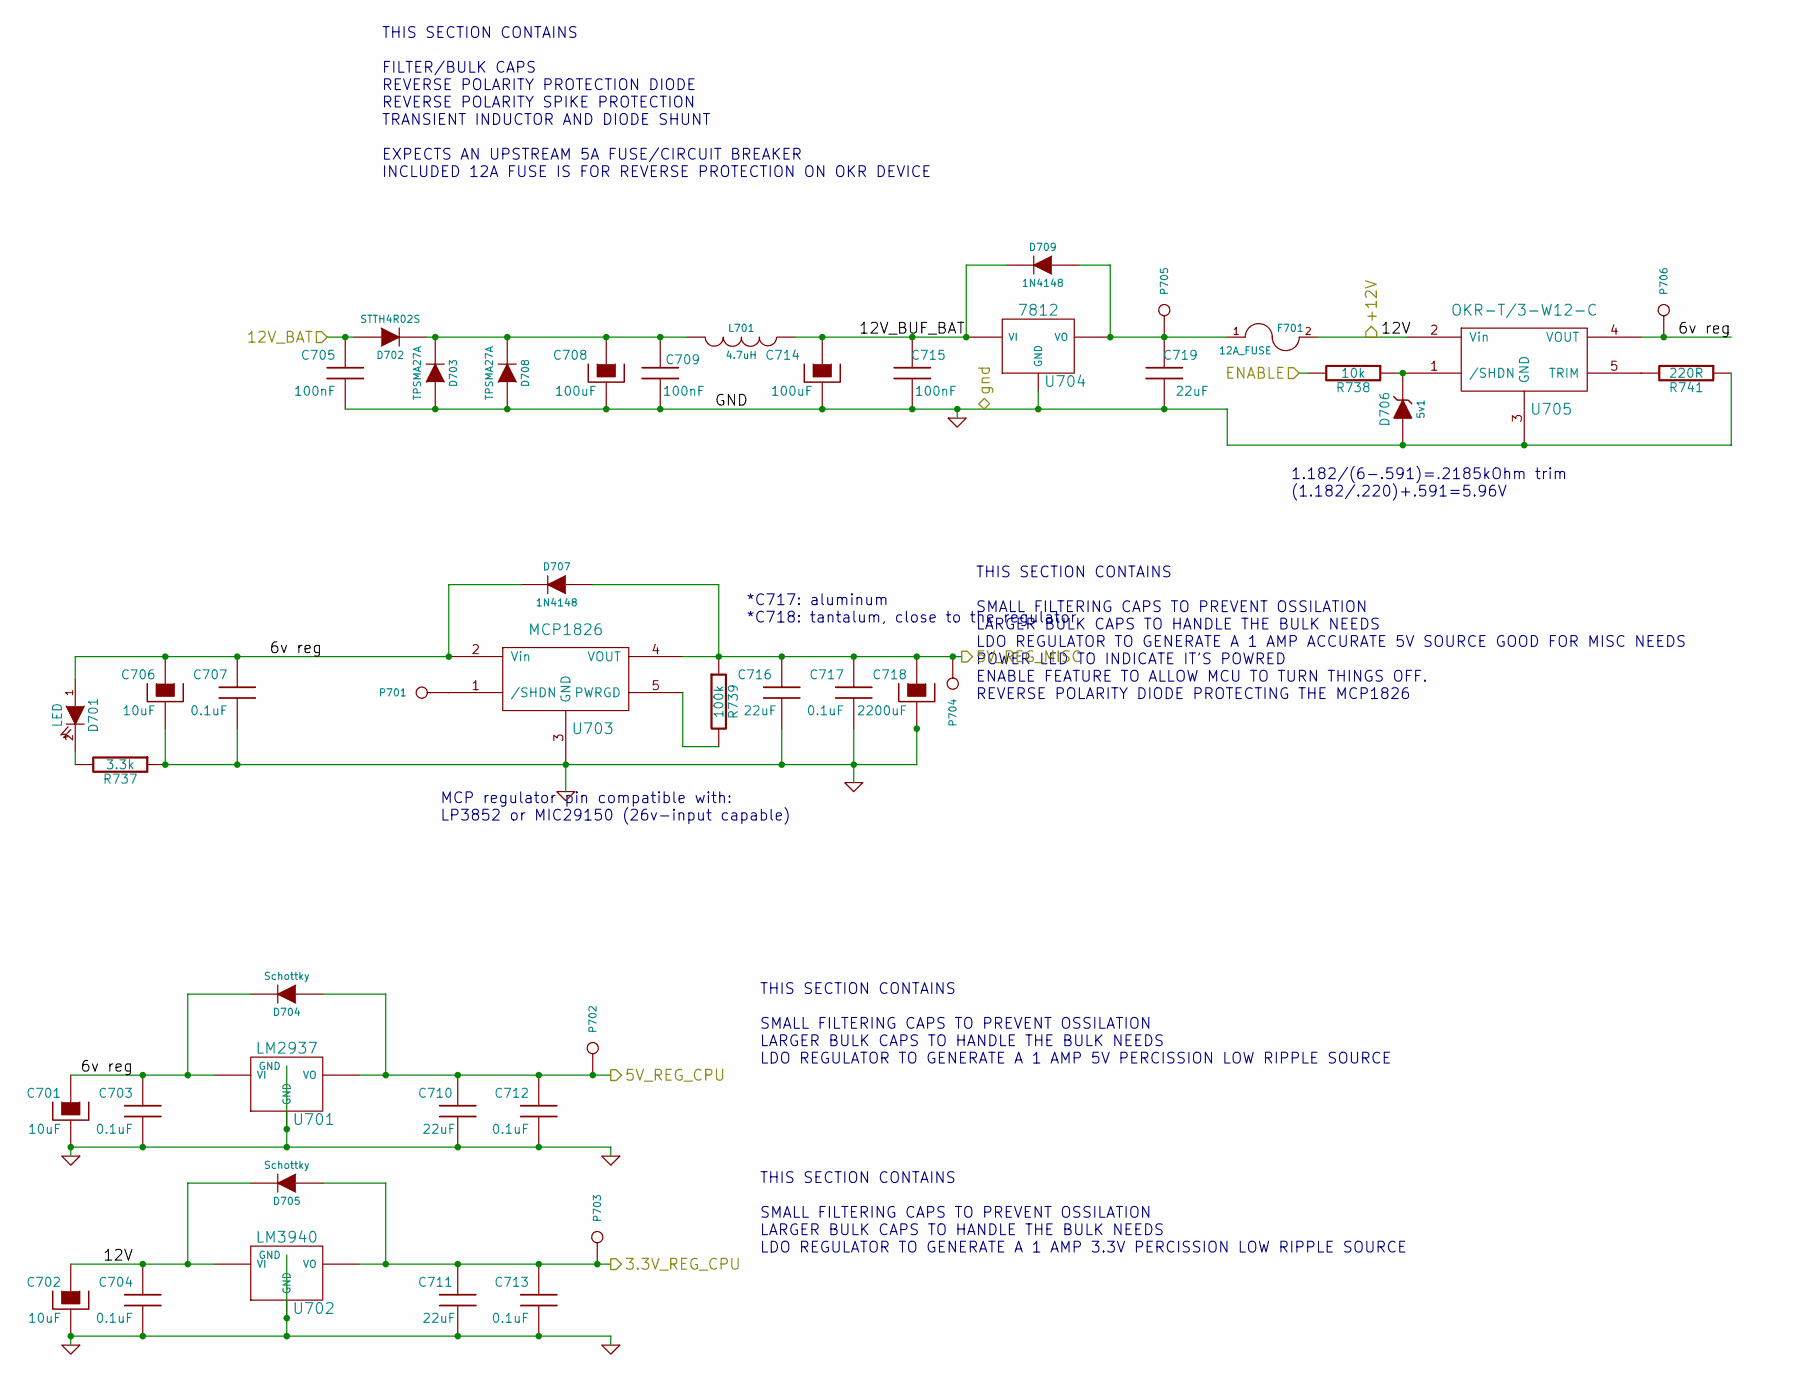
[picture p93: schematic power_reg.sch]

Parts:
C701, C702, C706: 10uF; SM0805; tolerance 10%
C703, C704, C707, C712, C713, C717: 0.1uF; SM0805; tolerance 10%
C705, C709, C715: 100nF; SM0805
C708, C714: 100uF; SM0805; tolerance 10%
C710, C711, C716: 22uF; SM2512; mfg# TAJC226M016RNJ
C718: 2200uF; C1V8; mfg# EKZE6R3ELL222MJ25S
C719: 22uF; SM1210
D701: LED; LED-0805
D702: STTH4R02S; D4-SMB; mfg# STTH4R02U
D703, D708: TPSMA27A; DO214; voltage(V) 37.5; mfg# TPSMA27A-E3/61T
D704, D705: Schottky; SOD-123; mfg# 1N4148W-TP
D706: 5v1; SOD-123
D707, D709: 1N4148; SOD-123; mfg# 1N4148W-TP
F701: 12A_FUSE; SIL-2
L701: 4.7uH; SM4.7uH
P701, P702, P703, P704, P705, P706: CONN_1; PINTST
R737: 3.3k; SM0805; tolerance 5%; mfg# RMCF0805JT3K30CT
R738: 10k; SM0805; tolerance 1%
R739: 100k; SM0805; tolerance 1%
R741: 220R; SM0805; tolerance 1%
U701: LM2937; SOT223; tolerance .05%
U702: LM3940; SOT223; tolerance ?%
U703: MCP1826; DPAK5
U704: 7812; DPAK2
U705: OKR-T/3-W12-C; OKR-T/3

Connections:
3.3V_REG_CPU: C711.1, C713.1, D705.1 (A), P703.1, U702.3 (VO)
5V_REG_CPU: C710.1, C712.1, D704.1 (A), P702.1, U701.3 (VO)
5V_REG_MISC: C716.1, C717.1, C718.1, D707.1 (A), P704.1, R739.1, U703.4 (VOUT)
6v reg: C701.1, C703.1, C706.1, C707.1, D701.1 (A), D704.2 (K), D707.2 (K), P706.1, U701.1 (VI), U703.2 (Vin), U705.4 (VOUT)
12V_BAT: C705.1, D702.1 (A)
12V_BUF_BAT: C714.1, C715.1, D709.2 (K), L701.1, U704.1 (VI)
+12V: C702.1, C704.1, D705.2 (K), F701.2, U702.1 (VI), U705.2 (Vin)
ENABLE: R738.2
unnamed: C708.1, C709.1, D702.2 (K), D703.2 (K), D708.2 (K), L701.2
unnamed: C719.1, D709.1 (A), F701.1, P705.1, U704.3 (VO)
unnamed: D701.2 (K), R737.2
unnamed: D706.2 (K), R738.1, U705.1 (/SHDN)
unnamed: P701.1, U703.1 (/SHDN)
unnamed: R739.2, U703.5 (PWRGD)
unnamed: R741.2, U705.5 (TRIM)
gnd: C701.2, C702.2, C703.2, C704.2, C705.2, C706.2, C707.2, C708.2, C709.2, C710.2, C711.2, C712.2, C713.2, C714.2, C715.2, C716.2, C717.2, C718.2, C719.2, D703.1 (A), D706.1 (A), D708.1 (A), R737.1, R741.1, U701.2 (GND), U701.4 (GND), U702.2 (GND), U702.4 (GND), U703.3 (GND), U704.2 (GND), U705.3 (GND)

Notes on the sheet:
*C717: aluminum *C718: tantalum, close to the regulator
1.182/(6-.591)=.2185kOhm trim (1.182/.220)+.591=5.96V
THIS SECTION CONTAINS SMALL FILTERING CAPS TO PREVENT OSSILATION LARGER BULK CAPS TO HANDLE THE BULK NEEDS LDO REGULATOR TO GENERATE A 1 AMP 3.3V PERCISSION LOW RIPPLE SOURCE
THIS SECTION CONTAINS SMALL FILTERING CAPS TO PREVENT OSSILATION LARGER BULK CAPS TO HANDLE THE BULK NEEDS LDO REGULATOR TO GENERATE A 1 AMP ACCURATE 5V SOURCE GOOD FOR MISC NEEDS POWER LED TO INDICATE IT'S POWRED ENABLE FEATURE TO ALLOW MCU TO TURN THINGS OFF. REVERSE POLARITY DIODE PROTECTING THE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
THIS SECTION CONTAINS SMALL FILTERING CAPS TO PREVENT OSSILATION LARGER BULK CAPS TO HANDLE THE BULK NEEDS LDO REGULATOR TO GENERATE A 1 AMP 5V PERCISSION LOW RIPPLE SOURCE
THIS SECTION CONTAINS FILTER/BULK CAPS REVERSE POLARITY PROTECTION DIODE REVERSE POLARITY SPIKE PROTECTION TRANSIENT INDUCTOR AND DIODE SHUNT EXPECTS AN UPSTREAM 5A FUSE/CIRCUIT BREAKER INCLUDED 12A FUSE IS FOR REVERSE PROTECTION ON OKR DEVICE
MCP regulator pin compatible with: LP3852 or MIC29150 (26v-input capable)
