jharvey/Cinch_enclosure_template/KICAD_Project/sub_circuits/power_reg_s1.sch

## KiCad design KICAD_Project/sub_circuits/power_reg_s1.sch (2011-10-16)

Schematic: power_reg_s1.sch

Parts:
C134, C138, C141: 100nF; SM0805
C135, C139: 100uF; SM0805-C1; tolerance 10%
C136: 5.6nF; SM0805-C1
C137: 27pF; SM0805-C1
C140: T495X337K010ATE035; SM0805-C1
C143: 10uF; SM0805-C1; tolerance 10%
C144: 10nF; SM0805
D117: STTH4R02S; D4-SMB; mfg# STTH4R02U
D118: TPSMA27A; DO214; voltage(V) 37.5; mfg# TPSMA27A-E3/61T
D119: STPS5L25; D4-SMB; MFG# STPS5L25B-TR
L1: 4.7uH; SM4.7uH
L2: DR125-330-R; SM100uH; tolerance 20%
R272: 3.6K 1%; SM0805
R273: 39k 1%; SM0805
R274: 13K 1%; SM0805
U35: L5973D; SO8E; MFG# L5973D013TR

Notes on the sheet:
MBRA210LT3G
* Its a 2A IC, plenty of horsepower for both regs * chack availability of diode, cap and inductor
