jharvey/Cinch_enclosure_template/KICAD_Project/sub_circuits/stepper_L297.sch

## KiCad design KICAD_Project/sub_circuits/stepper_L297.sch (2011-10-16)

Schematic: stepper_L297.sch

Parts:
C801, C804: 470uF; SM0805-C1
C802: 10uF; SM0805-C1; tolerance 10%
C803, C805: 100nF; SM0805
D801, D802, D803, D804, D805, D806, D807, D808: DIODE; D4-SMB
P801, P802, P803, P804, P805: CONN_1; PINTST
R801, R802, R803, R804, R806: 100K; SM0805; tolerance %
R805, R807: 0R5; SM0805; tolerance %
R808: 22K; SM0805; tolerance %
U801: L298N; SO20_POWER
U802: L297; SO20L
