jharvey/Cinch_enclosure_template/KICAD_Project/sub_circuits/stepper_mc33879.sch

## KiCad design KICAD_Project/sub_circuits/stepper_mc33879.sch (2011-10-16)

Schematic: stepper_mc33879.sch

Parts:
C801: 100nF; SM0805
C802, C803, C804: 10uF; SM0805-C1; tolerance 10%
P801, P802, P803, P804: CONN_1; PINTST
R801, R802, R803, R804, R805, R806, R807, R808, R809, R810, R811, R812: 0R; SM0805; tolerance %
U801: MC33879; SOIC32

Notes on the sheet:
install or jumpers for stepper motor driver.
